sql-monk/batman/mechanical/cad/cable-modular-assembly.png

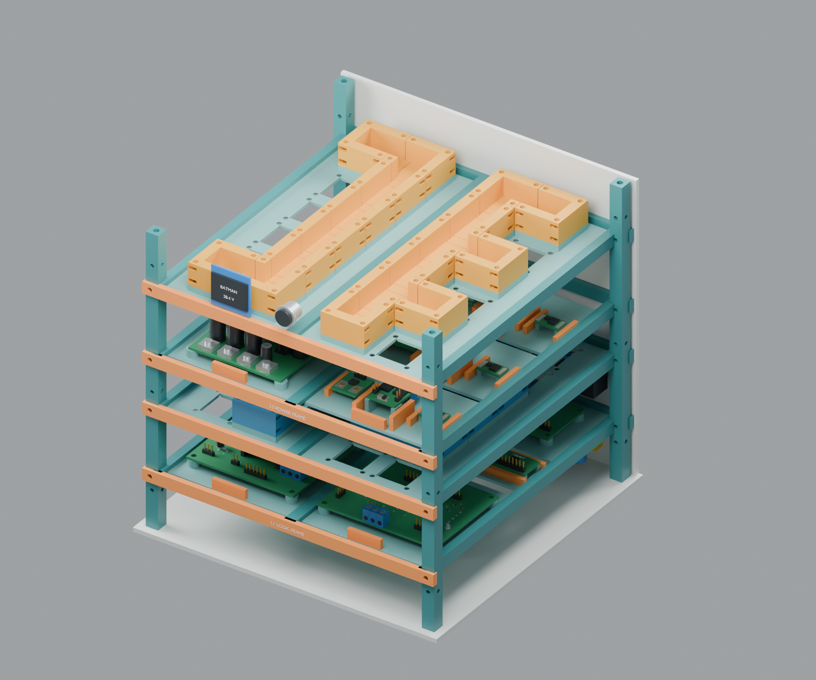
mechanical/cad/cable-modular-assembly.png
