sql-monk/batman/hardware/batman/reports/refinement/A/jumpers.csv

Ref | Net | A_X1_mm | A_Y1_mm | X2_mm | Y2_mm | Wire_cut_min_mm | End1 | End2
WA1 | +3V3 | 28.0 | 12.0 | 18.0 | 39.94 | 29.68 | existing pad | existing pad
WA2 | GND | 64.0 | 14.54 | 72.0 | 14.54 | 8.0 | existing pad | existing pad
WA3 | GND | 14.96 | 34.0 | 20.54 | 39.94 | 8.15 | existing pad | existing pad
WA4 | SCL | 64.0 | 17.08 | 72.0 | 17.08 | 8.0 | existing pad | existing pad
WA5 | SCL | 72.0 | 17.08 | 72.0 | 27.9 | 10.82 | existing pad | existing pad
