sql-monk/batman/docs/firmware.md

# Прошивка — вимоги

Що прошивка ESP32 має робити, у якому порядку і з якими порогами. Піни — connections.md, DPS — dps5015-modbus.md, вимірювання — measurement.md, протокол — protocol.md. Середовище: PlatformIO, Arduino-ESP32 (ESP-IDF під капотом); бібліотеки: `ModbusMaster`, `Adafruit_ADS1X15` або `RobTillaart/ADS1X15`, `OneWire` + `DallasTemperature`, `U8g2`, `ESPAsyncWebServer` або вбудований `WebServer`, `ArduinoJson`, `ESPmDNS`, `Update`.

## Безпечний старт

Порядок у `setup()` — саме такий:

1. Усі керуючі виходи (`SW1_ON`, `SW2_ON`, `K1`, `K2`) — `digitalWrite(LOW)` **до** `pinMode(OUTPUT)`; `SENS_PWR` — HIGH (датчики вимкнені). Апаратно все й так у OFF (Hi-Z + підтяжки), це лише підтвердження.
2. Watchdog задачі (10 с) і апаратний (30 с).
3. NVS: конфіг, лічильники, калібрування, збережений стан ключів і `sink`.
4. UART2, I2C 100 кГц; перевірити **обидва** ADS1115 (0x48, 0x49), OLED 0x3C, 1-Wire. Відсутній будь-який АЦП → вимірювання недійсні, автоматичний заряд не дозволяти; не підставляти нулі замість показань.
5. `SENS_PWR` ← LOW (датчики живляться), 100 мс, перший блок відліків.
6. DPS: читання блоку; якщо `ONOFF = 1` — негайно `ONOFF ← 0` (DPS міг лишитися ввімкненим після нашого ресету).
7. Відновлення стану ключів **з NVS**, якщо з моменту збереження минуло < 60 с (uptime із RTC-пам'яті ресету) — інакше обидва OFF. Заряд після ресету **не відновлюється** автоматично, стан → IDLE, подія `boot` з `restored`.
8. Wi-Fi (STA; якщо немає конфігу або 60 с без зв'язку — AP `batman-<id>` зі сторінкою налаштування), mDNS, HTTP-сервер, UDP-слухач.
9. Основний цикл.

Ресет не змінює стану ключів (перевірка в 4.1 плану).

## Задачі й пріоритети

| Задача | Період | Що |
|---|---|---|
| `acq` (ядро 1, високий пріоритет) | за готовністю ADS1115 (~470 Гц) | відлік → інтегрування → буфер середніх |
| `ctrl` (ядро 1) | 500 мс | Modbus-опитування, стейт-машина, перехресні перевірки, ключі |
| `load_acq` | 100 мс | ADS1115 0x49: A0 I_LOAD, A1 U_LOAD, по готовності кожного single-shot; обидва показання 10 Гц |
| `slow` (ядро 0) | 1 с | DS18B20, OLED, кнопка, NVS за розкладом |
| `net` (ядро 0) | за подіями | HTTP-сервер, телеметрія на sink, буфер, mDNS/UDP, OTA |

Доступ до спільних даних — через один м'ютекс на «знімок стану»; `acq` пише в подвійний буфер. Для 0x48/0x49 окремі об'єкти драйвера, спільні I²C-транзакції з OLED серіалізовані. GPIO34/39 NC, ADC ESP більше не використовується. У триконтактній ревізії немає FAULT ISR. **SENS_PWR = GPIO33 (J1.8), не GPIO14; GPIO14/J1.12 тепер NC.** Перед `pinMode(OUTPUT)` записати HIGH; LOW вмикає датчики. Прошивка зі старим призначенням GPIO14 не керуватиме живленням датчиків. Опитування струму не є незалежним швидким апаратним захистом. Q3 на C одержує SENS_PWR через CB2; на початку й після ввімкнення живлення датчиків не використовувати перехідні відліки.

## Стейт-машина

Стани верхнього рівня:

| Стан | Що відбувається | DPS | K1/K2 |
|---|---|---|---|
| `IDLE` | нічого не заряджається; ключі за командами/порогами | OFF | розімкнені |
| `CHG_B1_CC` / `CHG_B2_BULK` | постійний струм `i_cc` / `i_bulk` | ON, I-SET = профіль, U-SET підтягується за U_BX | KX замкнене |
| `CHG_B1_CV` / `CHG_B2_ABS` | утримання `u_cv` / `u_abs` на вузлі B; струм падає | ON | KX |
| `CHG_B2_FLOAT` | свинець: `u_float` з термокомпенсацією; без обмеження часу | ON | K2 |
| `REST` | пауза між зарядами (`policy.rest_min`) | OFF | розімкнені |
| `NO_INPUT` | БЖ відсутній (UIN < 30 В) | — | розімкнені |
| `FAULT` | аварія; підстан у `fault.code` | OFF | розімкнені |

Переходи:

| З | У | Умова |
|---|---|---|
| IDLE | CHG_Bx_* | команда `charge_start`, або `policy.auto` і гілка x — з найнижчим SoC (або за `charge_order`) і не в REST; **і** T_x у межах (`t_min`…`t_max`), **і** DPS ok, **і** UIN ≥ 31 В |
| CHG_B1_CC | CHG_B1_CV | U_B1 ≥ `u_cv` − 0,05 В (з ADS1115, середнє 2 с) |
| CHG_B1_CV | IDLE (`tail_current`) | I_B1 ≤ `i_tail` протягом 60 с → «100 %» (measurement.md), подія `cycle_complete` |
| CHG_B2_BULK | CHG_B2_ABS | U_B2 ≥ `u_abs_tc` − 0,05 В |
| CHG_B2_ABS | CHG_B2_FLOAT | I_B2 ≤ `i_abs_end` протягом 60 с, **або** 4 год у ABS (`timeout`) → «100 %» |
| CHG_B2_FLOAT | IDLE | команда, або інша гілка потребує заряду (`policy`), або 24 год |
| будь-який CHG | IDLE | команда `charge_stop`; T поза межами (`t_low` / `T_OVER` → FAULT, якщо > `t_max` + 5) |
| будь-який | NO_INPUT | UIN < 30 В або DPS не відповідає на UIN 3 рази |
| NO_INPUT | IDLE | UIN ≥ 31 В стабільно 10 с і DPS ok |
| будь-який | FAULT | PROTECT ≠ 0; DPS таймаут 3×; невідповідність стану DPS; `RELAY_STUCK` (струм у гілці при розімкненому K і вимкненому SW понад 0,3 А… при цьому SW не `forced`) |
| FAULT | IDLE | лише команда `fault_clear`, і лише якщо причина зникла |
| IDLE | REST | після завершення заряду, на `rest_min` хв |

Правила поверх таблиці:
- **Реле рухаються тільки при IOUT = 0 і ONOFF = 0** (dps5015-modbus.md). Ключі mSW — будь-коли.
- **Термокомпенсація свинцю:** `u_abs_tc = u_abs + tc × (T2 − t_ref)`, те саме для `u_float`; T2 відсутній → компенсація 0 і попередження `t_missing`.
- **LiFePO₄ нижче `t_min` (0 °C)** — заряд не стартує; якщо стартував і T1 впала — стоп (`t_low`).
- **Уставка за вузлом B:** U-SET підтягується так, щоб U_BX (ADS1115) = ціль; крок ≤ 0,05 В за 2 с; U-SET ніколи > `limits.u_set_max`; I-SET ніколи > `limits.i_set_max`.
- **Ключі розряду** (mSW): вручну (`switch`) і за порогами: `u_off` → OFF з подією `u_low`; назад — лише вручну або при `u_on` після заряду. Стан `forced` (повзунок ON) прошивка лише показує.
- **Заряд відрізаної гілки:** дозволено — це основний режим (заряджаємо ту, що не на навантаженні). Заряд гілки з увімкненим ключем теж дозволений (тоді частина струму йде в навантаження — облік чесний, бо датчик стоїть до розгалуження).

## Параметри (NVS, `GET/POST /config`)

| Ключ | За замовчуванням | Межі | Де використовується |
|---|---|---|---|
| `profile.lifepo4.i_cc` | 10,0 А | 0,5…12,0 | CC |
| `profile.lifepo4.u_cv` | 28,80 В | 27,0…29,4 | CV |
| `profile.lifepo4.i_tail` | 2,5 А | 0,2…5,0 | «100 %» |
| `profile.lifepo4.t_min` / `t_max` | 0 / 45 °C | | дозвіл заряду |
| `profile.pb.i_bulk` | 10,0 А | 0,5…12,0 | BULK |
| `profile.pb.u_abs` | 28,80 В | 27,0…29,8 | ABS |
| `profile.pb.u_float` | 27,40 В | 26,0…28,0 | FLOAT |
| `profile.pb.i_abs_end` | 1,3 А | 0,2…5,0 | «100 %» |
| `profile.pb.tc_v_per_c` | −0,036 В/°C | −0,06…0 | компенсація (−3 мВ/°C на банку × 12) |
| `profile.pb.t_ref` / `t_max` | 25 / 45 °C | | |
| `discharge.X.u_off` / `u_on` | 24,0 / 25,2 (Li); 23,0 / 24,6 (Pb) | | відсічка ключа |
| `bat.X.c_nom` | 50 / 65 А·год | | SoC |
| `policy.auto` | false | | автозаряд |
| `policy.charge_order` | `lowest_soc` | `lowest_soc` / `b1_first` / `b2_first` / `manual` | |
| `policy.rest_min` | 10 хв | 0…120 | REST |
| `sink.url`, `sink.interval_s` | —, 2 | 1…60 | телеметрія |
| `oled.timeout_s` | 120 | 10…3600 | гасіння екрана |
| `limits.i_set_max` / `u_set_max` | 12,0 / 29,8 | **не змінюються** | стеля заліза |

Усі пороги мають гістерезис або витримку (60 с на струм хвоста, 10 с на UIN, 5 с на струм у вимкненій гілці) — щоб один викид не перемикав стан.

## FAULT і попередження

Коди — protocol.md. У FAULT: обидва SW_ON ← 0 (крім `forced`, там фізично не можемо), DPS ONOFF ← 0, реле вимикати за правилами безструмової комутації; поведінка при неможливості підтвердити нульовий струм лишається умовою допуску з hardware/README.md. OLED показує код, подія йде в сервіс. `OC_LATCH` зарезервований і не генерується: апаратної лінії FAULT від mACS немає. `fault_clear` не виконує автоматичний цикл живлення датчиків. Попередження не змінюють стан — лише масив `warn` і подія при появі/зникненні.

## OLED і кнопка

Екрани (кнопка — наступний; утримання 2 с — назад на перший): 1) стан + U/I обох гілок + SoC; 2) заряд: стан, U-SET/I-SET, UOUT/IOUT, час у стані; 3) лічильники циклу й загальні; 4) температури, U_LOAD/I_LOAD; 5) Wi-Fi: SSID, IP, RSSI, sink, буфер; 6) FAULT/warn — лише коли є. Гасіння за `oled.timeout_s`, будь-яке натискання будить; кожні 10 хв зсув картинки на 1 px по колу (випалювання). Утримання 5 с на екрані 1 — `charge_stop` + обидва ключі OFF (аварійна кнопка без телефона).

## Wi-Fi, телеметрія, OTA

- STA з реконектом (експоненційно 1…60 с); без конфігу — AP + captive-сторінка (SSID, пароль, IP сервісу опційно).
- mDNS + UDP-відповідач (protocol.md); HTTP на 80.
- Телеметрія — окрема задача, не блокує `ctrl`; таймаут POST 3 с; буфер за protocol.md.
- OTA через `POST /update` (перевірка розміру й magic-байта, `Update.end(true)`), а також ArduinoOTA у локальній мережі для розробки. Під час OTA стейт-машина в поточному стані заморожується, DPS не чіпаємо; після ресету — безпечний старт.
- Час: NTP лише для OLED/журналу.

## Журнал і діагностика

UART0 115200: рівні `E/W/I/D`, теги за задачами; `GET /status` віддає `heap`, `min_heap`, `uptime`, `reset_reason`, лічильники CRC-помилок Modbus, втрат телеметрії, переповнень буфера. Раз на годину — рядок `I` з усіма лічильниками (для кроку 4.8 плану: тиждень без витоку heap).

## Версія і збірка

`fw` — semver у `version.h`, автоінкремент build-номера скриптом PlatformIO; у телеметрії та mDNS TXT. `platformio.ini`: `board = esp32dev`, `monitor_speed = 115200`, розділ прошивки з OTA (`partitions = min_spiffs.csv` або `default.csv`).
