sql-monk/batman/docs/plan.md

# План робіт

П'ять потоків — документація, схема й плати, корпус, прошивка, сервіс — ідуть з перекриттям: корпус не можна креслити без обмірів, плати — без таблиці з'єднань, сервіс — без протоколу телеметрії. Кожен крок має «готово, коли…».

## 0. Підготовка

Розміри модулів обміряні й внесені в [components.md](components.md) (✔, ± 0,3 мм); DPS5015 (всі три) відповідають по Modbus; поведінка ключів mSW і реле K1/K2 перевіряється по ходу на стенді (крок 7.1–7.2, бланк у tests.md). Лишається одна окрема перевірка — метрологічна, бо від неї залежить схема плати A.

### 0.1 Шум і «танець» нуля на ACS711EX + ADS1115

Дюпонами, ще без плат. Датчики шумлять, а без струму показання гуляють біля нуля й ніколи не стоять у нулі (підтверджено на столі); це дві різні біди, і лікуються вони по-різному:

- **шум** (випадковий, симетричний) для підрахунку А·год майже нешкідливий: при інтегруванні плюси й мінуси взаємно знищуються. Псує показання на OLED і графіках — тобто це косметика;
- **зсув нуля і його дрейф** (систематичний) — головний ворог лічильника: 30 мА зсуву дають **0,7 А·год за добу** з повітря.

План, по черзі; кожен наступний крок — лише якщо попередніх не вистачило:
1. **RC на виході VIOUT:** 1 кОм послідовно + 1 мкФ на землю (замість самого лише 100 нФ) — зріз ≈ 160 Гц замість смуги датчика 100 кГц. 1 кОм не заважає ADS1115 (він хоче джерело ≤ 10 кОм).
2. **Усереднення в прошивці:** ADS1115 475 SPS, 4 канали по колу → ≈ 120 вибірок/с на канал; ковзне середнє за 0,5–1 с — **для показу**; в інтегрування йдуть усі вибірки без відкидання.
3. **Автонуль** (уже в концепції): коли ключ гілки розімкнений, заряд не на ній і логіку живить інша гілка — струм гарантовано нульовий, прошивка повільно (постійна часу — хвилини) підтягує збережений зсув.
4. **Мертва зона — обережно.** Спокуса «менше 100 мА вважати нулем» знищує рівно те, що ми хочемо порахувати: логіка живиться з вузла B і їсть 50–100 мА цілодобово, тобто 1–2 А·год на добу. Тому **в інтегруванні мертвої зони немає взагалі**; вона дозволена тільки на екрані (показувати «0,00 А», поки |I| < 20 мА).
5. **План Б — інший принцип,** якщо після кроків 1–3 σ за 1 с > 20 мА або дрейф > 30 мА за добу: розглянути шунт 5 мОм (50 мВ при 10 А, 0,5 Вт) і диференціальний ADC. Це окрема переробка з перевіркою синфазних рівнів і від'ємної напруги на кожному вході, не готова опція поточної B. ADS 0x49 уже зайнятий каналами навантаження, A2/A3 заземлені. INA3221 зі штатними шунтами не підходить за діапазоном напруги шини та струму.

Що записати в `tests.md`: 10 хв запису при гарантовано нульовому струмі — до і після RC (σ і розмах); те саме через 12 год (дрейф); звірка на 5 А проти DSN-VC288 і телеметрії DPS.

⚠ У драйвері, з якого переносимо код (`plumbum-power-backup/esp-web/config.h`), стоять `ACS711_SENSITIVITY 0.185` і `ACS711_ZERO_OFFSET 2.5` — це числа ACS712 від 5 В. Для **ACS711EX від 3,3 В** правильні **0,090 В/А** і нуль **VCC/2 = 1,65 В**. Не скопіювати помилку.

Готово, коли результати записані в `docs/tests.md` і вирішено, чи потрібна переробка аркуша sense та аналогової плати B.

## 1. Документація

Мета: документації достатньо, щоб зібрати пристрій, спроєктувати корпус, написати прошивку й сервіс, не звертаючись до цієї розмови. Кожне число записане один раз у «своєму» файлі.

| Крок | Файл | Що всередині | Готово, коли |
|---|---|---|---|
| 1.1 | `docs/README.md` | зміст, правило «одне число — одне місце», система позначень (mDPS, mSW1/mSW2, mREL2·K1, вузли B1/B2/LOAD, сигнали I_B1…) | позначення узгоджені й використані далі без винятків |
| 1.2 | `docs/components.md` | кожен модуль: роль, характеристики, розміри, отвори, розпіновка, монтаж, кількість; базові компоненти з номіналами | усі розміри ✔ або 🌐 |
| 1.3 | `docs/connections.md` | вузли; таблиця силових кіл (№, від, до, переріз, струм); гілка заряду; живлення логіки; сигнали (аналог, I2C, UART, 1-Wire, GPIO); розкладка пінів ESP32; шкала АЦП; мінуси | кожен провід має номер, кожен GPIO — одну лінію; жоден пін не задіяно двічі, strapping/flash-піни вільні |
| 1.4 | `docs/measurement.md` | канали, PGA, частота вибірки, калібрування нуля й масштабу (ручне + автонуль), формули SoC і хвоста заряду, що і як часто зберігається в NVS | прошивку можна писати без здогадок |
| 1.5 | `docs/protocol.md` | протокол пристрій ↔ сервіс: mDNS/UDP-пошук, `POST /sink`, формат JSON телеметрії та подій, REST-API пристрою, коди помилок, версіонування | прошивку й сервіс можна писати паралельно за цим файлом |
| 1.6 | `docs/firmware.md` | вимоги: безпечний старт (усі керуючі виходи у LOW до `pinMode`), стейт-машина заряду (вибір акумулятора, профілі, комутація без струму, зникнення U_in), ключі, FAULT, watchdog, OLED/кнопка, Wi-Fi/телеметрія, OTA, пороги як параметри NVS | таблиця станів і переходів повна; пороги в одній таблиці |
| 1.7 | `docs/service.md` | вимоги до сервісу: пошук і реєстрація пристроїв, схема БД, агрегати, сторінки, експорт, сповіщення, розгортання на Windows і RPi4 | можна писати код |
| 1.8 | `docs/enclosure/requirements.md` | що вмістити, тепло, доступ, розділення силового/сигнального, правила друку (≤70 % прилягання, час друку, змінність частин) | корпус можна проєктувати з нуля лише за цим файлом |
| 1.9 | `docs/tests.md` | протоколи стендових і приймальних перевірок | результати кроків 0.1 і 7 записані |
| 1.10 | `docs/dps5015-modbus.md` | карта регістрів DPS5015 (0x00 U-SET … 0x09 ON/OFF, усе × 100), налаштування порту (9600 8N1, адреса 1), обов'язкова послідовність «вимкнути вихід → дочекатися підтвердження → рухати реле», таймаути й поведінка при обриві; що беремо з `sql-monk/plumbum-power-backup` і чого звідти **не** копіюємо (числа ACS712 замість ACS711EX) | крок 4.4 пишеться за цим файлом, не відкриваючи старий код |

Порядок: 1.1 → 1.2 → 1.3 → 1.4 → 1.5 → 1.6 і 1.7 → 1.8; 1.9 наповнюється по ходу; 1.10 можна писати хоч зараз — усі дані вже є.

## 2. Принципова схема, потім плати (ЛУТ)

### 2.1 Схема (KiCad, `hardware/batman/`)

Створена у єдиному проєкті `hardware/batman/batman.kicad_pro`: кореневий аркуш і шість робочих (power, charge, sense, logic, supply3, supply5). ERC і звірка з PCB проходять без порушень. Як правити й перевіряти — [hardware/README.md](../hardware/README.md). Зміна з'єднання = правка connections.md і `hardware/circuit.py`. Назви без кінцевого номера мають суфікс `1` у KiCad та початкову назву в Alias.

### 2.2 Плати

**Правила ЛУТ** — за практикою, менше просто не виходить:

- один шар; доріжки **сигнальні ≥ 0,7 мм**, силові ≥ 3 мм із пропайкою припоєм;
- **зазор ≥ 0,5 мм** будь-де;
- **без масок** (паяльної, пасти) і без шовкографії на міді; максимум — підписи гребінок/клемників на стороні деталей (окремий відбиток F.SilkS без дзеркала або маркер); перехідних отворів немає — лише перемички дротом;
- **пади й отвори — під конкретний компонент, а не «однакові для всіх»**: у резистора ніжка тонка, у силового діода — лапа. Правило: отвір = діаметр виводу + 0,2–0,3 мм; пад = отвір + 1,2 мм по діаметру, але не менш як 2 мм.

| Що саджаємо | Вивід | Отвір | Пад |
|---|---|---|---|
| керамічні конденсатори, гребінки 2,54 | 0,5–0,6 мм | 0,8 мм | 2,0 мм |
| Шотткі 1N5819 / SS34, TVS, дротяні перемички | 0,8–0,9 мм | 1,1 мм | 2,4 мм |
| силові діоди TO-220 | 1,0–1,2 мм | 1,3 мм | 3,0 мм |
| клемники 5 мм, силові клеми | 1,2–1,4 мм | 1,5 мм | 3,5 мм (силові — з заливкою) |
| SMD 1206 (усі резистори 0,25 Вт) | — | — | два пади 2,0 × 1,6, проміжок 1,8 |

Резистори — виключно SMD 1206, без свердління (щоб не свердлити вручну 36 отворів на платі A); суміщені SMD/THT місця для них більше не робимо.

- перемички дротом допускаються; на виході — дзеркальний PDF 1:1 і окремий шаблон свердління з переліком діаметрів.

| Плата | Що на ній | Розмір | Навіщо саме плата |
|---|---|---|---|
| **A — ESP** | DevKitC, два I²C-порти ADS, одна пара підтяжок, периферія, NPN реле | 80 × 80 | основна плата без аналогових входів |
| **B — analog** | шість аналогових входів, дільники/RC, виходи J32/J33 | 90 × 70 | аналог до окремих ADS; немає I²C і посадок ADC |
| **C — 3V3** | розподільні роз'єми, Q3 живлення датчиків, розв'язка | 45 × 35 | готові 3,3 В від DevKitC, не стабілізатор |
| **D — 5V** | розподіл 5 В, NT1 живлення реле, діодне «АБО» перед LM2596 | 65 × 40 | LM2596 зовнішній |
| **Вузол шин, без PCB** | LOAD+/GND, C1/C2 навісно, D3 DNP | за фактичними клемами | не плутати з новою аналоговою B |

**Поточний стан:** чотири PCB в [одному KiCad-проєкті](../hardware/batman/batman.kicad_pro). ERC, DRC/паритет і локальні DRC чисті. B.Cu, 0,7/0,5 мм, без via; WA1–WA4 на A, B/C/D без перемичок; 175 отворів. П'ять міжплатних кабелів CB2–CB6 (13 жил), чотири кабелі ADS (16 жил), локальні з'єднання на ADS. Обидва ADS тепер зовнішні, адреси/канали/GPIO не змінено. J20/J21 на A, J32/J33 на B; старий CB1 прибрано, CB3 двоконтактний. PDF 1:1, BOM, свердління й кабелі у комплекті. Модель mACS, посадки, бюджет живлення та стендові перевірки — умови допуску: [hardware/README.md](../hardware/README.md). Генератор не запускати поверх ручних правок.

Порядок: прозвонка D і LM2596 → A → C/B → зовнішні ADS і обидві адреси I²C → датчики. Кожне нове підключення без живлення, початкові перевірки без батарей, від джерела з обмеженням струму. Не подавати аналогові напруги на знеструмлені ADS. Буфер C1/C2 навісний.

**Роз'єми — дюпони.** Логічні роз'єми плати A — гребінки 2,54: **прямі або кутові** за місцем (кутові — там, де над платою мало простору або джгут іде вбік), **а на дроті — тільки прямі корпуси DuPont**. Силові зовнішні шини використовують силові клеми, не DuPont. Над кожною прямою гребінкою ≥ 30 мм (корпус дюпона ~15 мм + радіус згину джгута), перед кутовою ≥ 25 мм убік. Гребінки групуємо за призначенням (датчики, реле, UART, I2C, 1-Wire) і підписуємо.

### 2.3 BOM — комплектувальний список (`hardware/bom/bom.md`)

Машинний BOM генерується зі схеми: позначення, кількість, власник A/B/C/D або зовнішній монтаж. Другий ADS1115 і додаткові роз'єми/конденсатори перевірити в наявності або придбати; статус комплектації ведеться в Markdown BOM.

## 3. Корпус (3D-друк)

### 3.1 Принцип

- **Playground:** плоска **основа** з регулярною матрицею отворів (крок 10 мм) під вставки M3; жоден модуль не кріпиться до основи напряму — кожен стоїть на власній **змінній панельці** (пластина 2 мм + стійки 5 мм), яку тримають 1–2 гвинти в матрицю. Інший модуль = інша панелька (грами пластику, хвилини друку).
- **Стінки — окремі плоскі плити**, що заходять у пази основи й **прикручені гвинтами M3**: кожна плита тримається 2–3 гвинтами M3 у кутові стійки, а самі стійки стоять на матриці основи (теж M3). Паз лише позиціонує, тримають гвинти. Передня (OLED, кнопка, USB) і задня (клеми, запобіжники) панелі знімаються окремо від бічних, не розбираючи корпус.
- **Кришка** — плоска решітка; корпус працездатний і без неї.
- **Запас місця:** ≥ 15 мм над найвищим модулем; ≥ 12 мм за кожною клемою й тримачем запобіжника під дроти; ≥ 3 мм між панельками; зона резерву ~1/4 площі (другий DPS5015, другий комплект реле при масштабуванні).
- **Місце під дюпони:** уся логіка підключається дюпонами, на дроті — тільки прямі корпуси. Тому над кожною **прямою** гребінкою — **≥ 30 мм** вільної висоти (корпус ~15 мм + радіус згину джгута), перед **кутовою** — ≥ 25 мм убік плюс канал, куди джгут піде далі. Де 30 мм не набирається (наприклад під кришкою над платою A) — на модулі ставимо кутову гребінку: обидва типи є в наявності. Джгути сигналки йдуть своїм лотком, окремо від силових дротів.
- **Друк:** усі деталі — плити, низом на стіл (прилягання 90–100 %, вимога ≥ 70 %); без підпорок; плити 3 мм; пріоритет міцність → час друку → філамент; PETG.
- **Тепло:** DPS5015 має власний вентилятор — не накривати. Він маленький, але працює й тримає немало, тож від нього не відмовляємось; **у корпусі закладаємо можливість заміни, а не заміну**: у стінці навпроти радіатора DPS — отвір Ø45 мм і 4 отвори під M4 з міжцентровими **40 × 40 мм** під наявний вентилятор **50 × 50 (5 В)**, поруч місце під його живлення (5 В з mDC5 або з фанового роз'єму DPS). Поки вентилятор не потрібен — отвір закритий друкованою заглушкою-решіткою. Ставимо тільки якщо тепловий тест (крок 7.3) покаже потребу. XL74610 при ≤ 10 А — пасивно; впускні щілини знизу бічних стінок, вихід — решітка кришки.

### 3.2 Кроки

| Крок | Що | Готово, коли |
|---|---|---|
| 3.2.1 | `docs/enclosure/requirements.md` (крок 1.8) | є список того, що вмістити, з розмірами з components.md |
| 3.2.2 | **2D-компонування** (SVG у `docs/enclosure/figures/`): вигляд згори з панельками, зонами дротів, силовим і сигнальним трактами; передня й задня панелі | усі модулі стоять, кожен дріт має шлях, зони дротів не перетинають модулі |
| 3.2.3 | **Модель** у Blender (`mechanical/cad/`): по одному файлу на вузол (основа, стінки, панелі, панельки, кришка), майстер-збірка лінками; габарити модулів окремою колекцією для перевірки перетинів | скрипт перевірки: без перетинів, прилягання ≥ 70 % для кожної деталі, габарит ≤ 226 мм |
| 3.2.4 | **Тестові друки** (по 5–20 хв): фрагмент матриці зі вставкою M3; панелька під ACS711EX; кут «паз основи + стінка + стійка + два гвинти M3»; тримач XL74610 (кишеня 17 × 10 з каналом під два дроти); фрагмент стінки з посадкою вентилятора 50 × 50 і заглушкою; гребінка 2,54 з надітим дюпоном — перевірити, що 30 мм вистачає | посадки підігнані, допуски записані в requirements.md |
| 3.2.5 | **Друк основи + задньої панелі** → на них макетна збірка силової частини (це і є стенд для кроку 7) | силова частина стоїть на основі, дроти прокладені |
| 3.2.6 | **Решта стінок, панельки логіки, кришка** | усе стоїть, кришка сідає |
| 3.2.7 | **Звіт про друк:** для кожної деталі — габарит, об'єм, час друку зі слайсера (Bambu Studio), прилягання | сумарний час відомий; найдовші деталі переглянуті на предмет спрощення |

## 4. Прошивка ESP32 (`firmware/`)

Середовище: PlatformIO + Arduino-ESP32 (або ESP-IDF — вирішити на кроці 4.1 за наявними бібліотеками Modbus/ADS1115/mDNS). Кожен крок закінчується працездатним стендом.

| Крок | Що | Готово, коли |
|---|---|---|
| 4.1 | Каркас: безпечний старт (усі керуючі виходи у LOW до `pinMode`; і без цього у ресеті ON-піни ключів у нулі, бази NPN на землі — усе OFF; відновлення стану з NVS), watchdog, конфіг у NVS, лог у UART | ресет не змінює стан ключів; параметри переживають перезавантаження |
| 4.2 | Два ADS1115: 0x48 гілки, 0x49 навантаження; DS18B20, калібрування, автонуль; ADC ESP не використовується | обидві адреси доступні, канали не переплутані, звірка з еталоном у межах 1 % |
| 4.3 | Підрахунок Ah/Wh, SoC, збереження в NVS | 1 год заряду: розбіжність із телеметрією DPS ≤ 2 % |
| 4.4 | Modbus RTU до DPS5015: перенесення перевіреного драйвера з `plumbum-power-backup` на апаратний UART2 ESP32 (замість `SoftwareSerial`), читання/запис, ON/OFF, детектор зникнення U_in | керування з консолі працює, обрив UART не вішає прошивку |
| 4.5 | Стейт-машина: ключі mSW1/mSW2 (виявлення повзунка, примусово поставленого в ON), реле K1/K2 тільки без струму, профілі LiFePO₄/свинець із замкненою уставкою по U_B, термокомпенсація, хвіст заряду, черговість, FAULT, аварійні стани | повний цикл заряду обох акумуляторів без втручання |
| 4.6 | OLED і кнопка: екрани стану, лічильників, Wi-Fi/сервісу; захист від випалювання | |
| 4.7 | Wi-Fi: підключення до мережі (провізія через AP-сторінку), mDNS, UDP-відповідь на пошук, REST-API, `POST /sink`, відправка телеметрії й подій, буфер на випадок недоступності, OTA | сервіс знаходить пристрій і отримує потік |
| 4.8 | Витривалість: тиждень безперервної роботи, перевірка втрат пакетів, стабільності heap, поведінки при обриві Wi-Fi/сервісу | |

## 5. Сервіс збору й аналітики (`service/`)

Python 3 + FastAPI + SQLite; один процес; Windows (служба через NSSM або Task Scheduler) і Raspberry Pi 4 (systemd); опційно Docker.

| Крок | Що | Готово, коли |
|---|---|---|
| 5.1 | Каркас: конфіг, БД (міграції), запуск як служба на Windows і RPi4 | стартує на обох платформах |
| 5.2 | Пошук пристроїв: mDNS-браузер, UDP-broadcast, ручний IP; реєстрація; `POST /sink` на пристрій з адресою приймача | пристрій у списку, потік іде |
| 5.3 | Приймання телеметрії й подій, зберігання сирих зразків, контроль втрати зв'язку | БД росте, розриви позначаються |
| 5.4 | Агрегати: година/доба/цикл — Ah/Wh у та з кожного акумулятора, цикли, ефективність, час у станах, мін/макс напруг і температур; проріджування сирих даних старше N днів | запити віддають готові таблиці |
| 5.5 | Вебінтерфейс: стан пристроїв, графіки (U/I/SoC/T), таблиці циклів, події, експорт CSV | |
| 5.6 | Керування: пересилання команд і налаштувань на пристрій (заряд, ключі, пороги, калібрування) | |
| 5.7 | Сповіщення: FAULT, втрата зв'язку, низький SoC (спочатку — журнал і e-mail/Telegram за бажанням) | |

## 6. Послідовність у часі

```
1.1–1.3 (README, components, connections) ─┬─→ 2.1 схема ─→ 2.2 плати A–D ─→ виготовлення ──────────────┐
0.1 шум датчиків ──────────────────────────┘        │                                                       │
                      ├─→ 1.4 measurement ─→ 4.1–4.5 прошивка (ядро) ─────────────────────────────────────┤
                      │                                                                                   │
                      ├─→ 1.5 protocol ─┬─→ 4.7 прошивка (Wi-Fi, API) ───────────────────────────────────┤
                      │                 └─→ 1.7 service ─→ 5.1–5.5 сервіс ───────────────────────────────┤
                      │                                                                                   │
                      └─→ 1.8 → 3.2.2 компонування → 3.2.3 модель → 3.2.4 тести → 3.2.5 основа ───────────┘
                                                                                                          └─→ 7 стенд, калібрування, приймання
```

Прошивку й сервіс можна розробляти паралельно з виготовленням A–D. Перед комплектацією підтвердити другий ADS1115 і нові роз'єми; корпус — після перевірки посадок. Паралельно виконати 0.1 шум датчиків і 4.4 Modbus на столі.

## 7. Стенд, калібрування, приймання

1. Силова частина на основі: гілки, ключі mSW, діоди, шина; заряд одного акумулятора вручну з DPS5015 (без реле) — перевірка профілю. Тут же — поведінка mSW (повзунок / пін ON / ресет ESP32, падіння при 5 А) і реле K1/K2 через NPN (без деренчання, OFF у ресеті, +5V при обох обмотках) — бланк у tests.md.
2. Плати A–D й зовнішні шини: керування реле, Modbus, обидва ADS1115; калібрування; звірка Ah за 1 год заряду з телеметрією DPS (≤ 2 %).
3. Повний цикл: заряд Bat1 → Bat2 → розряд на навантаження ~100 Вт → лічильники на пристрої збігаються з агрегатами сервісу; тепловий тест 1 год при 10 А заряду під кришкою (разом із температурою корпусу реле K1/K2 і падінням на замкненому контакті — норма до ~100 мВ) — тут же вимірюємо **падіння й нагрів XL74610 при 5 і 10 А** і вирішуємо, чи потрібен вентилятор 50 × 50 замість штатного.
4. Тиждень роботи з сервісом: без втрат телеметрії й зависань.
5. Результати — у `docs/tests.md`; що змінилося — в components/connections/concept.
