sql-monk/batman/hardware/batman/reports/clean-routing/before-publish-20260909-212552/reports/previews/copper-top-view.png

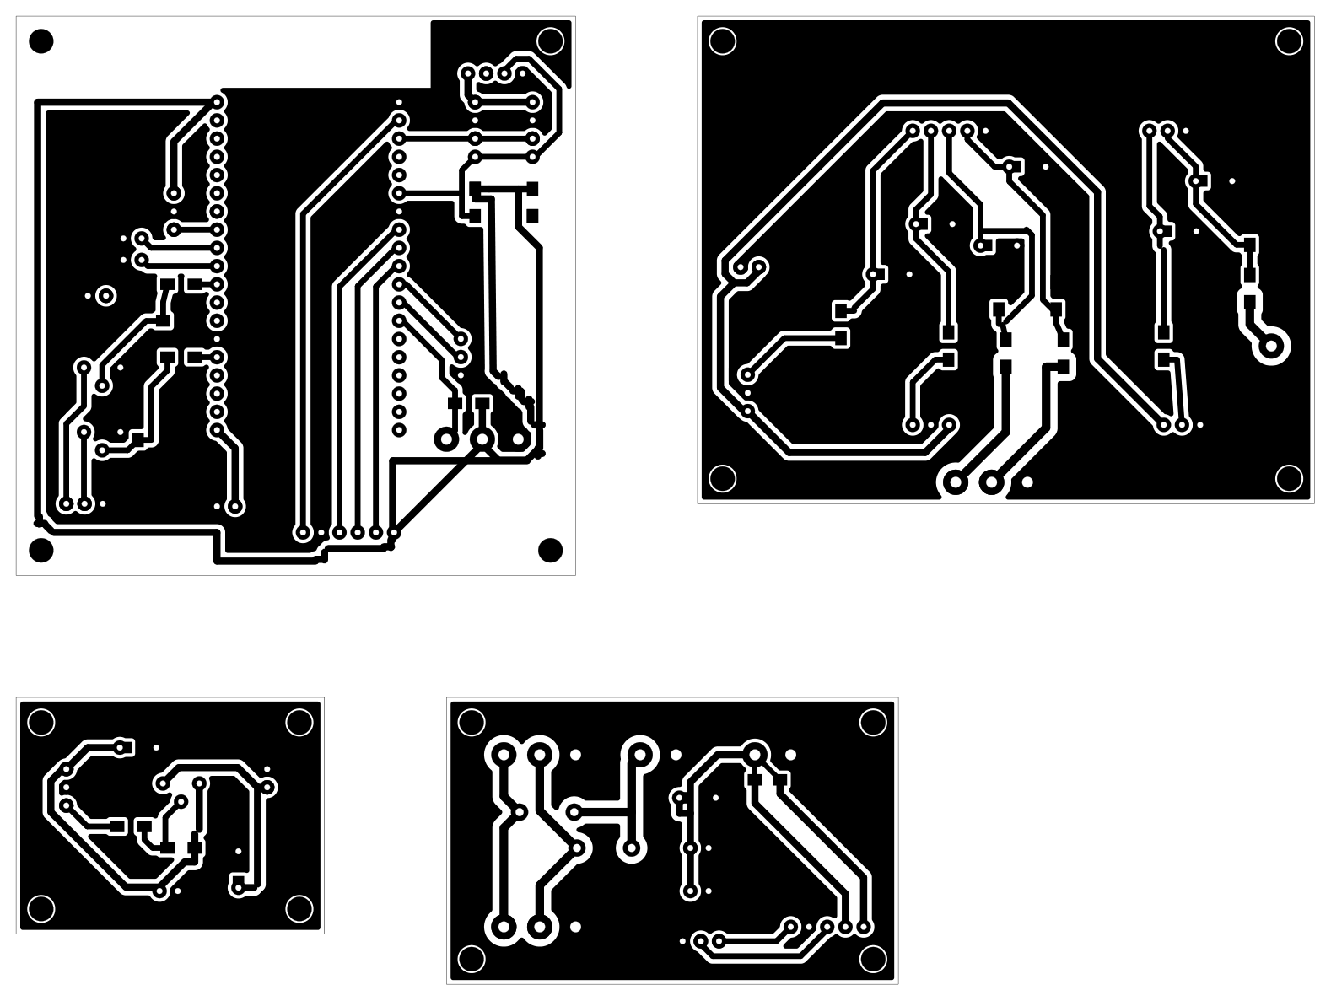
hardware/batman/reports/clean-routing/before-publish-20260909-212552/reports/previews/copper-top-view.png
