sql-monk/batman/hardware/batman/reports/clean-routing/staged/reports/previews/A-copper-mirrored.png

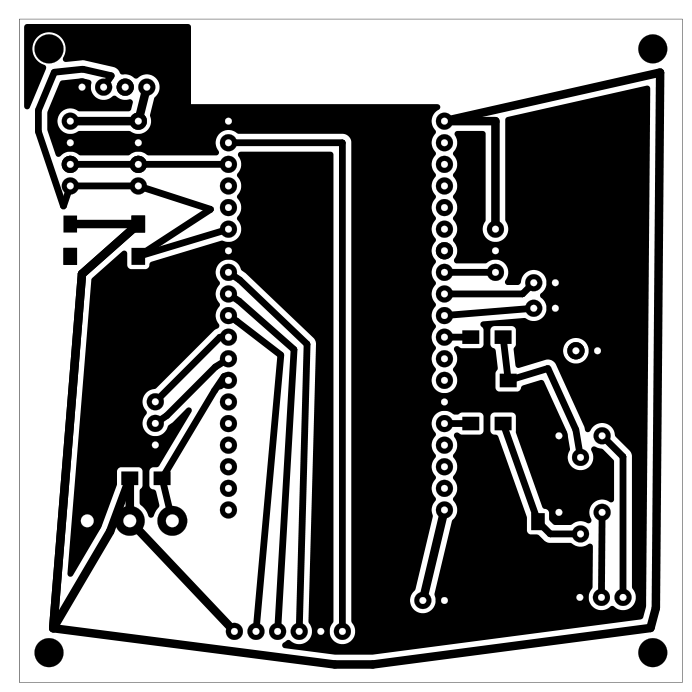
hardware/batman/reports/clean-routing/staged/reports/previews/A-copper-mirrored.png
