sql-monk/batman/hardware/batman/reports/clean-routing/staged/reports/previews/A-copper-top-view.png

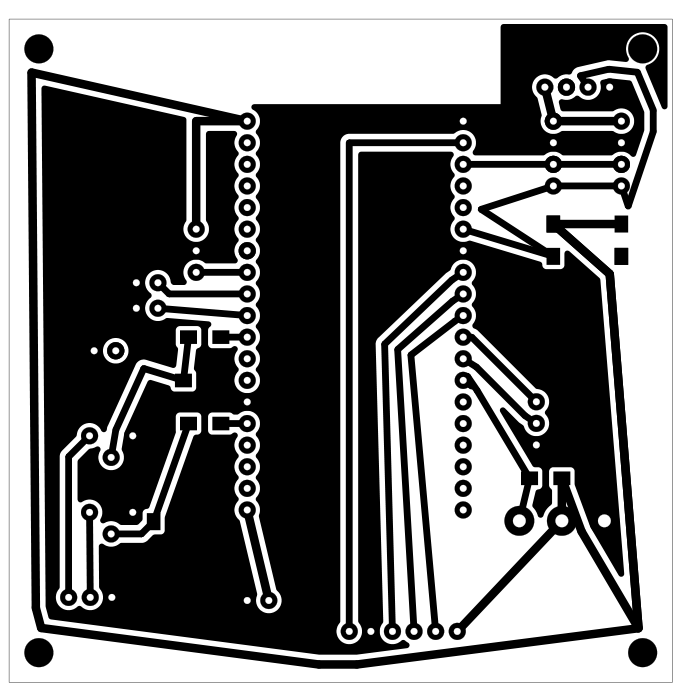
hardware/batman/reports/clean-routing/staged/reports/previews/A-copper-top-view.png
