sql-monk/batman/hardware/batman/reports/clean-routing/staged/reports/previews/B-copper-mirrored.png

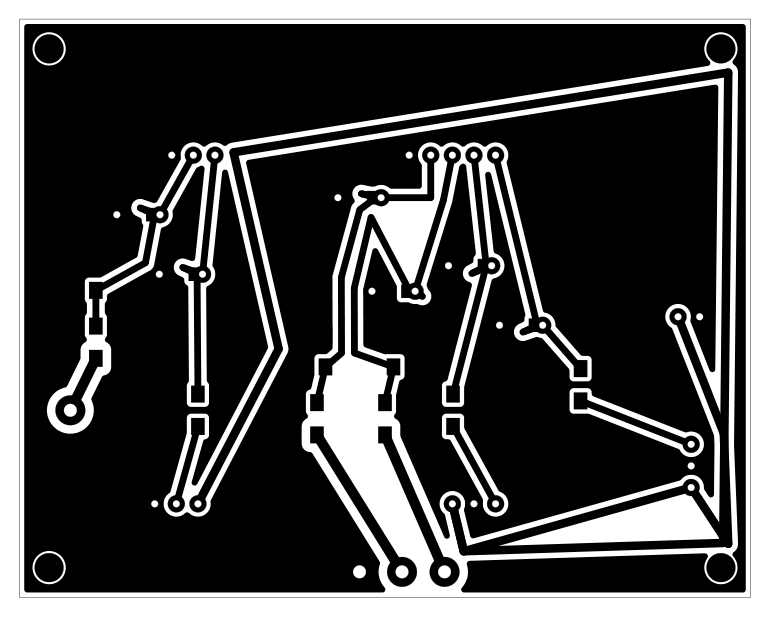
hardware/batman/reports/clean-routing/staged/reports/previews/B-copper-mirrored.png
