sql-monk/batman/hardware/batman/reports/clean-routing/staged/reports/previews/C-copper-mirrored.png

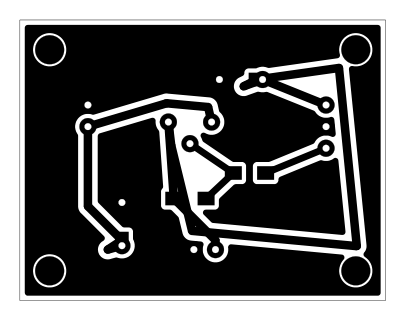
hardware/batman/reports/clean-routing/staged/reports/previews/C-copper-mirrored.png
