sql-monk/batman/hardware/batman/reports/clean-routing/staged/reports/previews/C-copper-top-view.png

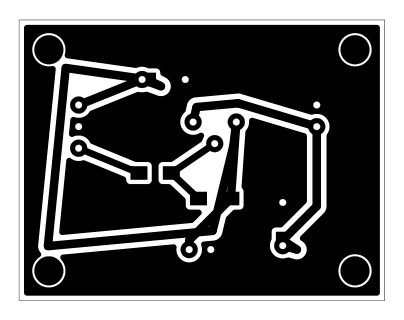
hardware/batman/reports/clean-routing/staged/reports/previews/C-copper-top-view.png
