sql-monk/batman/hardware/batman/reports/clean-routing/staged/reports/previews/D-copper-mirrored.png

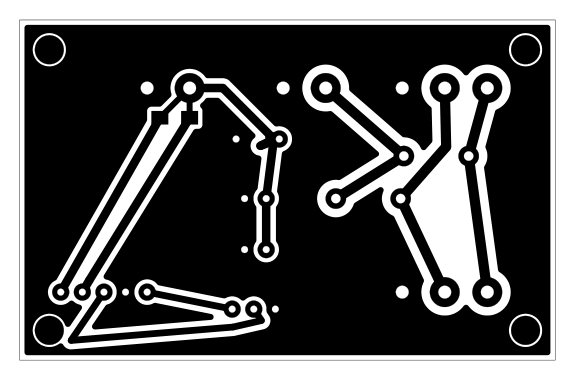
hardware/batman/reports/clean-routing/staged/reports/previews/D-copper-mirrored.png
