sql-monk/batman/hardware/batman/reports/clean-routing/staged/reports/previews/D-copper-top-view.png

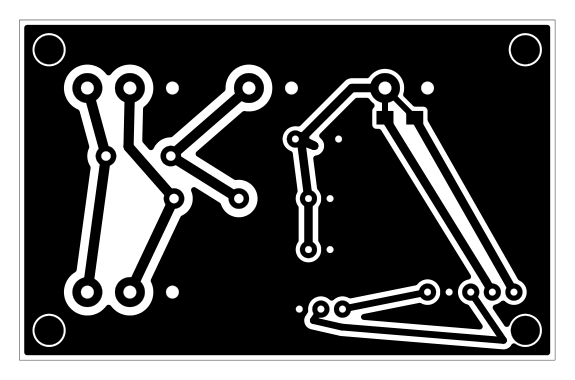
hardware/batman/reports/clean-routing/staged/reports/previews/D-copper-top-view.png
