sql-monk/batman/hardware/batman/reports/clean-routing/staged/reports/previews/schematic-1.png

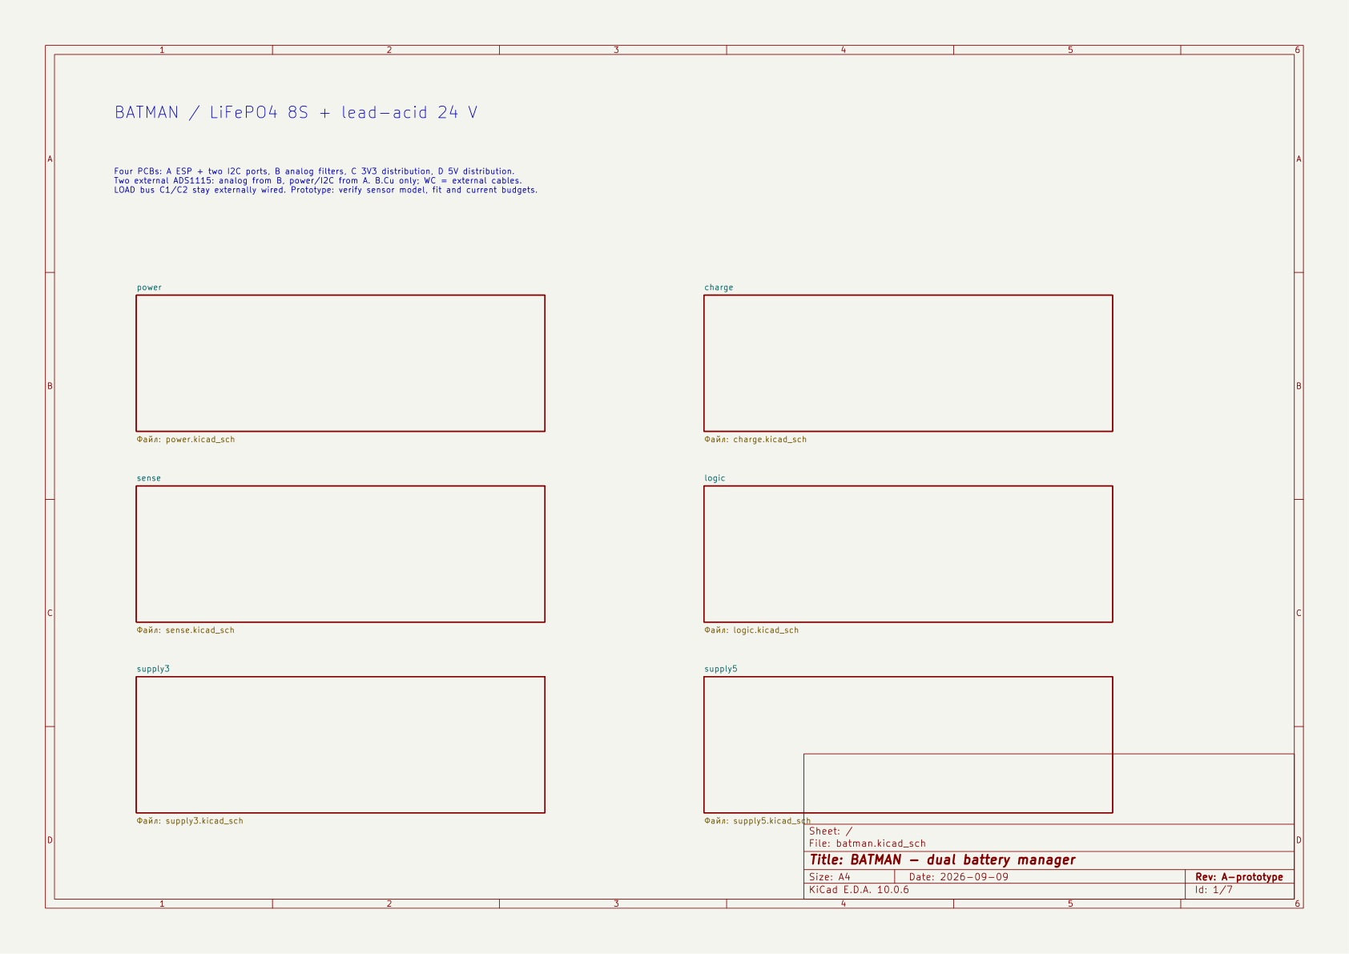
hardware/batman/reports/clean-routing/staged/reports/previews/schematic-1.png
