sql-monk/batman/hardware/batman/reports/gpio33/before-publish-20260909-184347/reports/previews/A-copper-mirrored.png

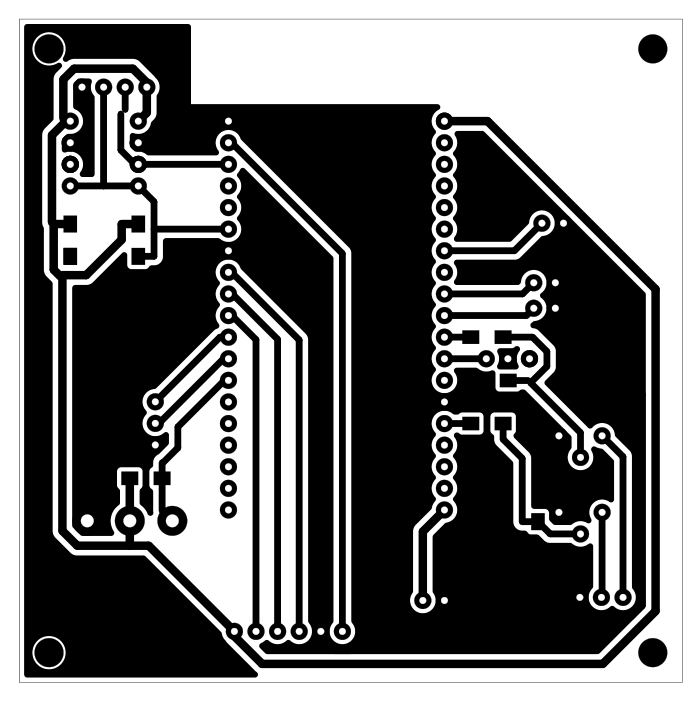
hardware/batman/reports/gpio33/before-publish-20260909-184347/reports/previews/A-copper-mirrored.png
