sql-monk/batman/hardware/batman/reports/layout-review.png

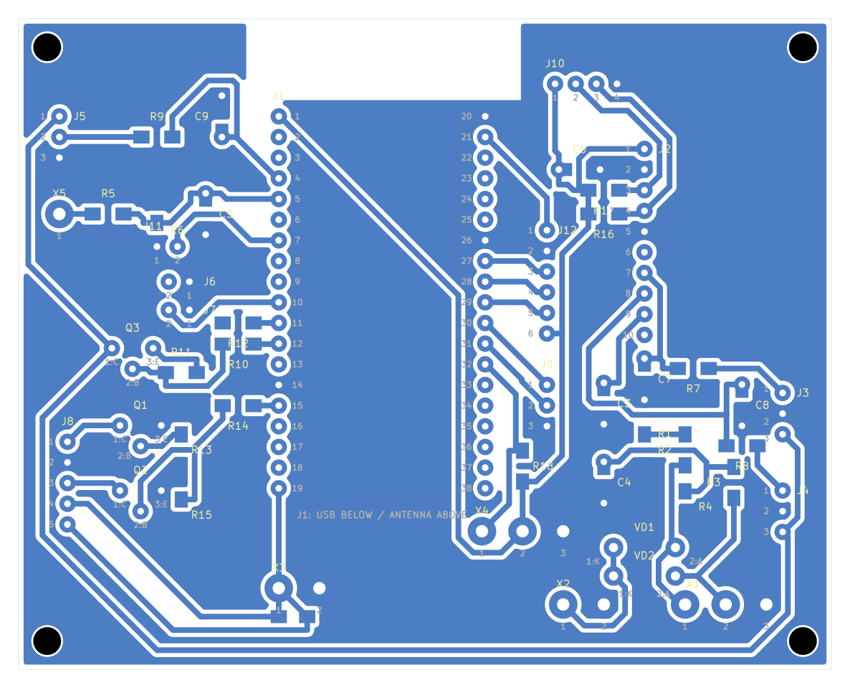
hardware/batman/reports/layout-review.png
