sql-monk/batman/hardware/batman/reports/previews/A-copper-mirrored.png

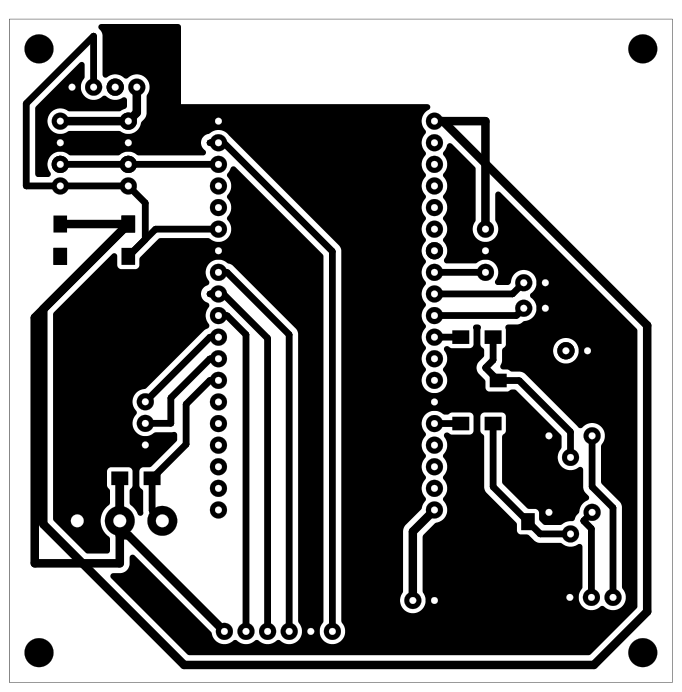
hardware/batman/reports/previews/A-copper-mirrored.png
