sql-monk/batman/hardware/batman/reports/previews/A-copper-top-view.png

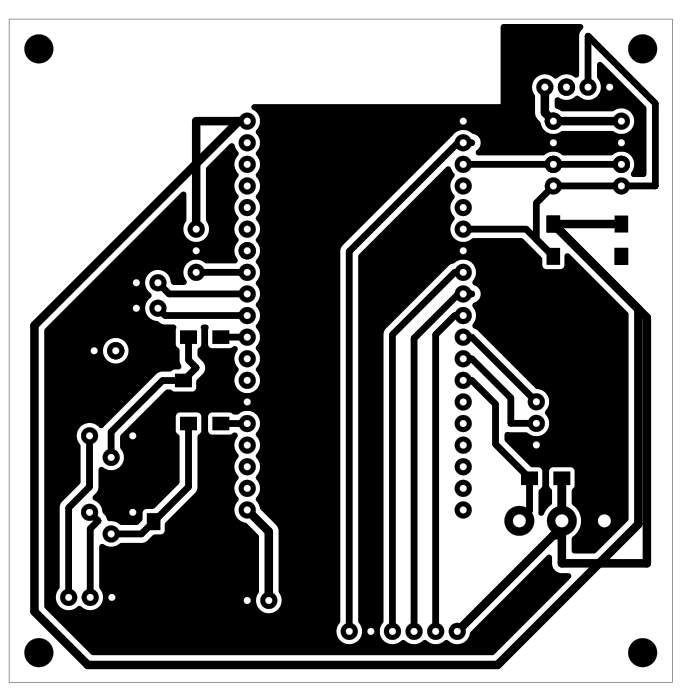
hardware/batman/reports/previews/A-copper-top-view.png
