sql-monk/batman/hardware/batman/reports/previews/B-copper-mirrored.png

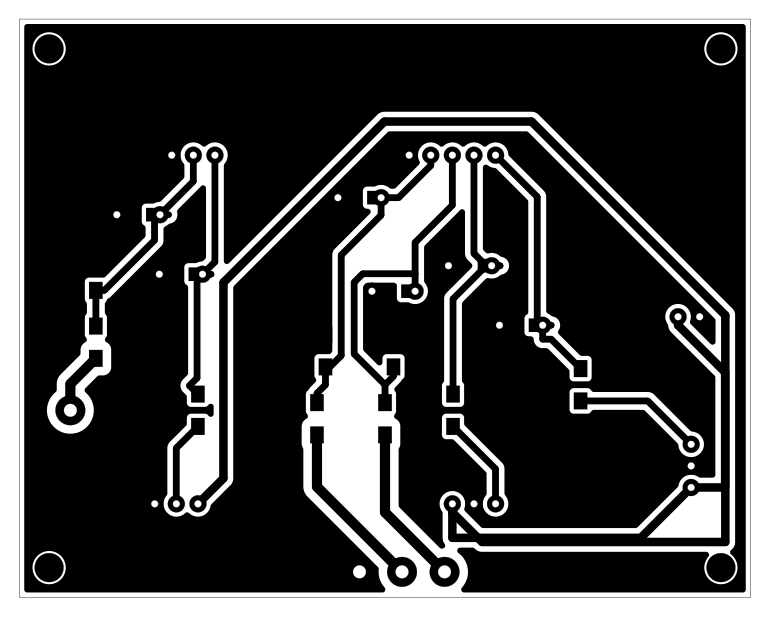
hardware/batman/reports/previews/B-copper-mirrored.png
