sql-monk/batman/hardware/batman/reports/previews/B-copper-top-view.png

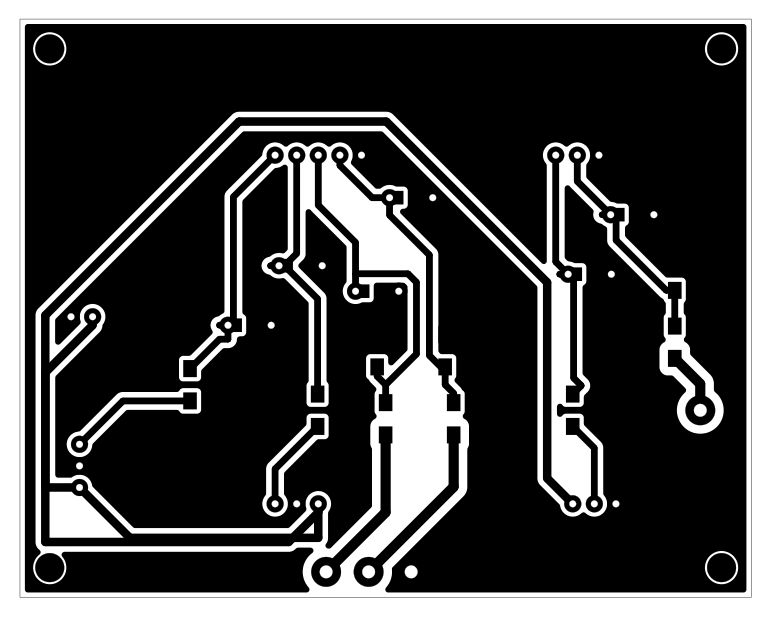
hardware/batman/reports/previews/B-copper-top-view.png
