sql-monk/batman/hardware/batman/reports/previews/C-copper-mirrored.png

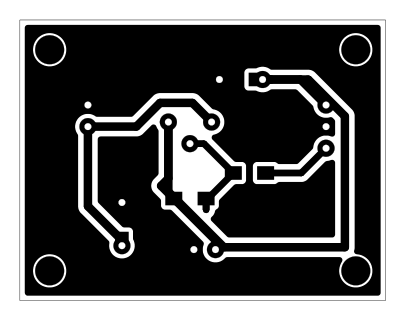
hardware/batman/reports/previews/C-copper-mirrored.png
