sql-monk/batman/hardware/batman/reports/previews/C-copper-top-view.png

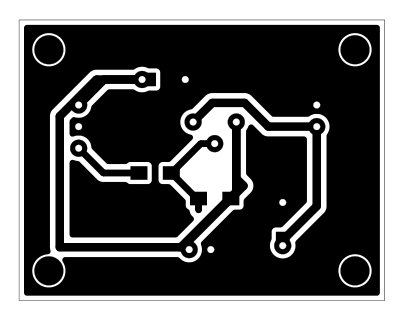
hardware/batman/reports/previews/C-copper-top-view.png
