sql-monk/batman/hardware/batman/reports/previews/copper-mirrored.png

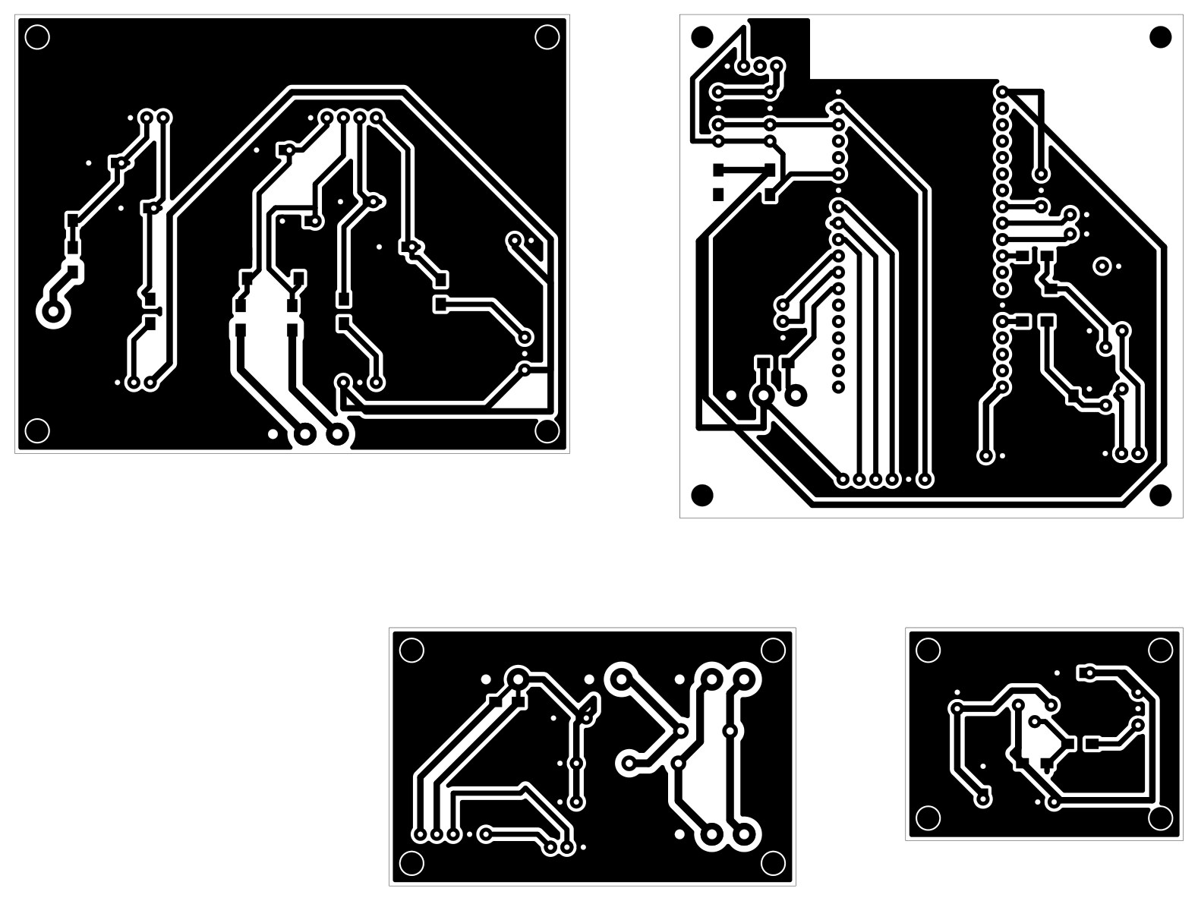
hardware/batman/reports/previews/copper-mirrored.png
