sql-monk/batman/hardware/batman/reports/previews/copper-top-view.png

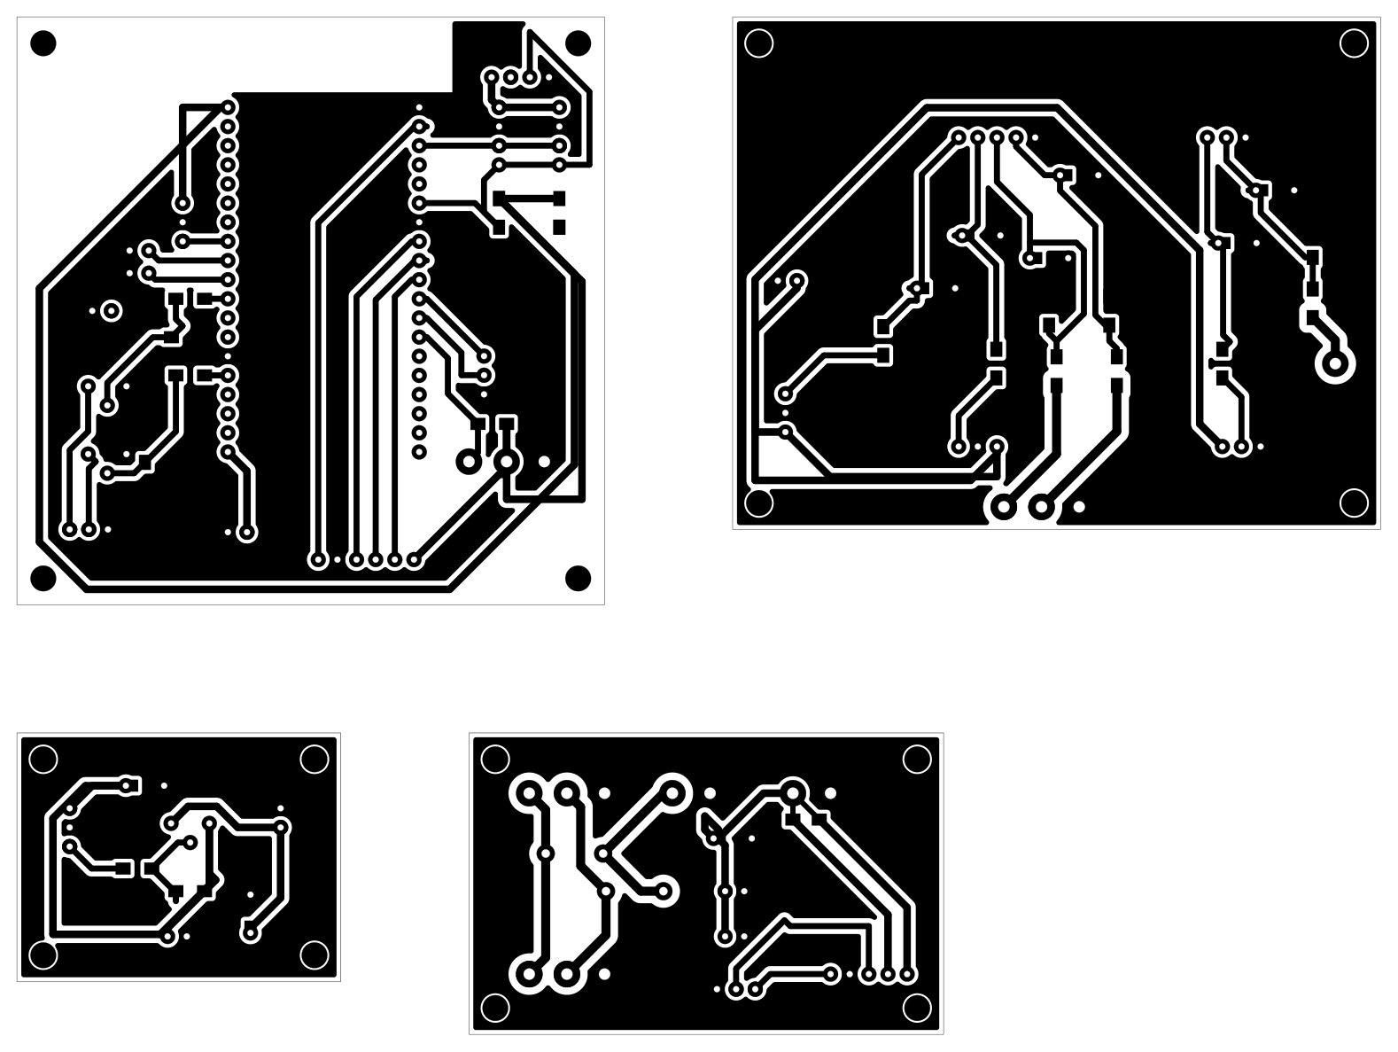
hardware/batman/reports/previews/copper-top-view.png
