sql-monk/batman/hardware/batman/reports/previews/D-copper-mirrored.png

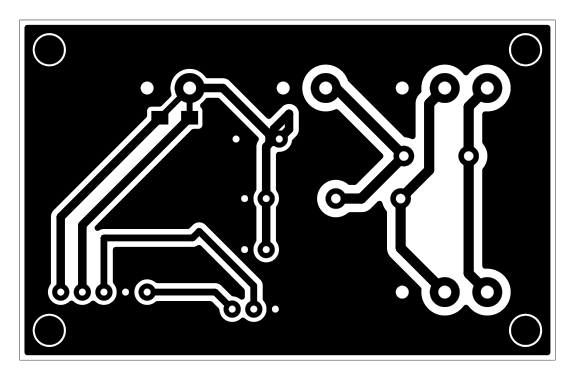
hardware/batman/reports/previews/D-copper-mirrored.png
