sql-monk/batman/hardware/batman/reports/previews/D-copper-top-view.png

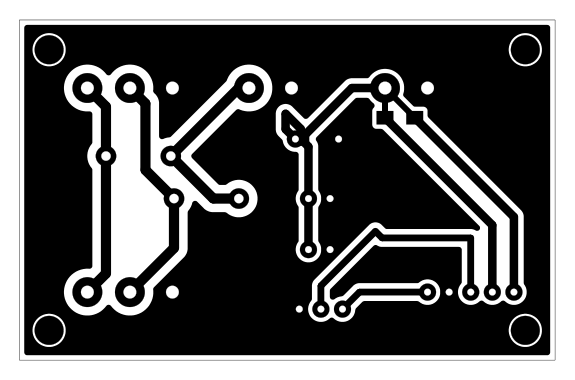
hardware/batman/reports/previews/D-copper-top-view.png
