sql-monk/batman/hardware/batman/reports/refinement/before-publish-20260909-170518/reports/previews/B-copper-mirrored.png

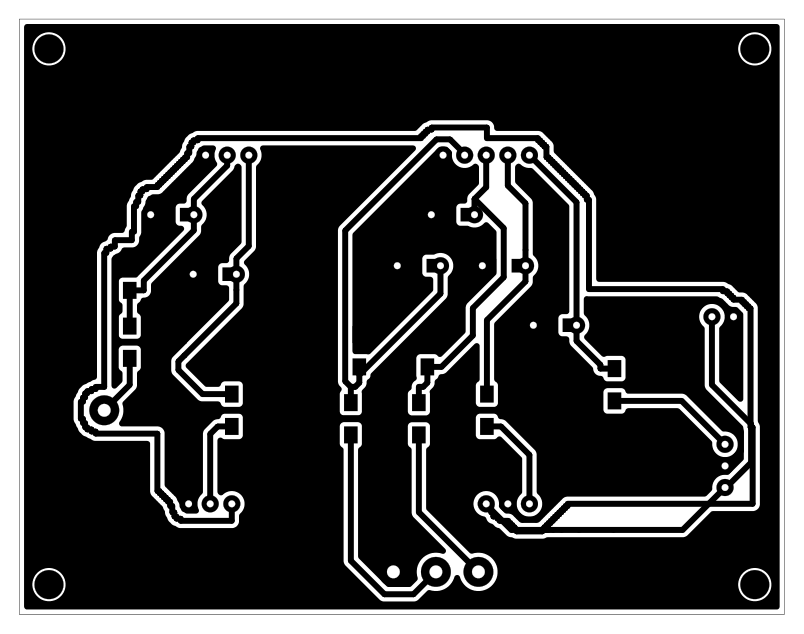
hardware/batman/reports/refinement/before-publish-20260909-170518/reports/previews/B-copper-mirrored.png
