sql-monk/batman/hardware/batman/reports/refinement/before-publish-20260909-170518/reports/previews/D-copper-top-view.png

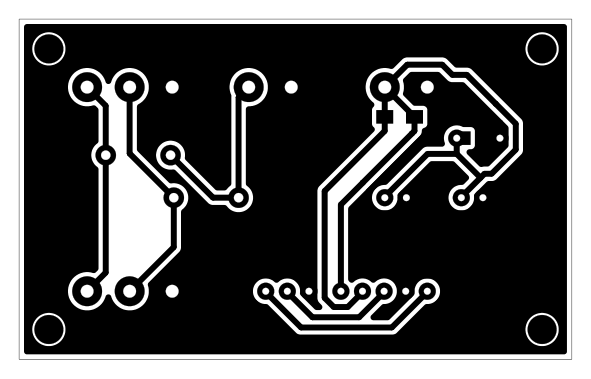
hardware/batman/reports/refinement/before-publish-20260909-170518/reports/previews/D-copper-top-view.png
