sql-monk/batman/hardware/batman/reports/routing45/A/candidate.png

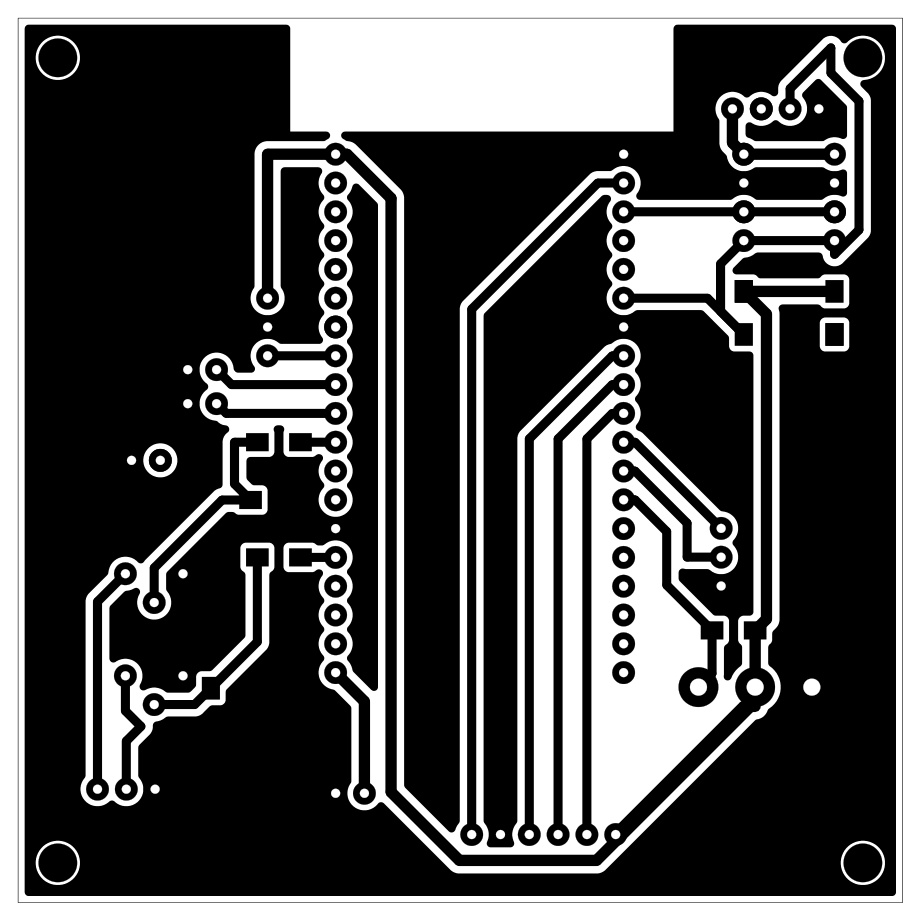
hardware/batman/reports/routing45/A/candidate.png
