sql-monk/batman/mechanical/cad/cable-logic.png

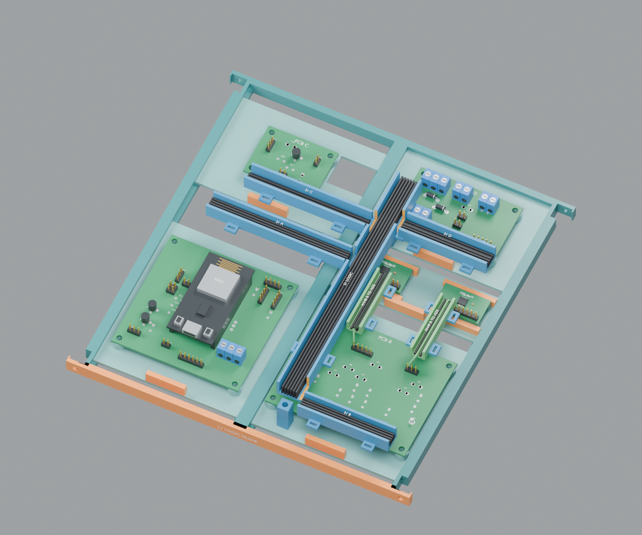
mechanical/cad/cable-logic.png
