sql-monk/batman/mechanical/cad/cable-modular-alternatives.png

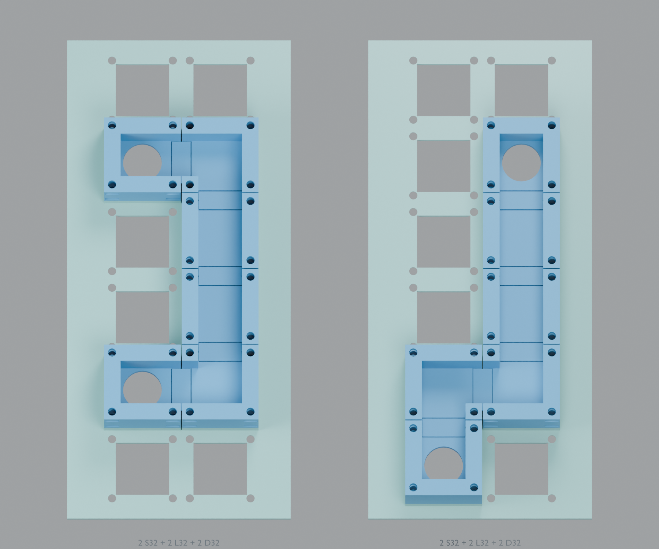
mechanical/cad/cable-modular-alternatives.png
