sql-monk/batman/mechanical/cad/cable-modular-levels.png

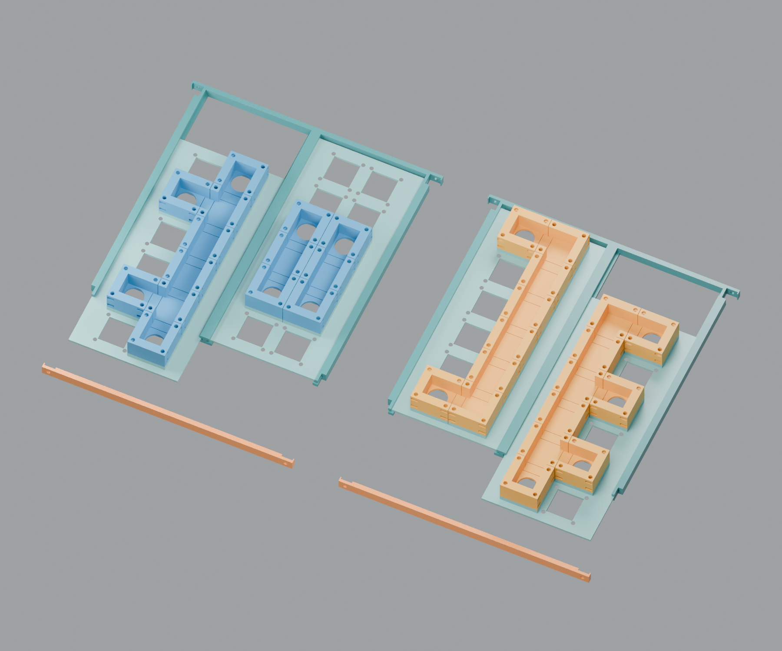
mechanical/cad/cable-modular-levels.png
