sql-monk/batman/mechanical/cad/cable-open.png

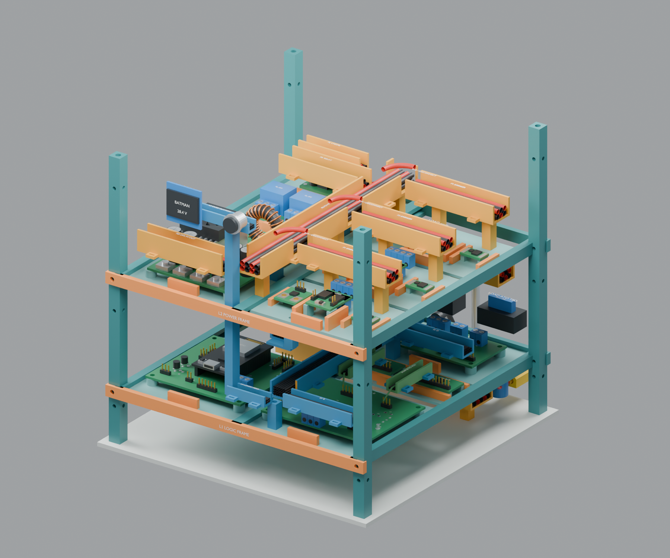
mechanical/cad/cable-open.png
