sql-monk/batman/mechanical/cad/cable-supported-power.png

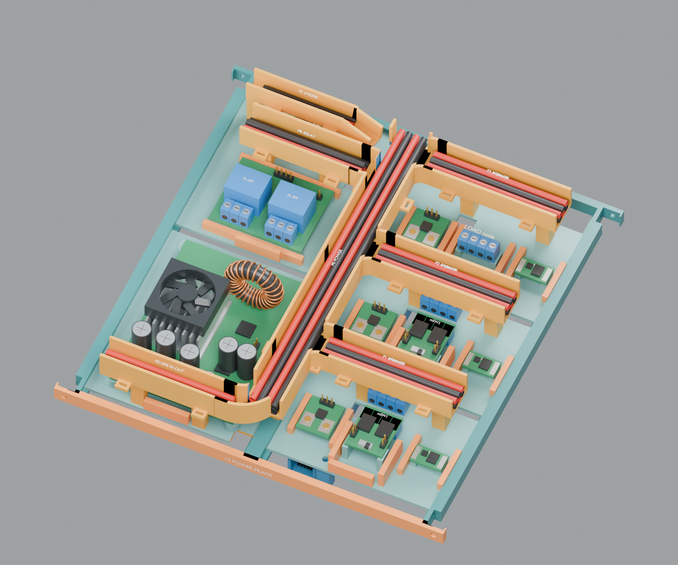
mechanical/cad/cable-supported-power.png
