sql-monk/batman/mechanical/cad/cable-supported.png

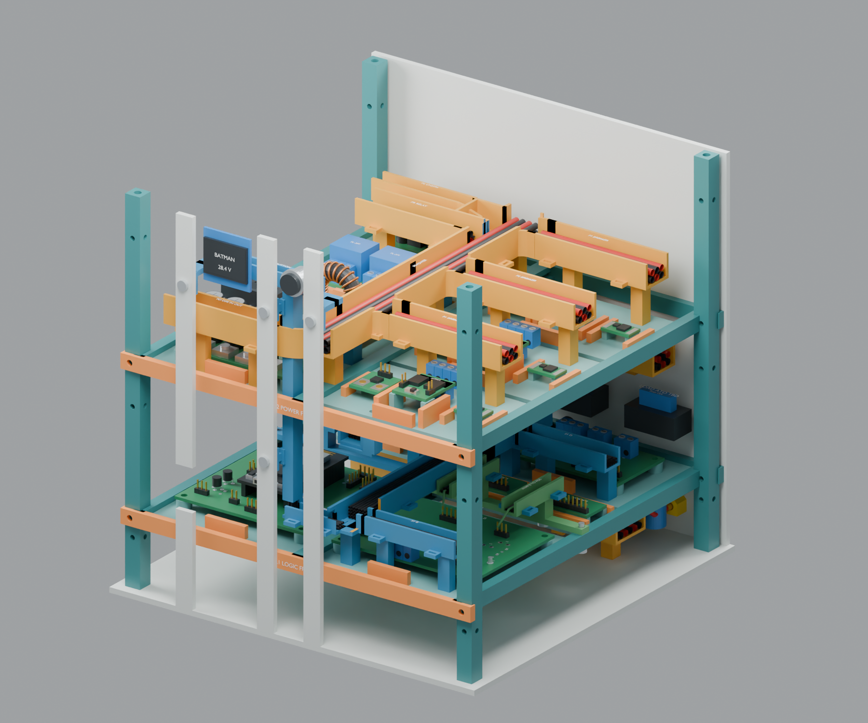
mechanical/cad/cable-supported.png
