sql-monk/batman/mechanical/cad/detailed-levels.png

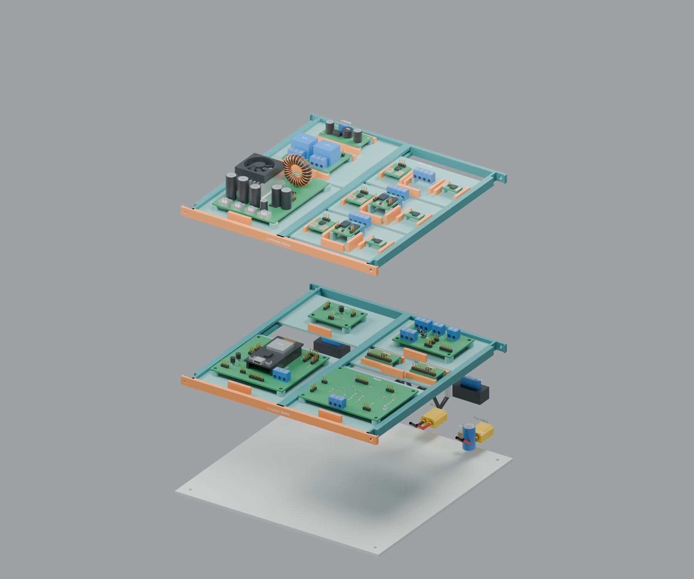
mechanical/cad/detailed-levels.png
