sql-monk/batman/mechanical/cad/detailed-xt60-rear.png

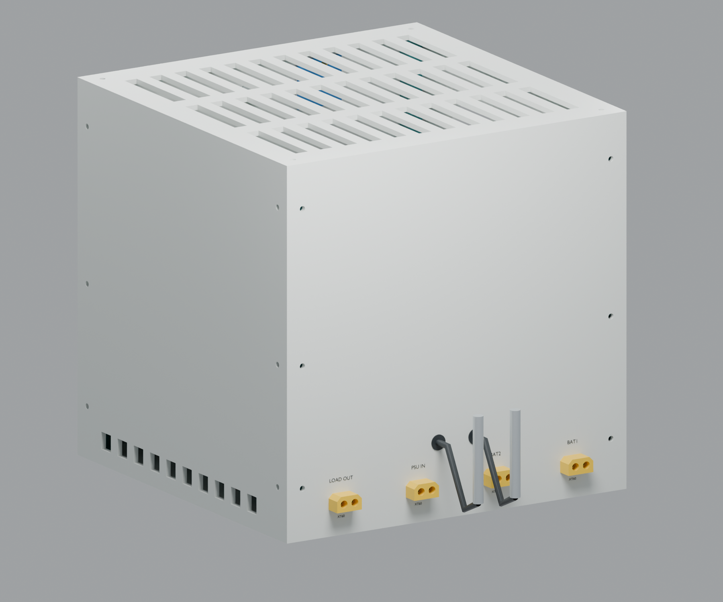
mechanical/cad/detailed-xt60-rear.png
