sql-monk/batman/mechanical/cad/levels-preview.png

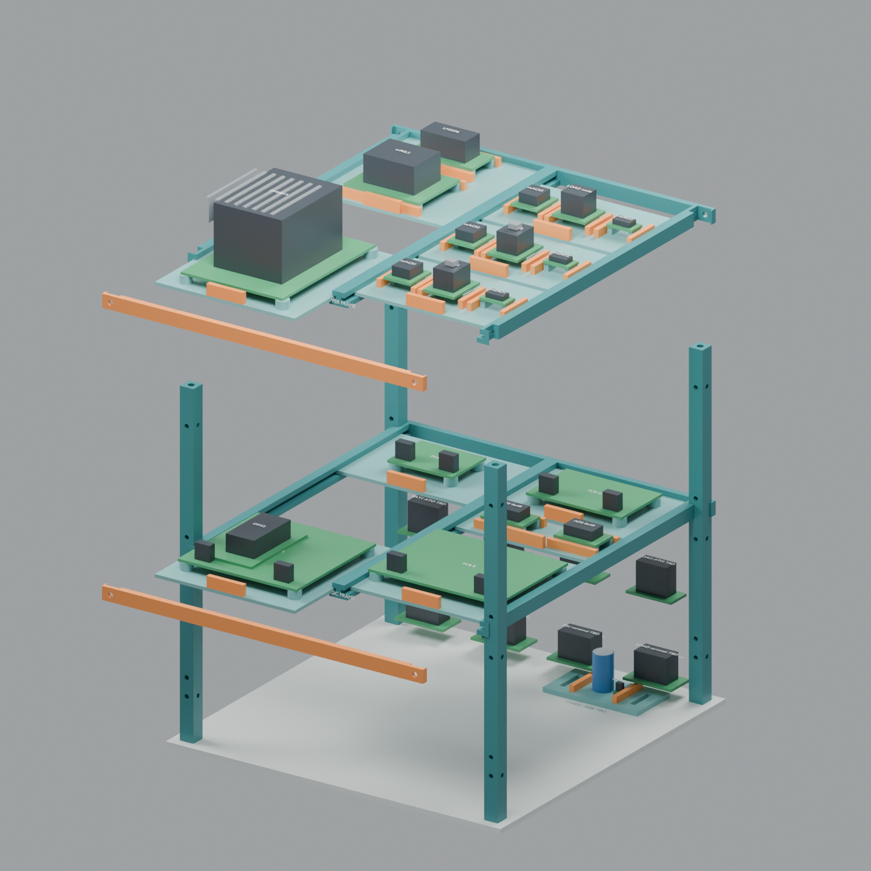
mechanical/cad/levels-preview.png
