sql-monk/batman/mechanical/cad/preview-enclosure-overall.png

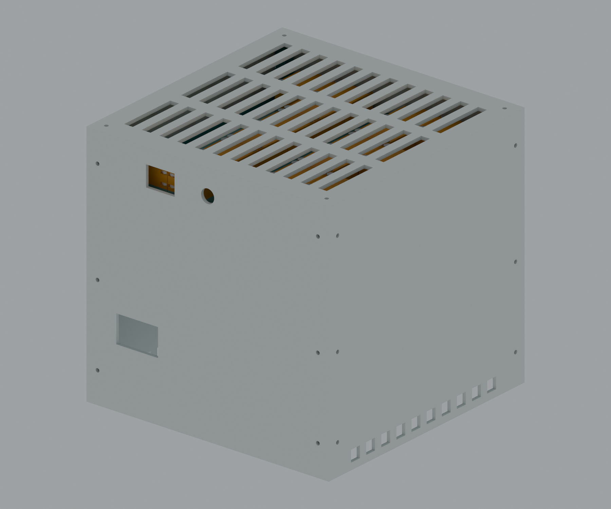
mechanical/cad/preview-enclosure-overall.png
