sql-monk/batman/mechanical/cad/preview-L0.png

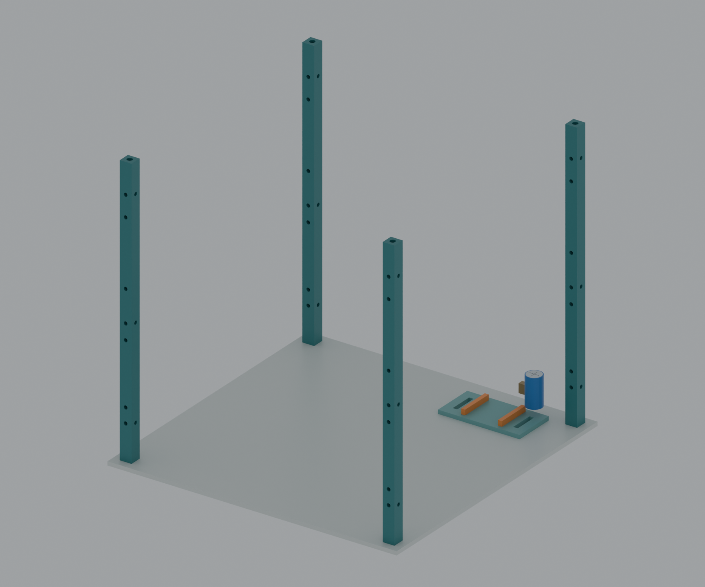
mechanical/cad/preview-L0.png
