sql-monk/batman/mechanical/cad/preview-L1.png

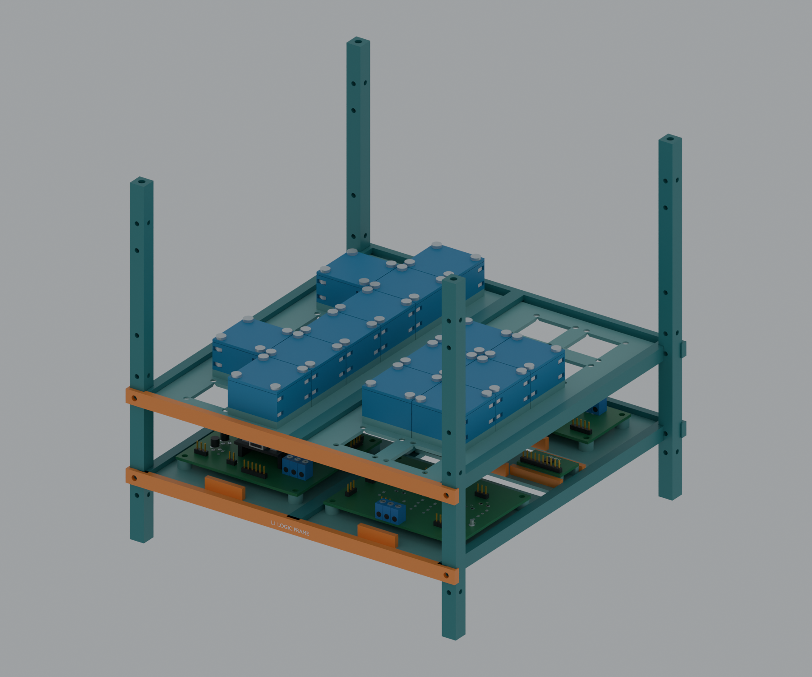
mechanical/cad/preview-L1.png
