sql-monk/batman/mechanical/cad/preview-L2.png

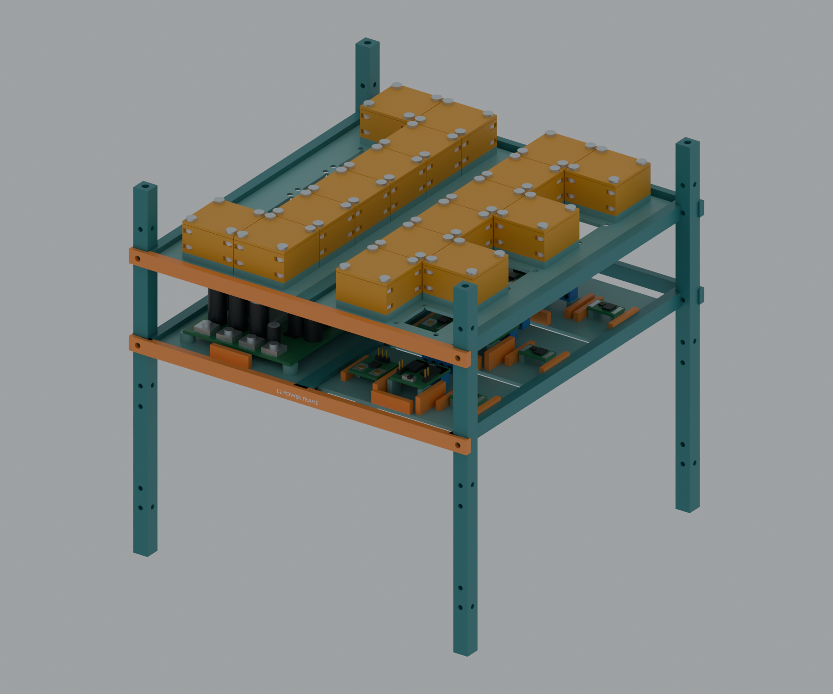
mechanical/cad/preview-L2.png
