sql-monk/batman/mechanical/references/dps5015.png

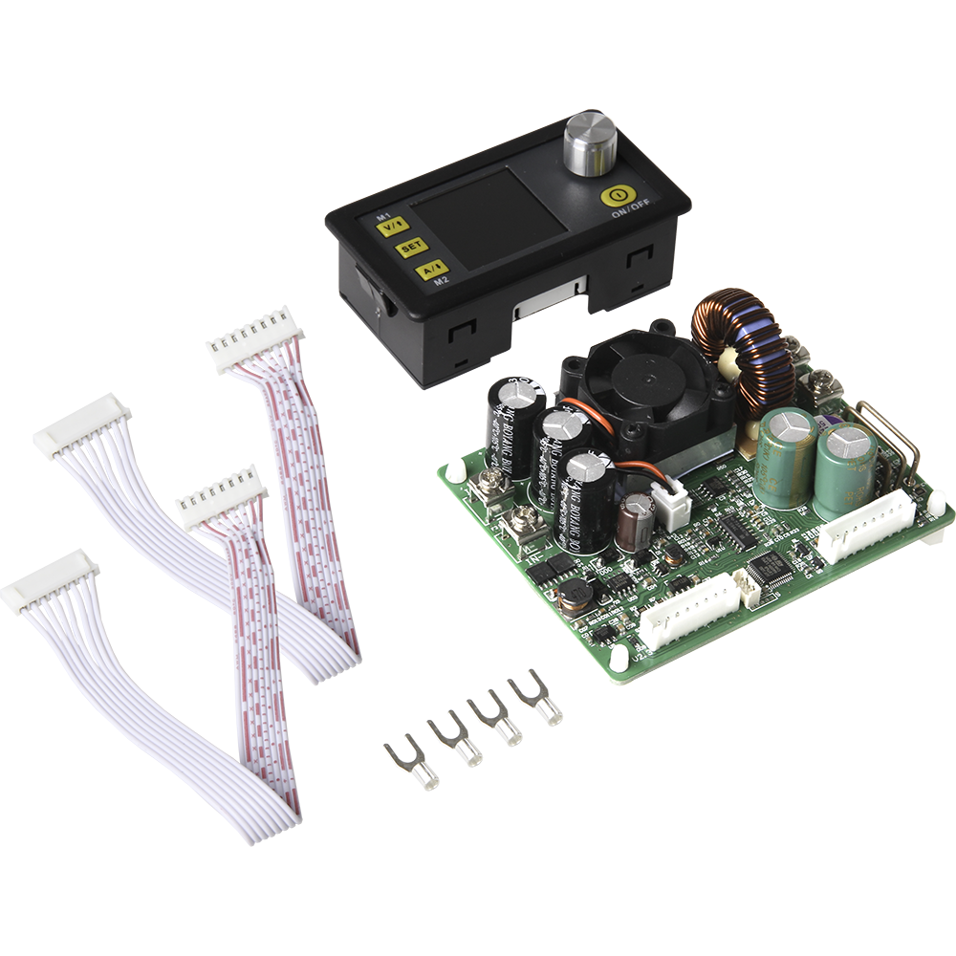
mechanical/references/dps5015.png
