sql-monk/batman/mechanical/references/pololu-switch.jpg

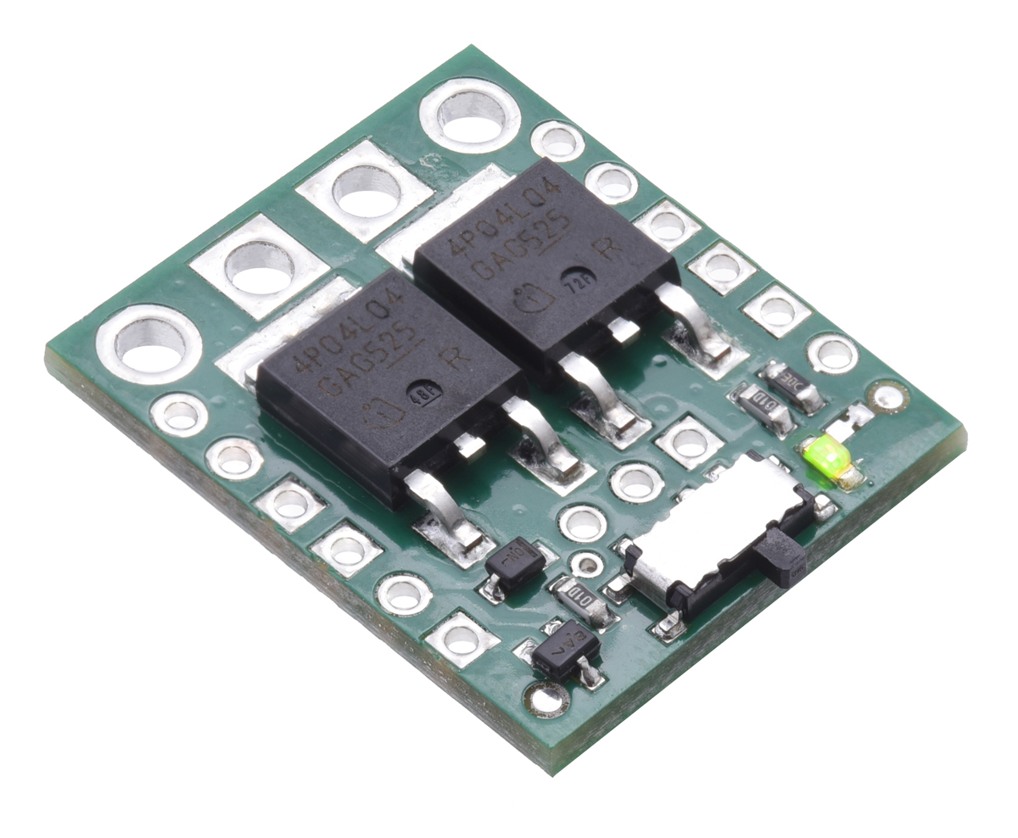
mechanical/references/pololu-switch.jpg
