sql-monk/batman/hardware/batman/reports/clean-routing/before-publish-20260909-212552/reports/previews/component-labels.png

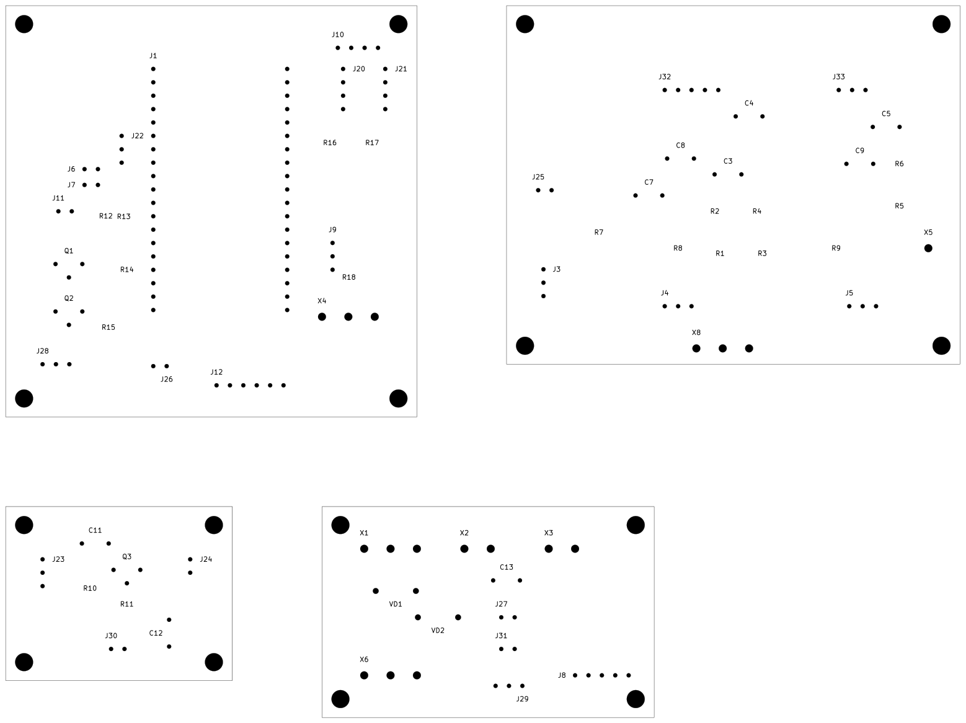
hardware/batman/reports/clean-routing/before-publish-20260909-212552/reports/previews/component-labels.png
