sql-monk/batman/hardware/batman/reports/gpio33/before-publish-20260909-184347/reports/previews/A-assembly.png

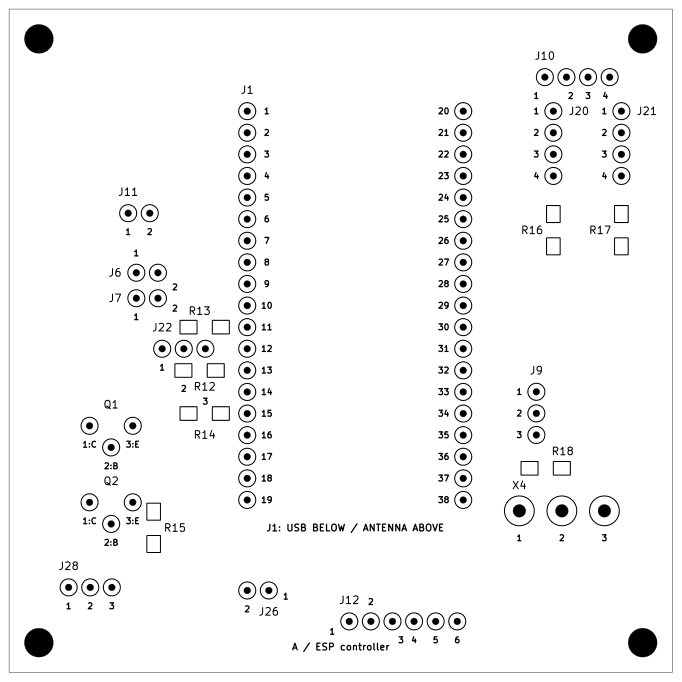
hardware/batman/reports/gpio33/before-publish-20260909-184347/reports/previews/A-assembly.png
