sql-monk/batman/mechanical/cad/assembled-preview.png

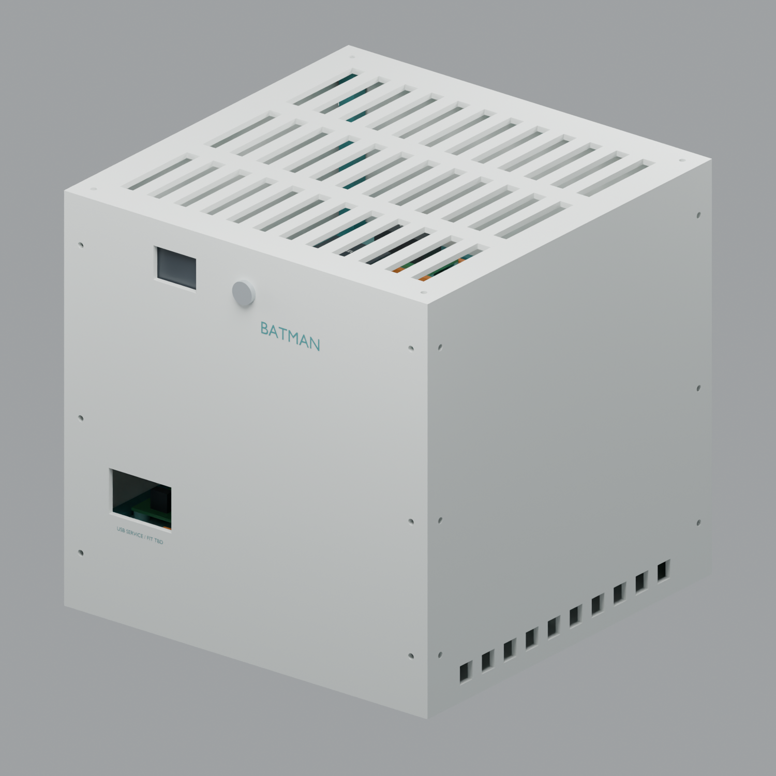
mechanical/cad/assembled-preview.png
