sql-monk/batman/hardware/batman/reports/refinement/B-verified/jumpers.csv

Ref | Net | A_X1_mm | A_Y1_mm | X2_mm | Y2_mm | Wire_cut_min_mm | End1 | End2
WB1 | U_B1 | 36.46 | 23.0 | 42.0 | 40.9 | 18.74 | existing pad | existing pad
