sql-monk/batman/hardware/batman/reports/gpio33/before-publish-20260909-184347/output/schematic.pdf

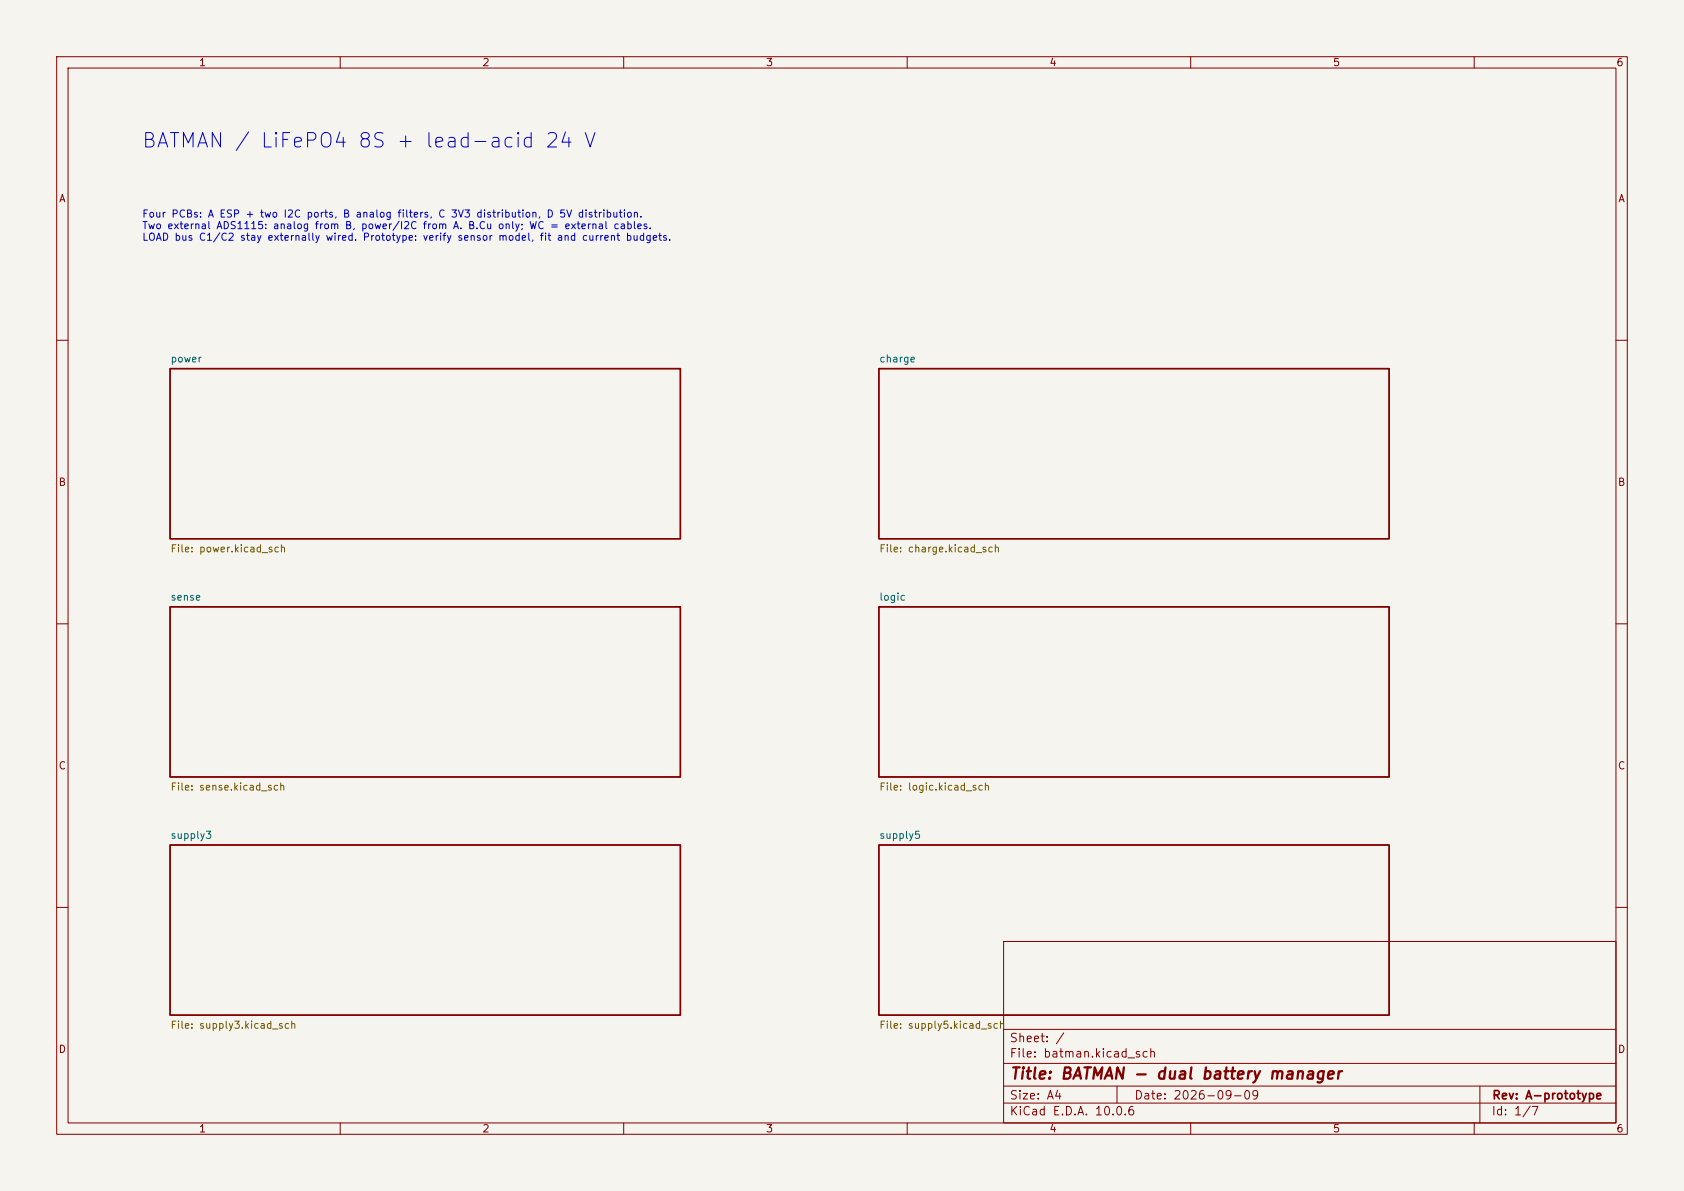
[picture p94: page 1]

Four PCBs: A ESP + two I2C ports, B analog filters, C 3V3 distribution, D 5V distribution. Two external ADS1115: analog from B, power/I2C from A. B.Cu only; WC = external cables. LOAD bus C1/C2 stay externally wired. Prototype: verify sensor model, fit and current budgets.

Sheet: /
File: batman.kicad_sch
Title: BATMAN - dual battery manager

Size: A4 | Rev: A-prototype
KiCad E.D.A. 10.0.6 | Id: 1/7


P01-P28: external power wiring 2.5 mm2; P28 logic ground 0.75 mm2. B1/B2 are AFTER sensors, BEFORE switches. IP- faces battery / source. LOAD+/GND: external terminals, C1/C2 wired directly, no buffer PCB. D3 DNP; not a 35 V clamp.


REMOVE relay VCC-JD_VCC jumper. Route VCC / JD_VCC separately from X3. DPS: GND TX RX -> G R T; leave V unconnected. Set mDC5 to 5.0 V BEFORE plugging J1. Never close K1 and K2 together. Switch relays only at verified zero current. Hardware rating: 10 A maximum.


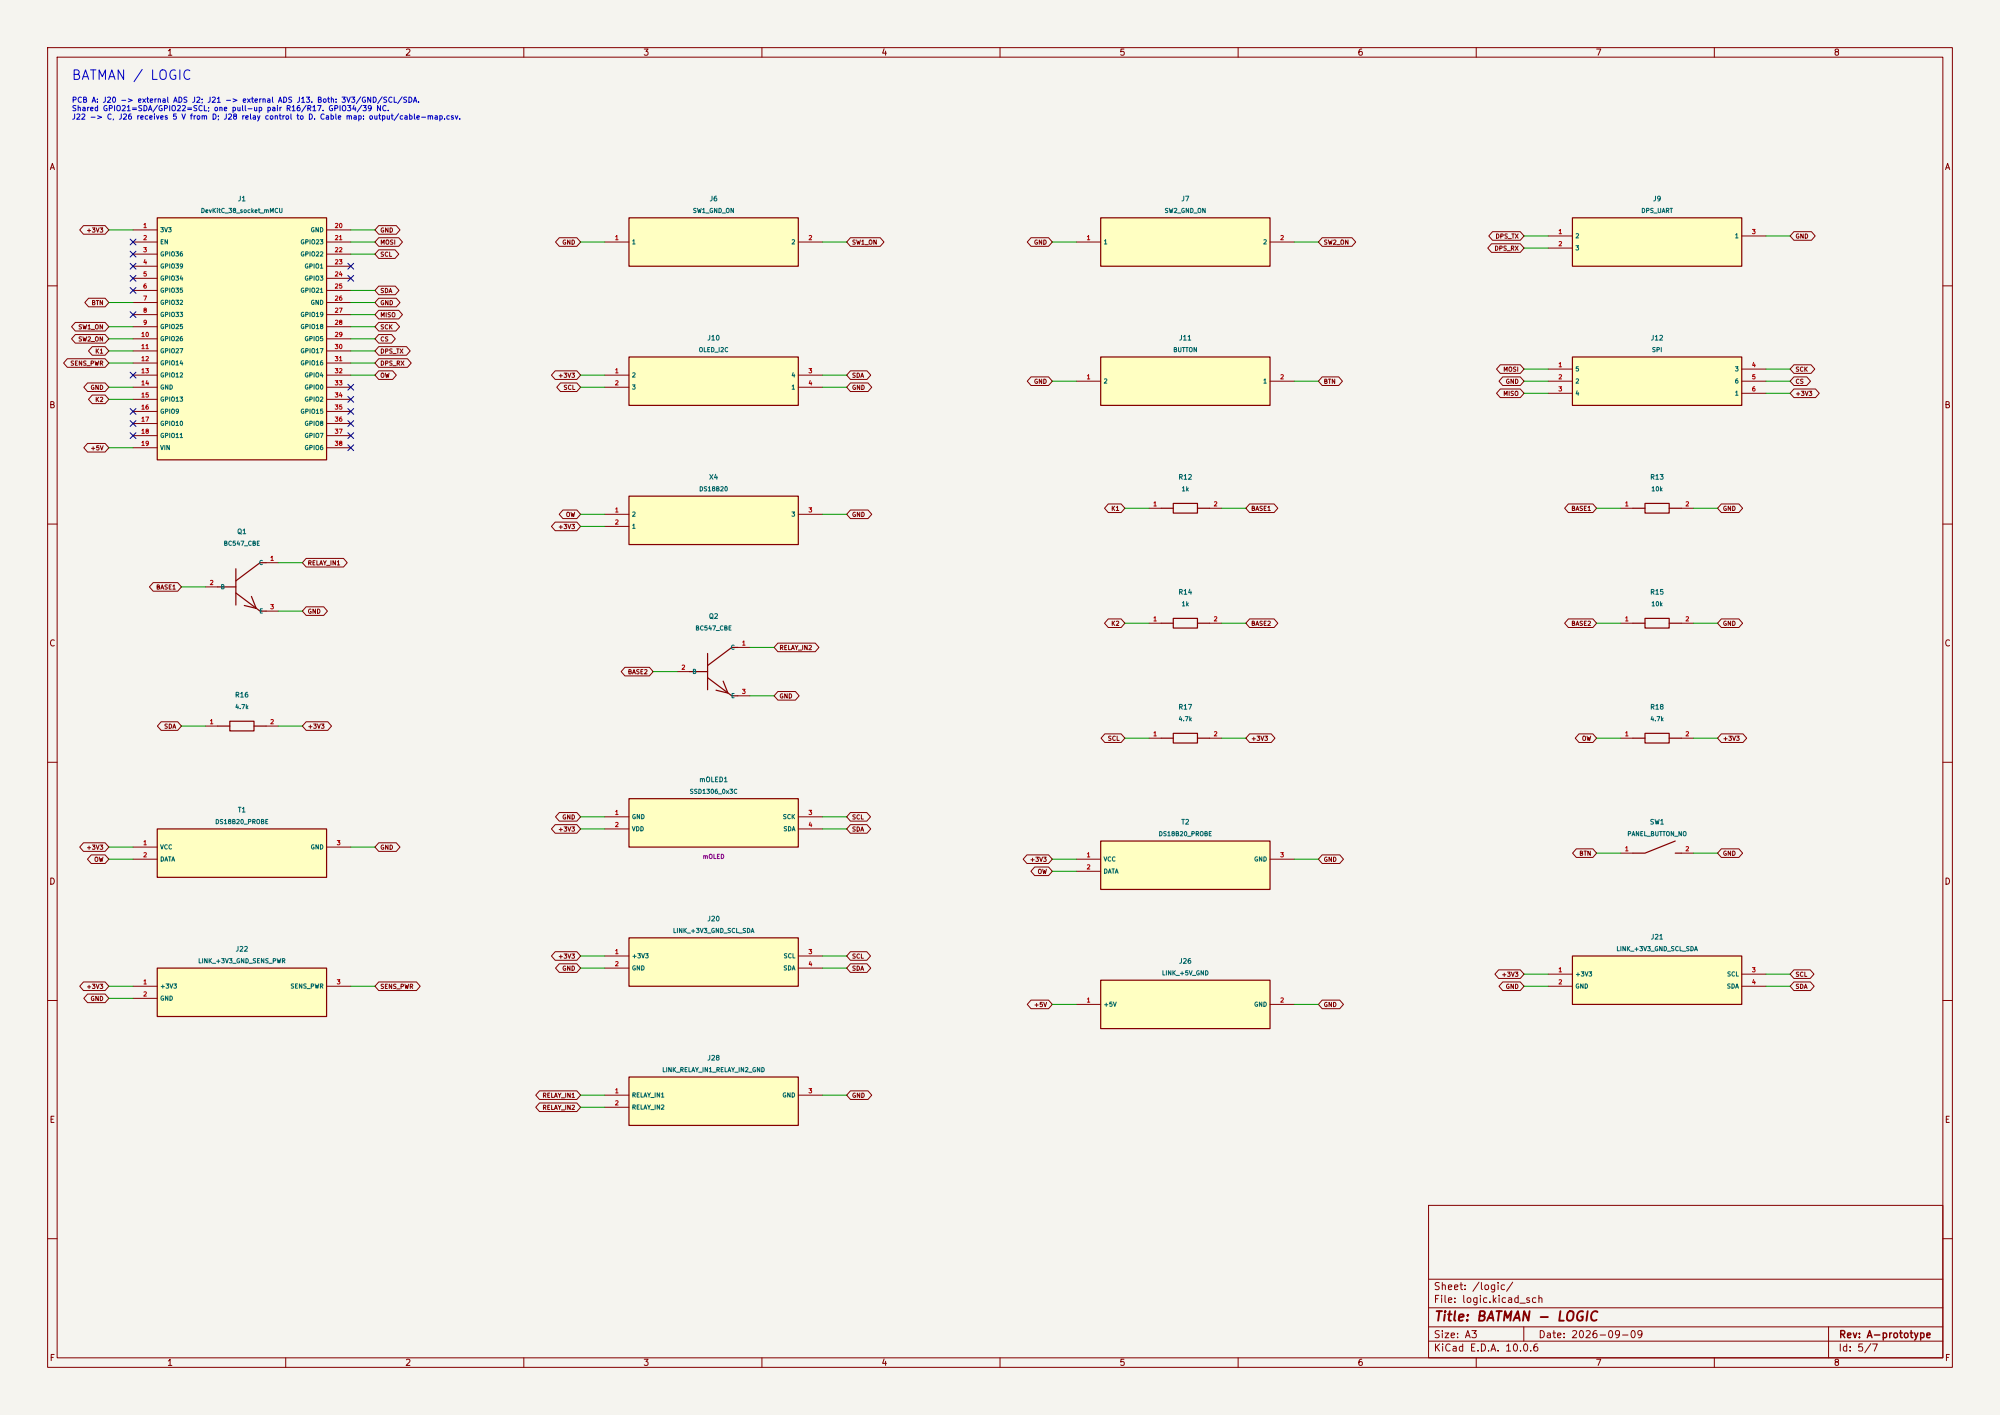
[picture p95: page 5]

PCB A: J20 -> external ADS J2; J21 -> external ADS J13. Both: 3V3/GND/SCL/SDA. Shared GPIO21=SDA/GPIO22=SCL; one pull-up pair R16/R17. GPIO34/39 NC. J22 -> C, J26 receives 5 V from D; J28 relay control to D. Cable map: output/cable-map.csv.



PCB D: DISTRIBUTION ONLY. X3 receives regulated 5.0 V from external LM2596. X1 battery taps feed diode OR -> X2 LM2596 input; X6 -> X8 on ADC PCB B (sense only). NT1 star: separate relay VCC/JD-VCC. REMOVE relay jumper. J27 -> ESP; J31 spare 5 V. BATMAN / SUPPLY5
