sql-monk/batman/hardware/batman/output/B/copper-mirrored.pdf

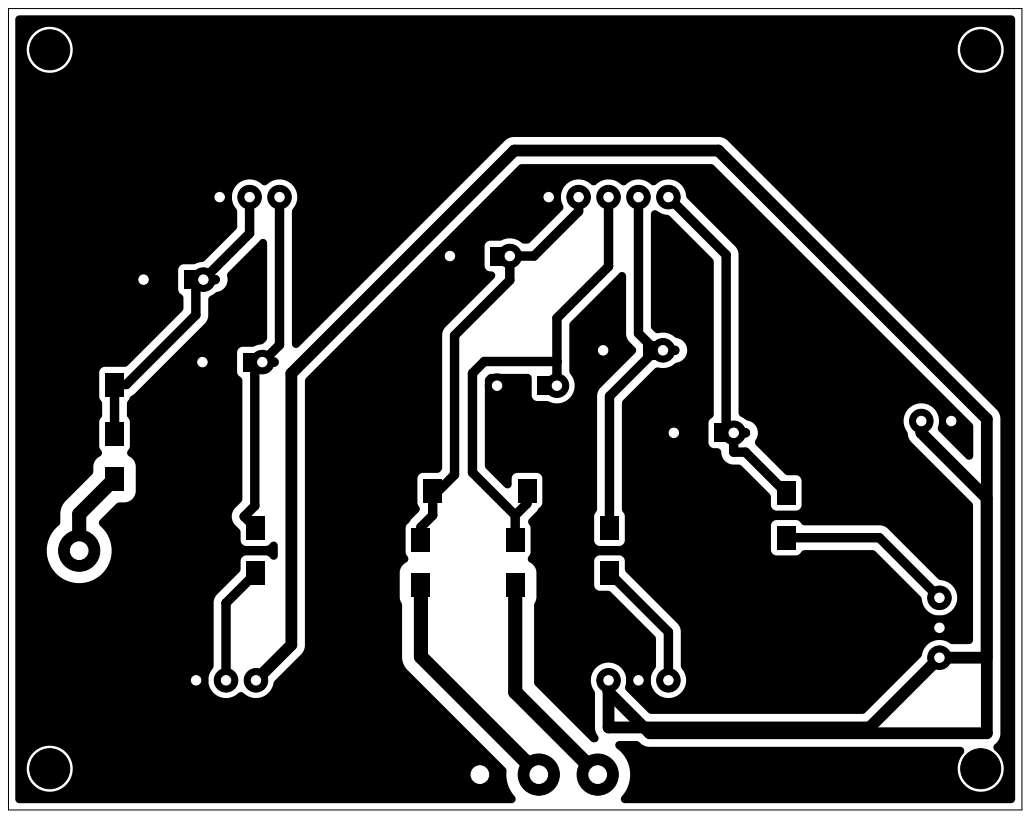
[picture p106: page 1]
