sql-monk/batman/hardware/batman/output/B/copper-top-view.pdf

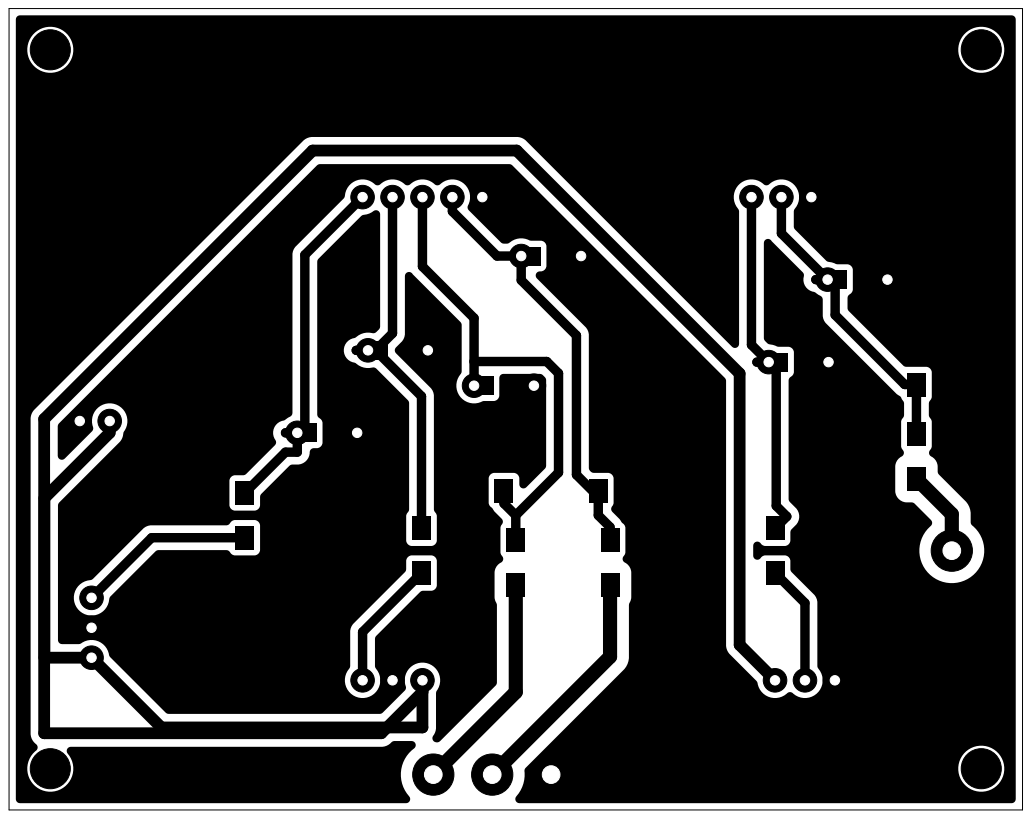
[picture p107: page 1]
