sql-monk/batman/hardware/batman/output/B/wiring.pdf

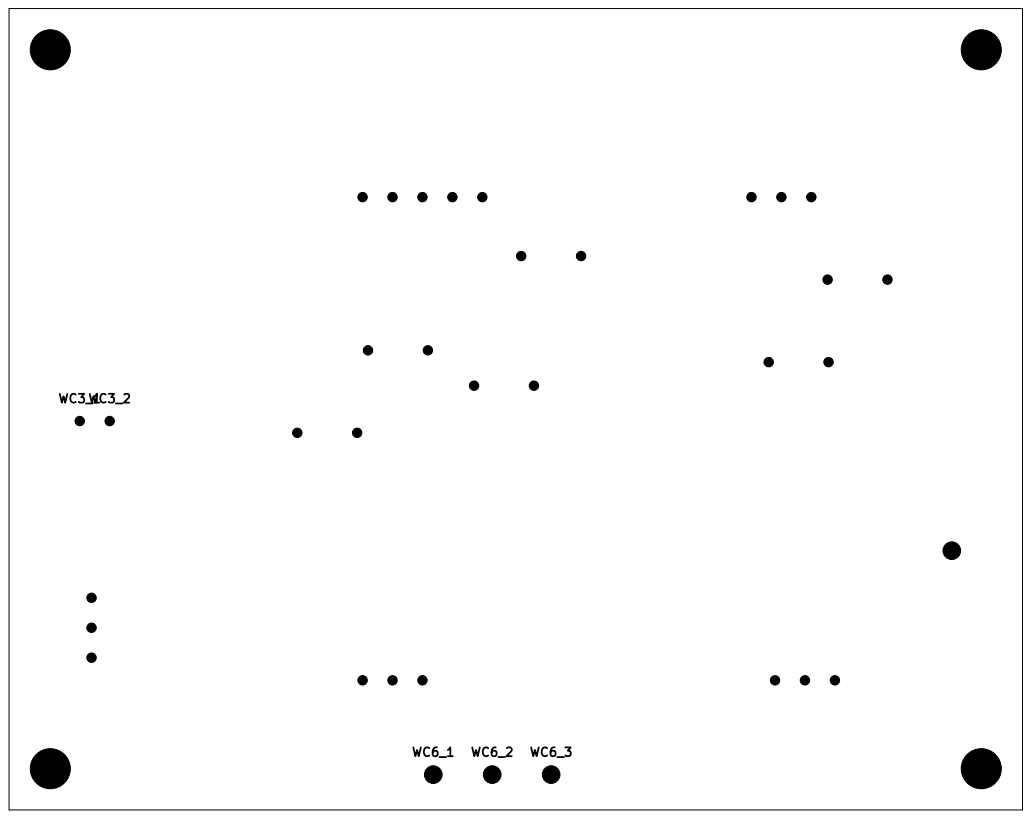
[picture p108: page 1]
