sql-monk/batman/hardware/batman/output/C/assembly.pdf

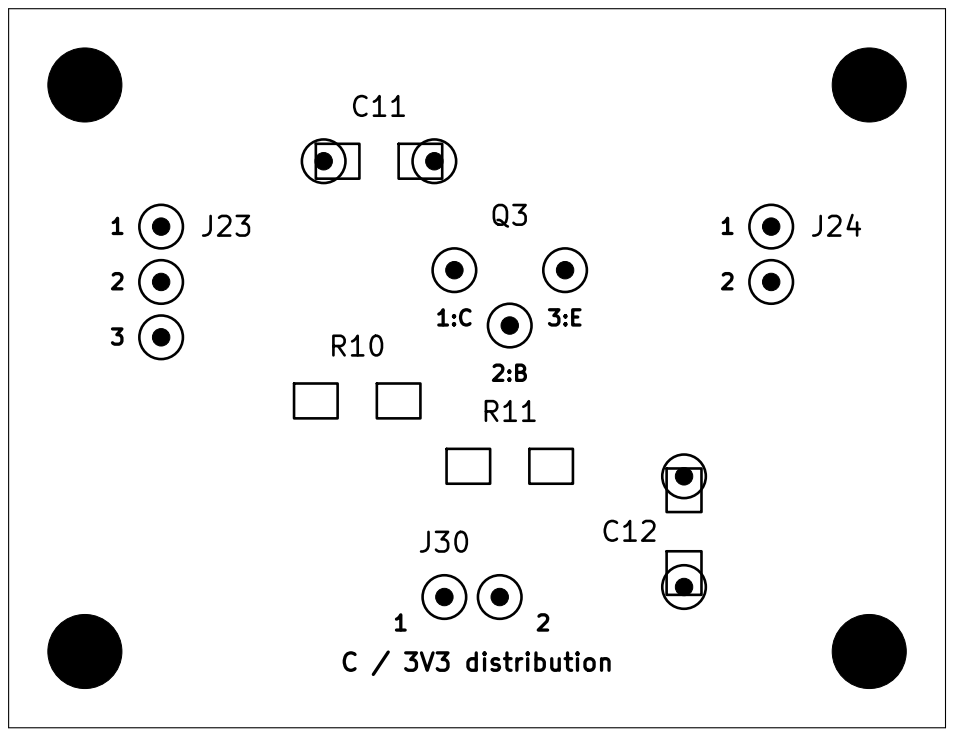
[picture p109: page 1]
