sql-monk/batman/hardware/batman/output/C/copper-mirrored.pdf

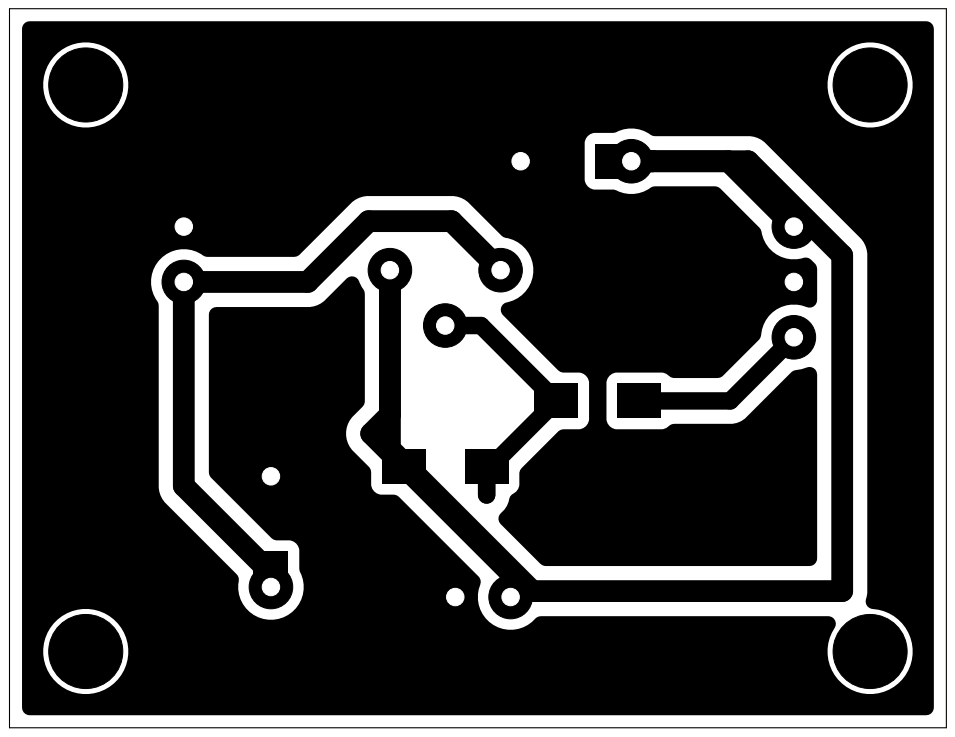
[picture p110: page 1]
