sql-monk/batman/hardware/batman/output/C/copper-top-view.pdf

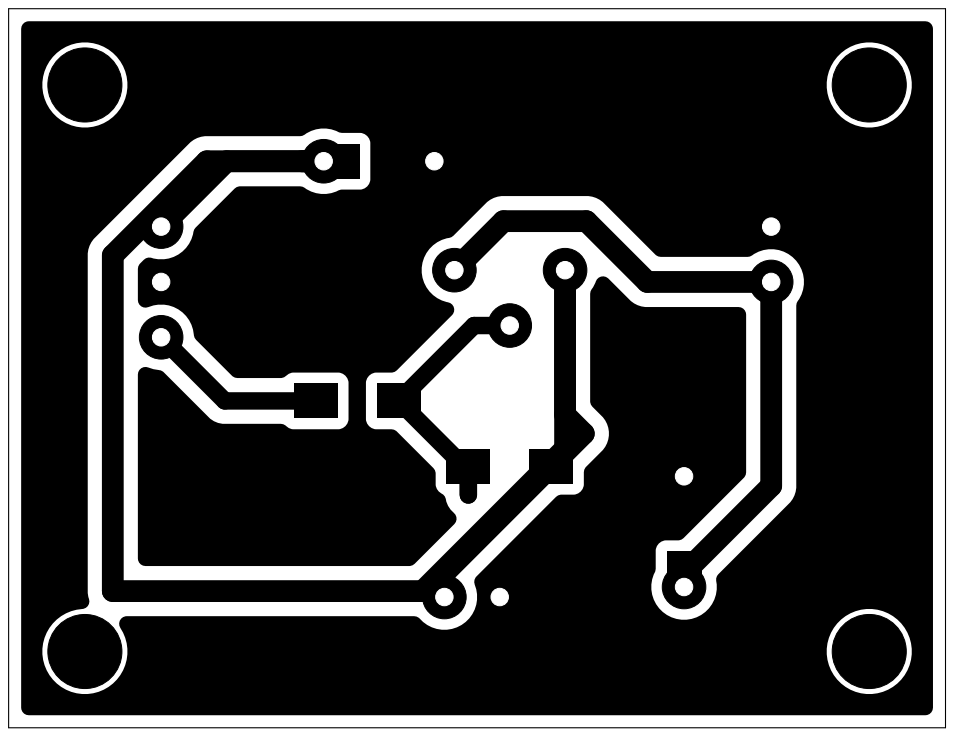
[picture p111: page 1]
