sql-monk/batman/hardware/batman/output/C/wiring.pdf

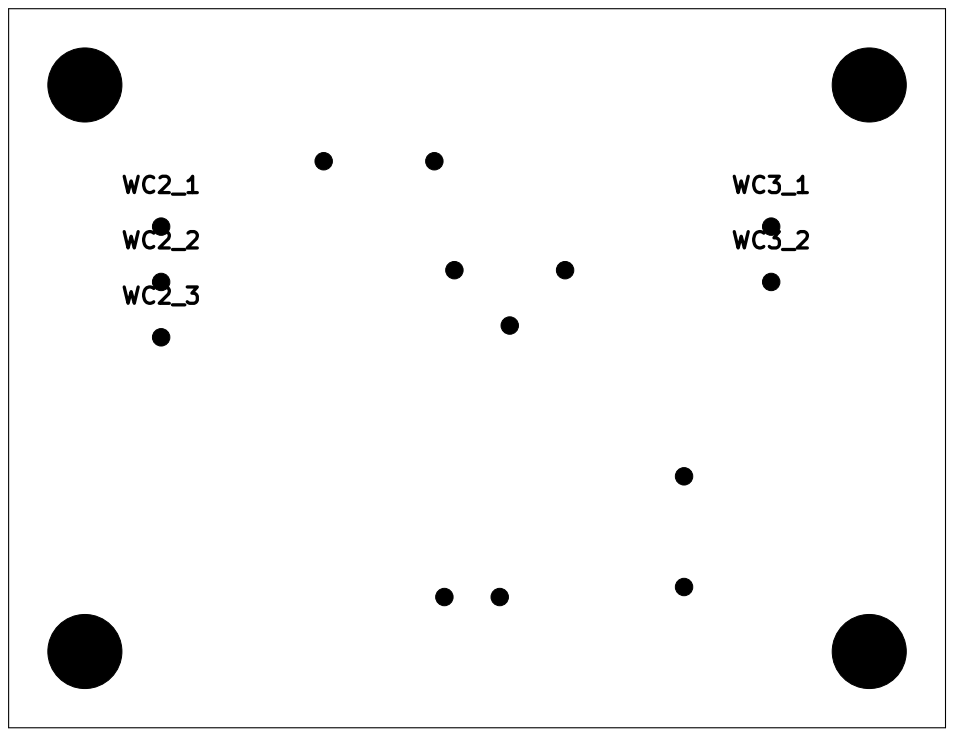
[picture p112: page 1]
