sql-monk/batman/hardware/batman/output/D/assembly.pdf

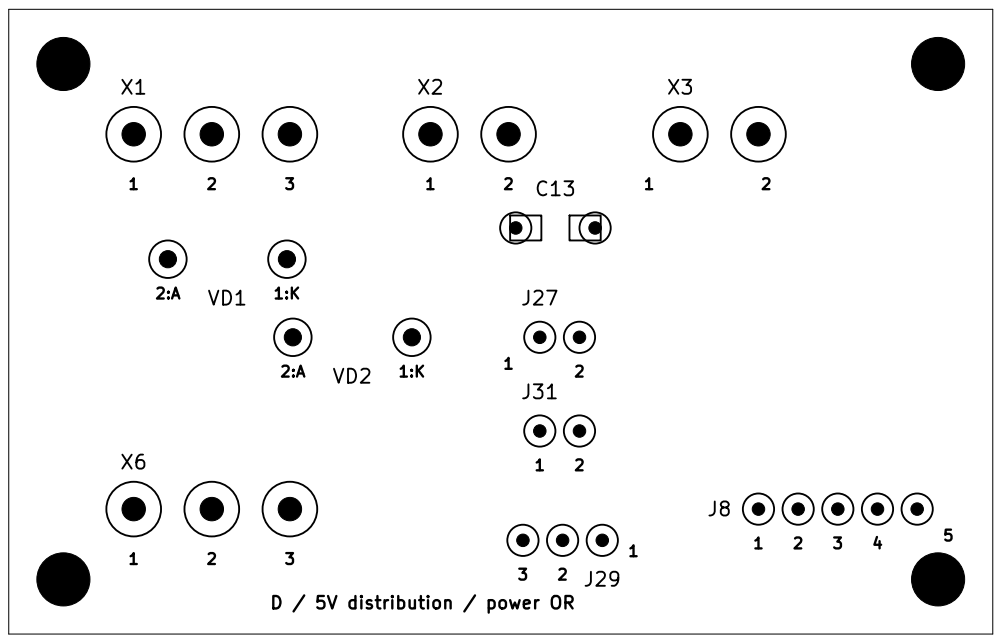
[picture p113: page 1]
