sql-monk/batman/hardware/batman/output/D/copper-mirrored.pdf

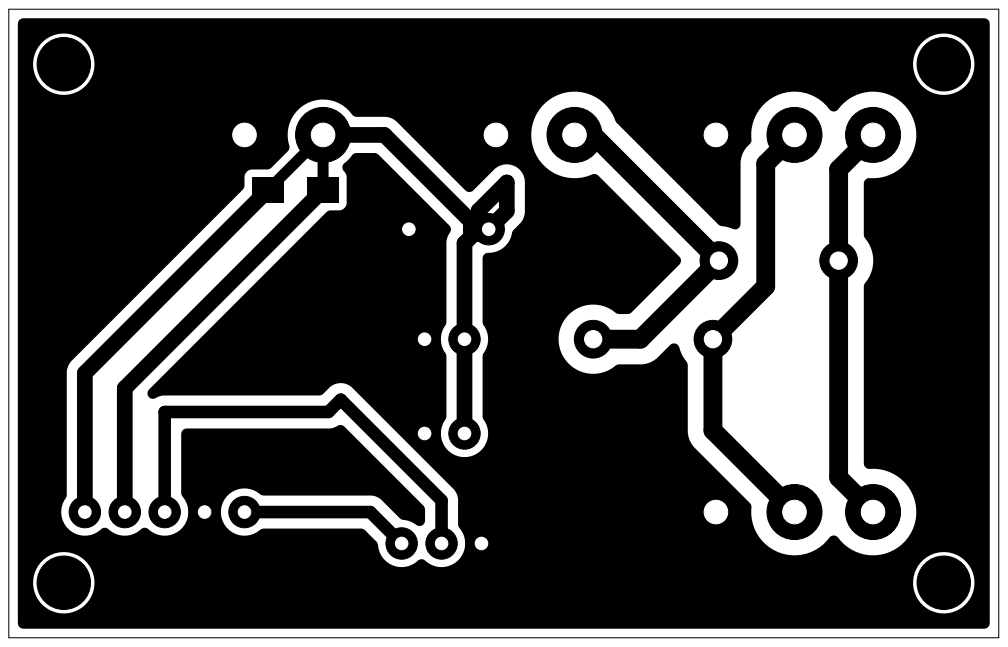
[picture p114: page 1]
