sql-monk/batman/hardware/batman/output/D/copper-top-view.pdf

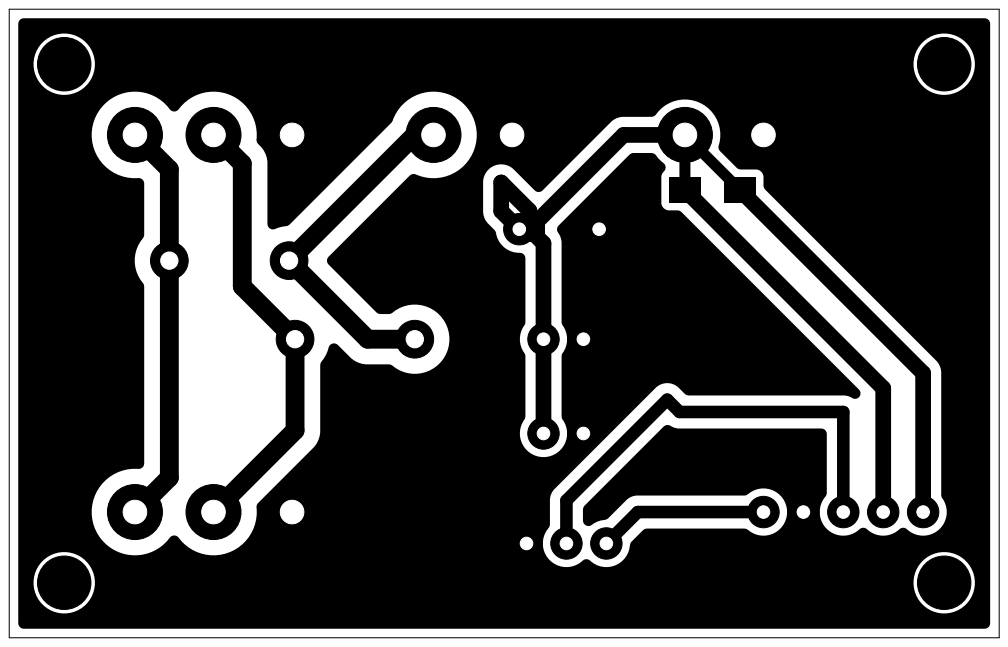
[picture p115: page 1]
