sql-monk/batman/hardware/batman/output/D/wiring.pdf

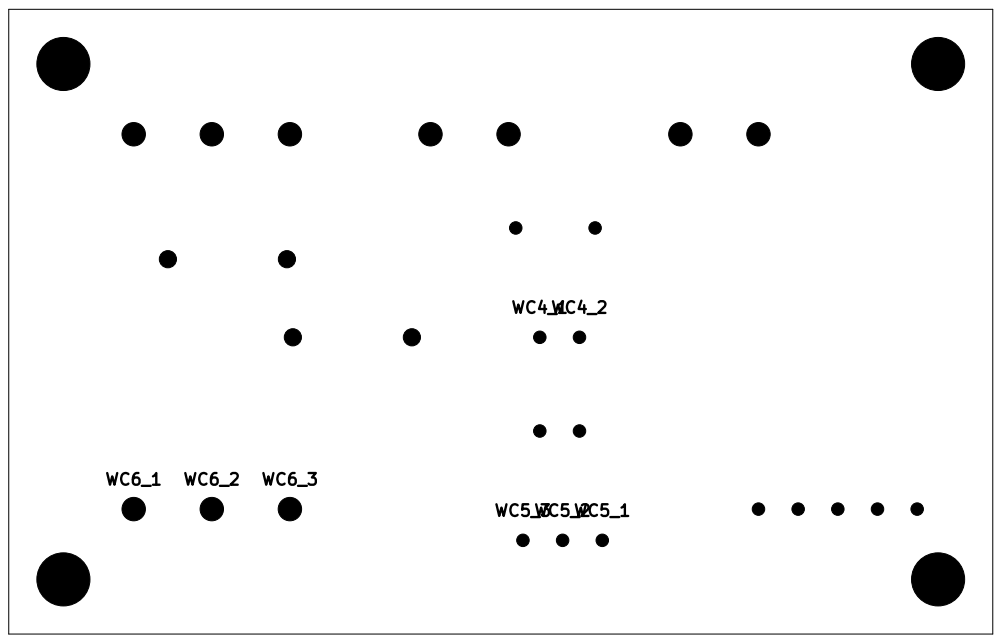
[picture p116: page 1]
