sql-monk/batman/hardware/batman/reports/routing45/A/candidate.pdf

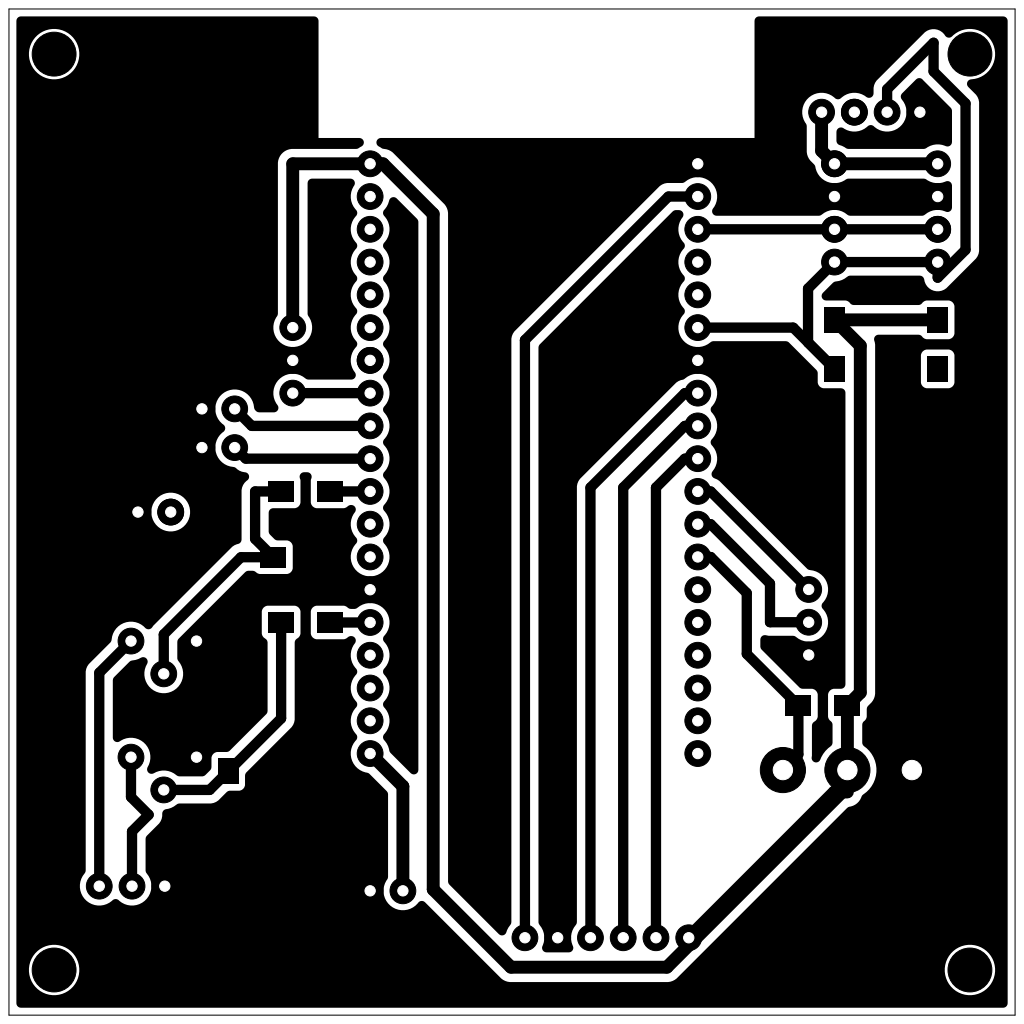
[picture p117: page 1]
