sql-monk/batman/hardware/batman/reports/routing45/B/candidate.pdf

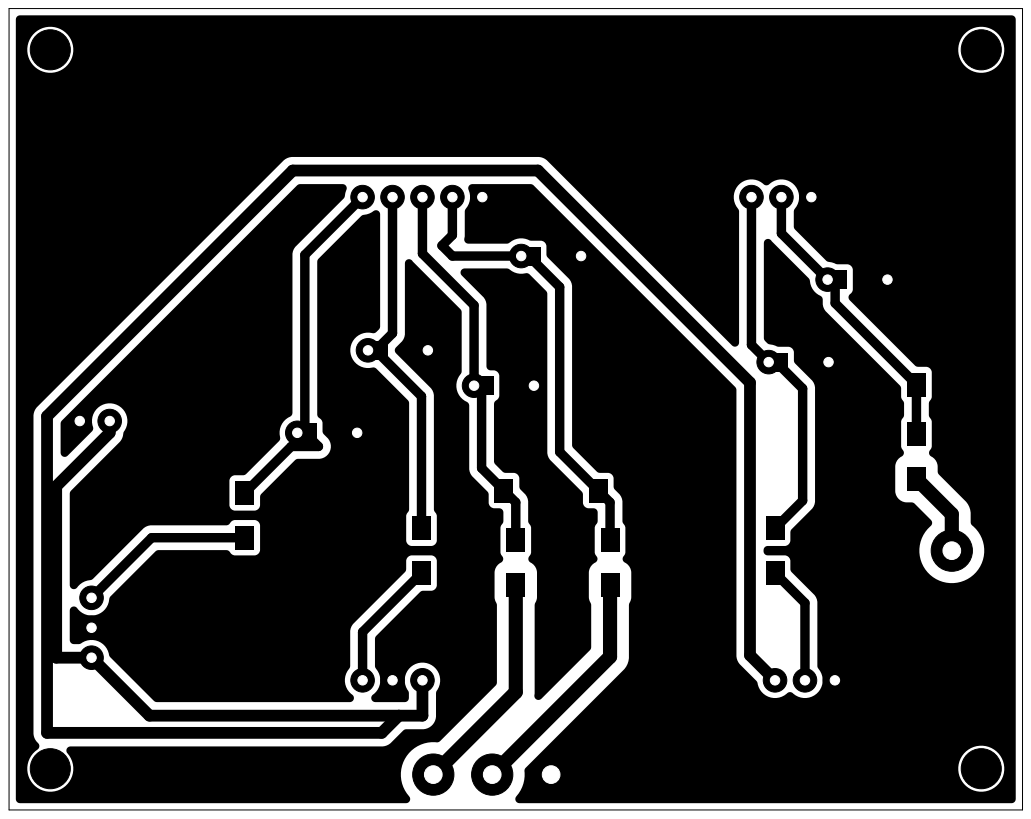
[picture p118: page 1]
