sql-monk/batman/hardware/batman/reports/clean-routing/before-publish-20260909-212552/output/copper-mirrored.pdf

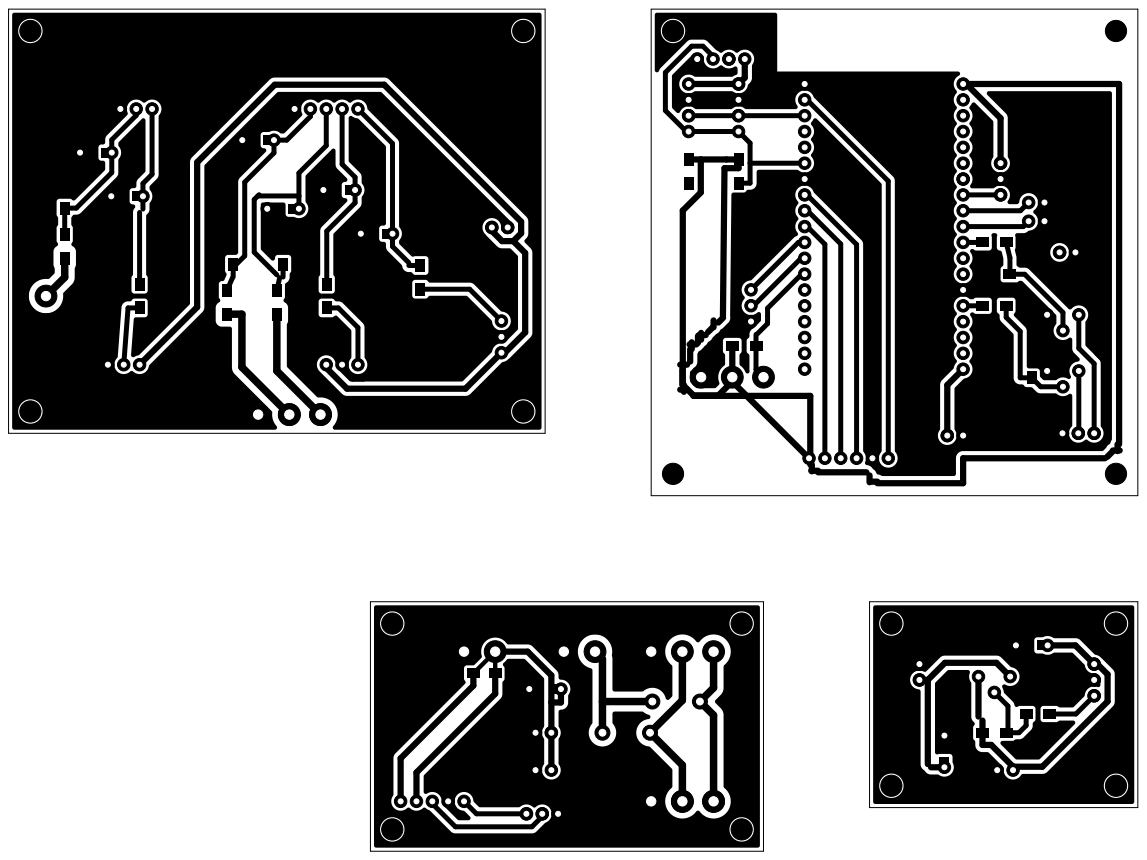
[picture p119: page 1]
