sql-monk/batman/hardware/batman/reports/clean-routing/before-publish-20260909-212552/output/copper-top-view.pdf

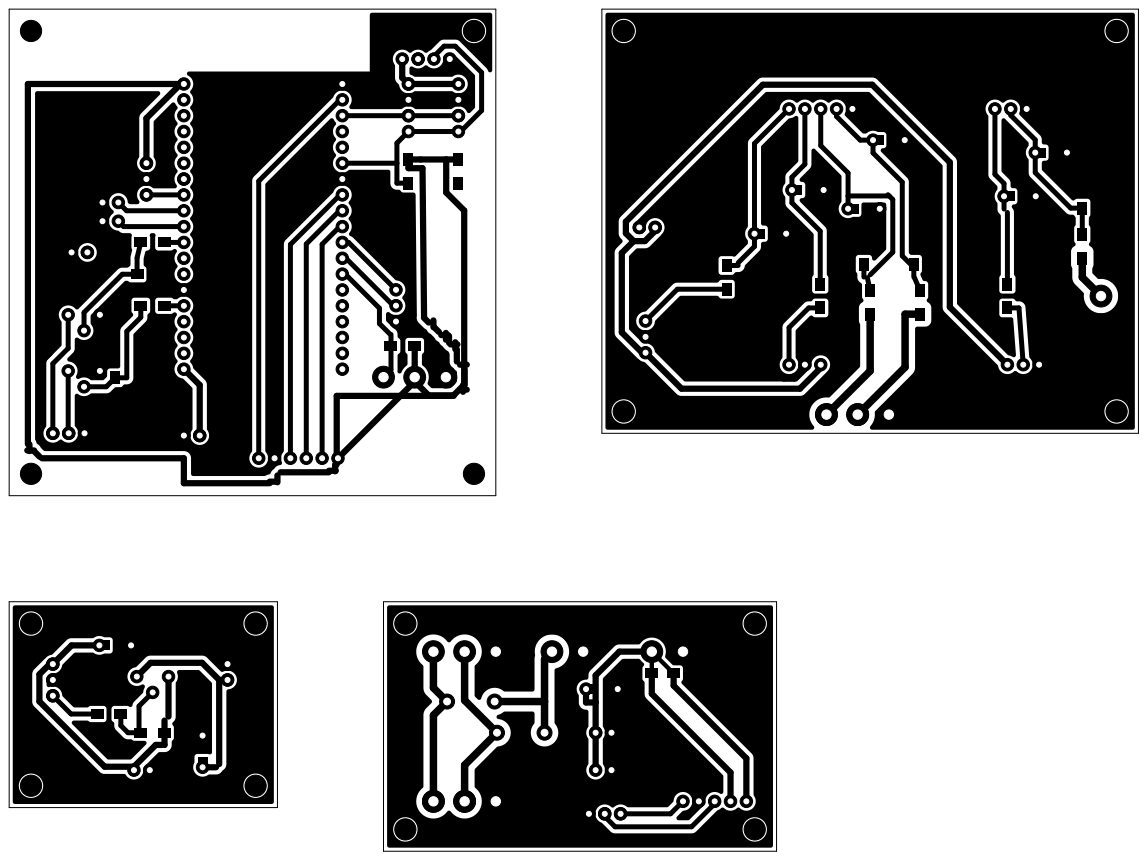
[picture p120: page 1]
