sql-monk/batman/hardware/batman/reports/clean-routing/staged/output/copper-mirrored.pdf

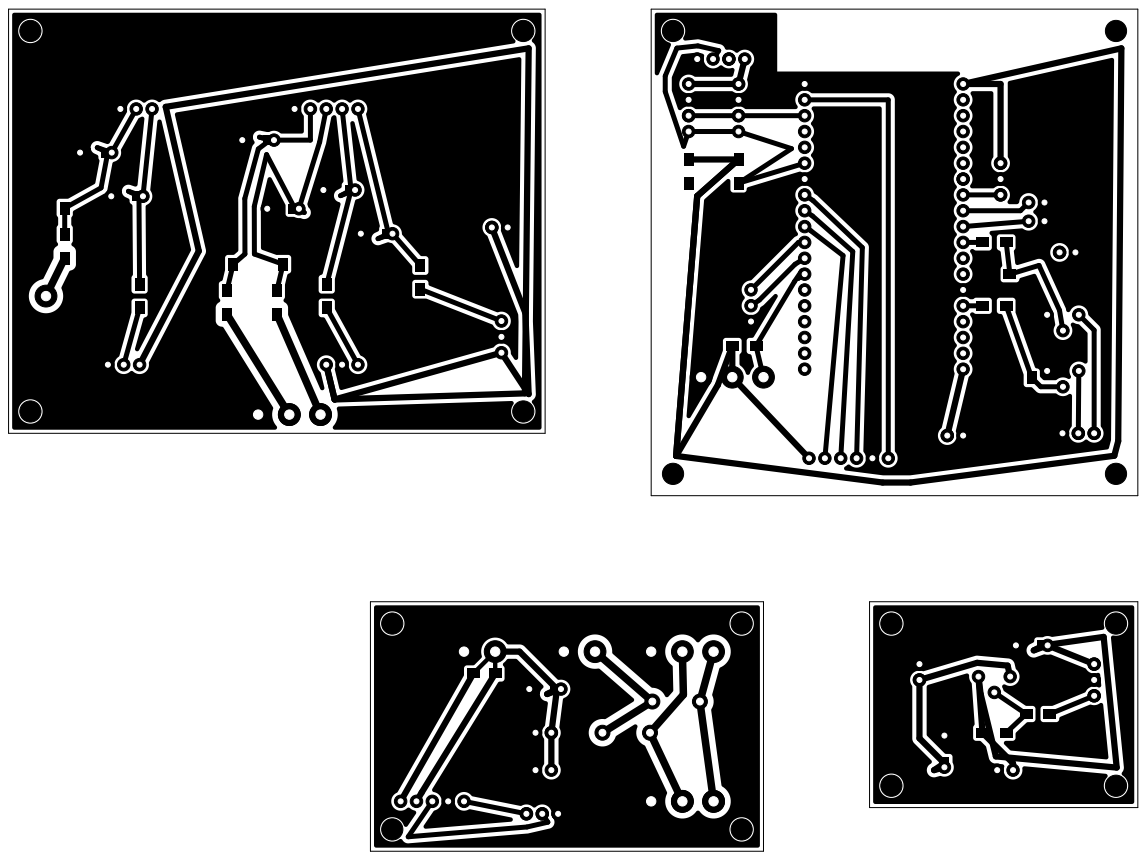
[picture p121: page 1]
