sql-monk/batman/hardware/batman/reports/clean-routing/staged/output/copper-top-view.pdf

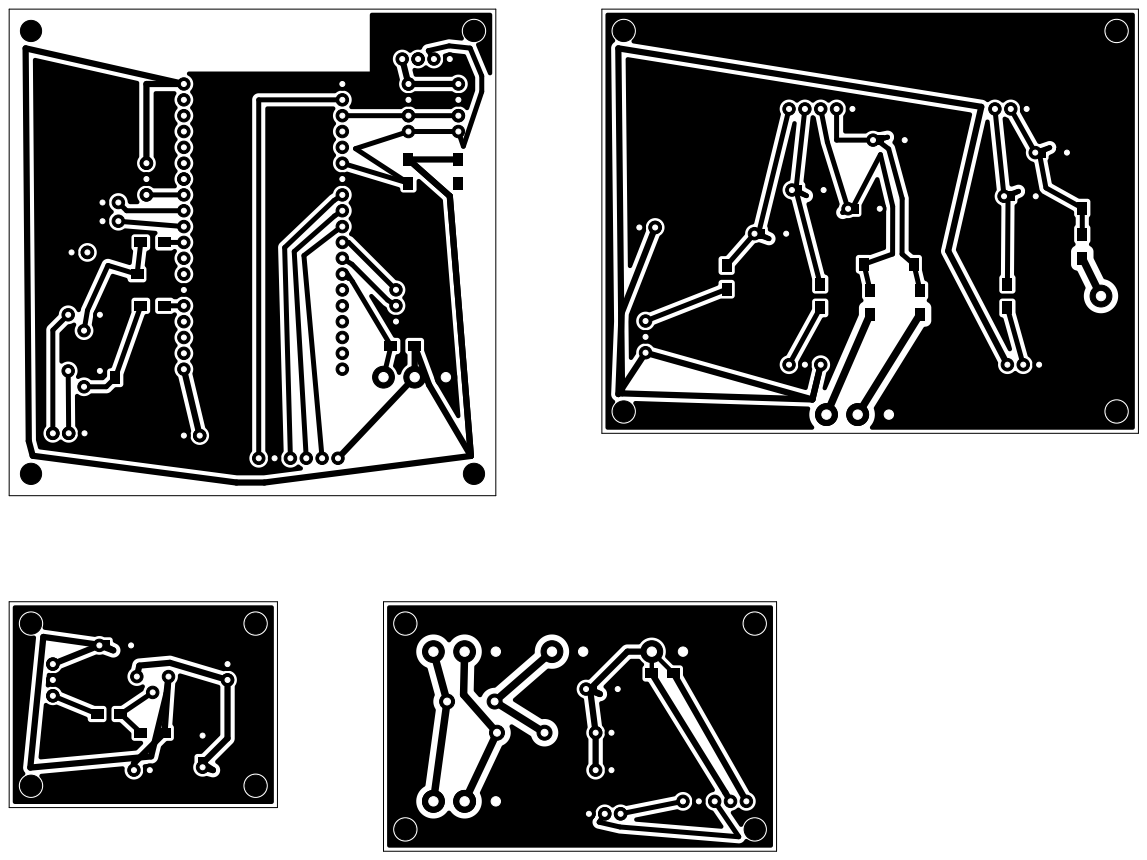
[picture p122: page 1]
