sql-monk/batman/hardware/batman/reports/gpio33/before-publish-20260909-184347/output/assembly.pdf

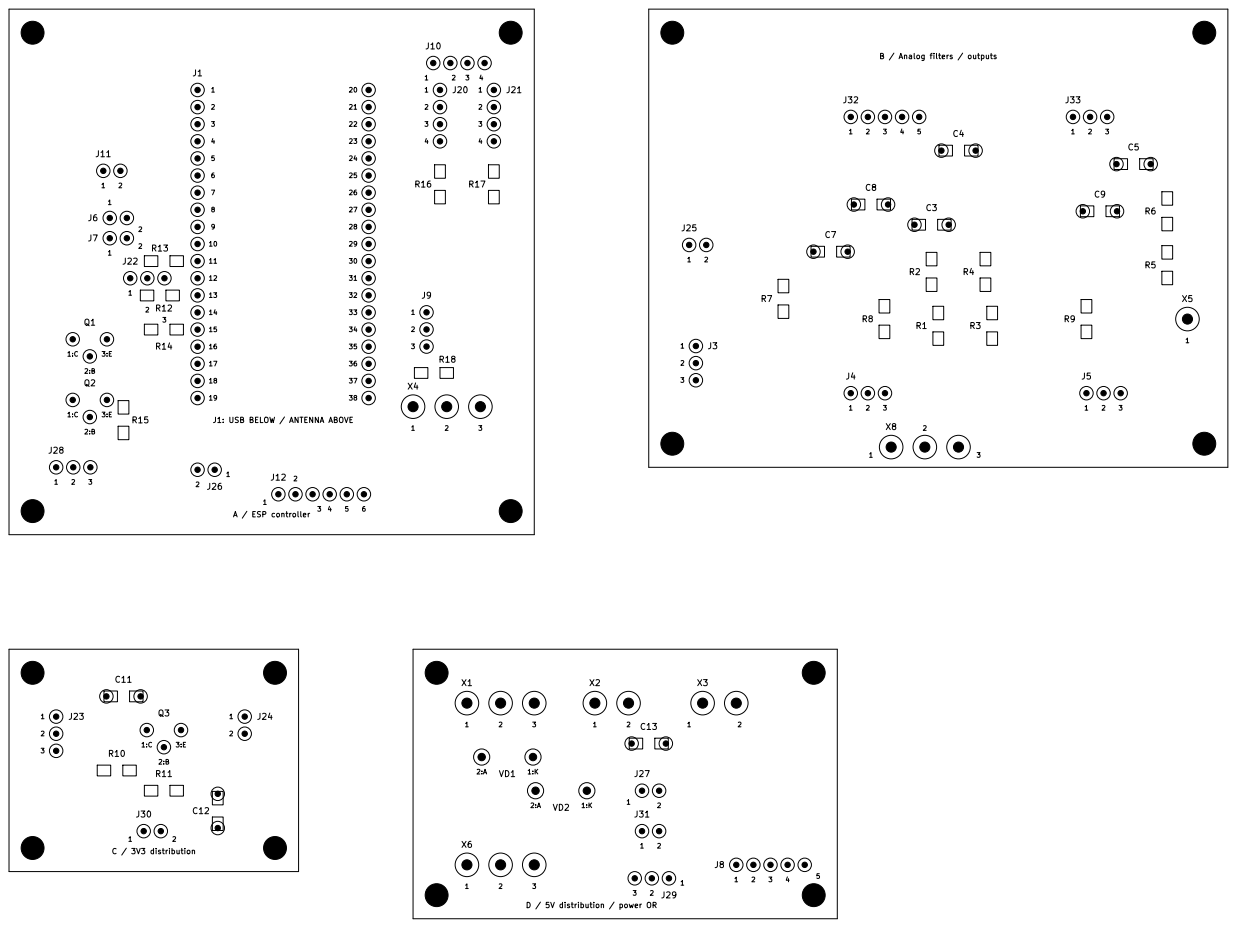
[picture p123: page 1]
