sql-monk/batman/hardware/batman/reports/gpio33/before-publish-20260909-184347/output/component-labels.pdf

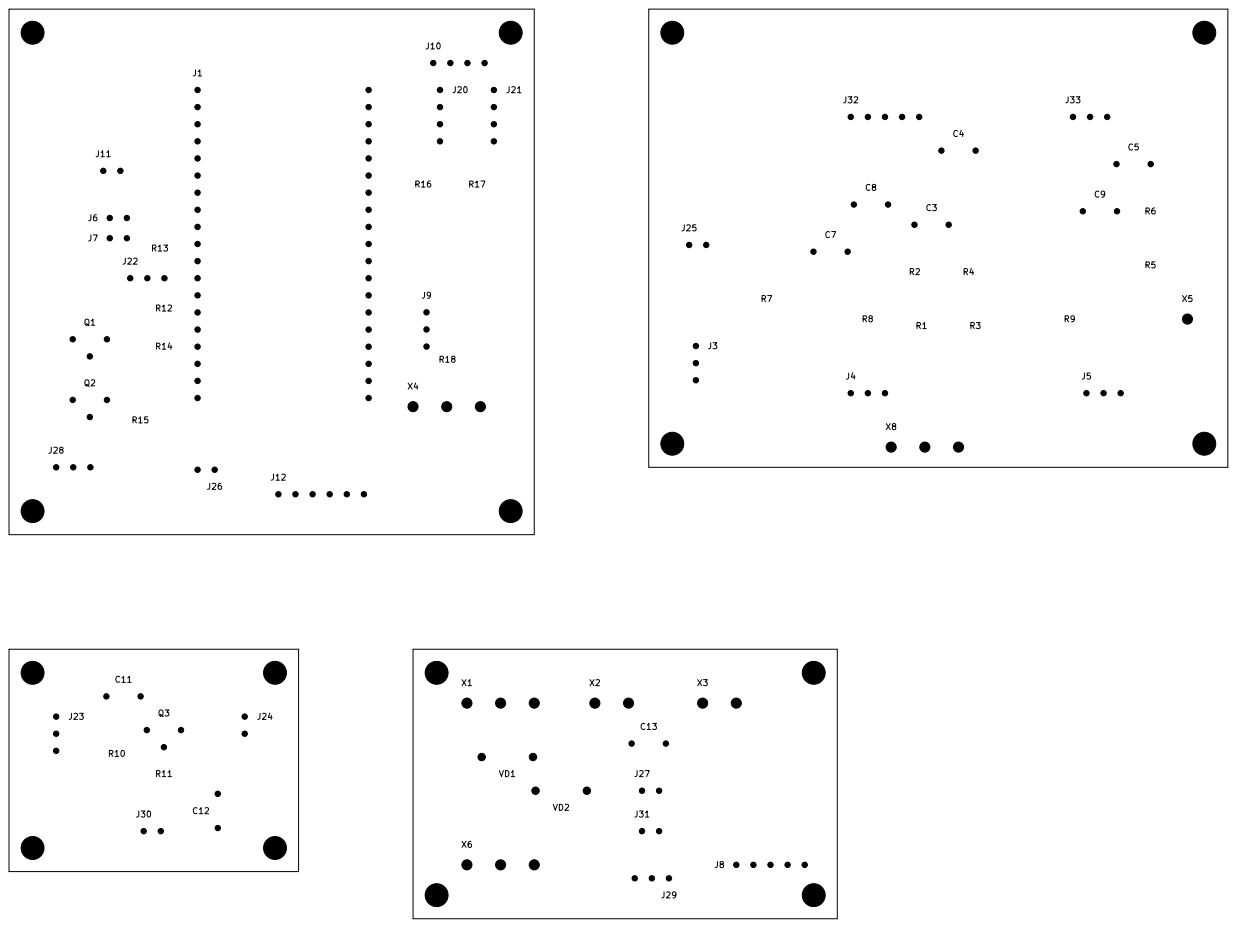
[picture p124: page 1]
