sql-monk/batman/hardware/batman/reports/gpio33/before-publish-20260909-184347/output/copper-mirrored.pdf

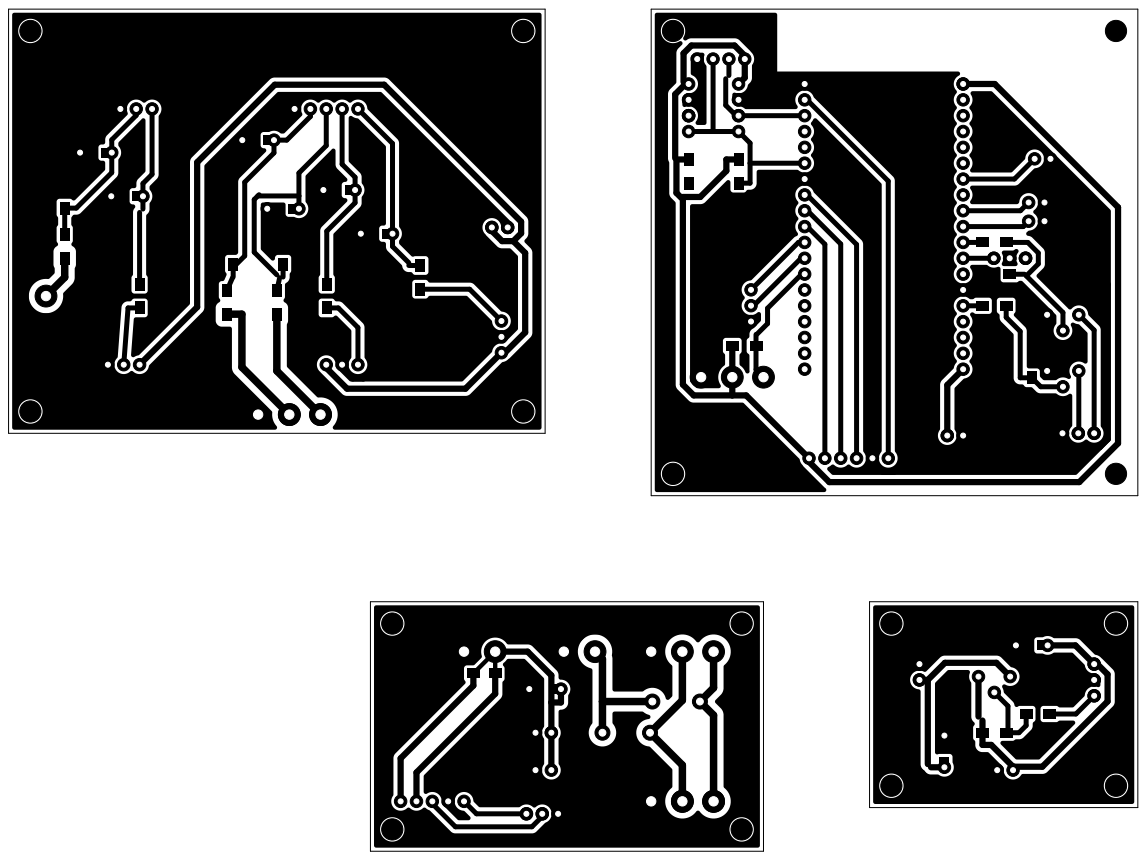
[picture p125: page 1]
