sql-monk/batman/hardware/batman/reports/gpio33/before-publish-20260909-184347/output/copper-top-view.pdf

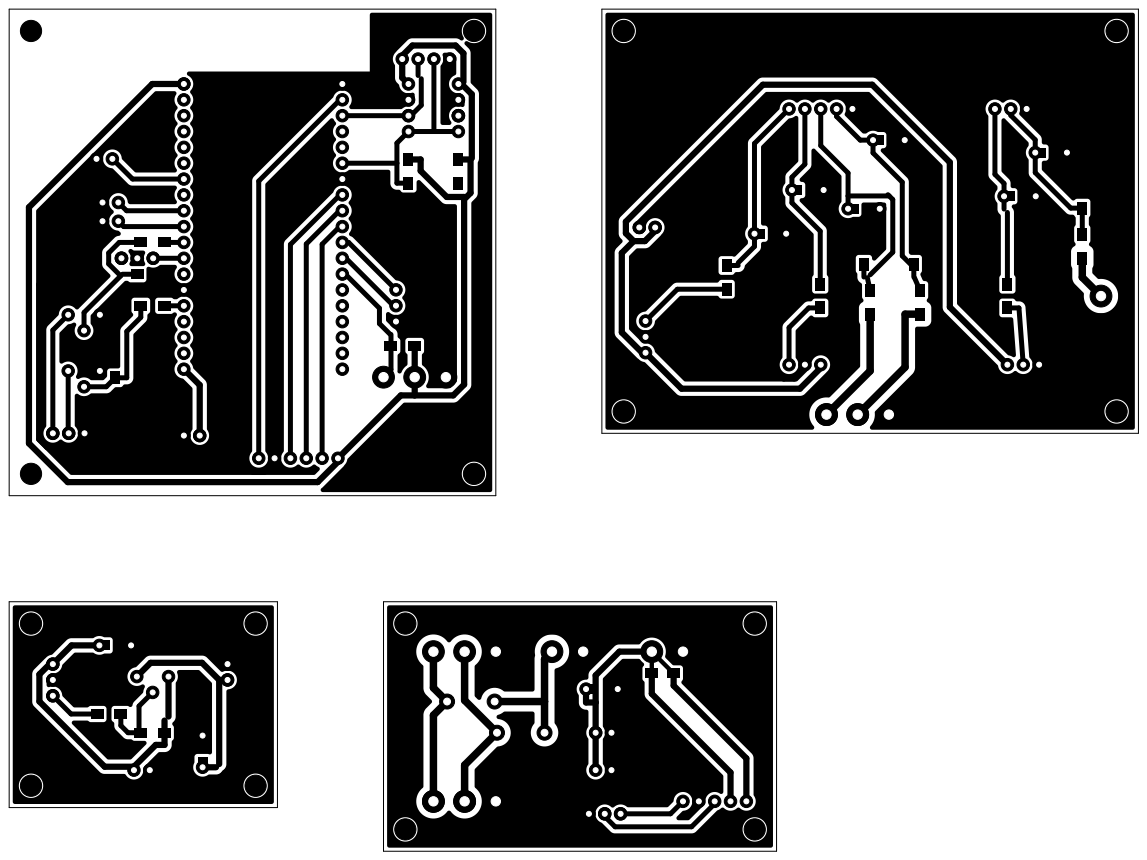
[picture p126: page 1]
