sql-monk/batman/hardware/batman/reports/gpio33/before-publish-20260909-184347/output/wiring.pdf

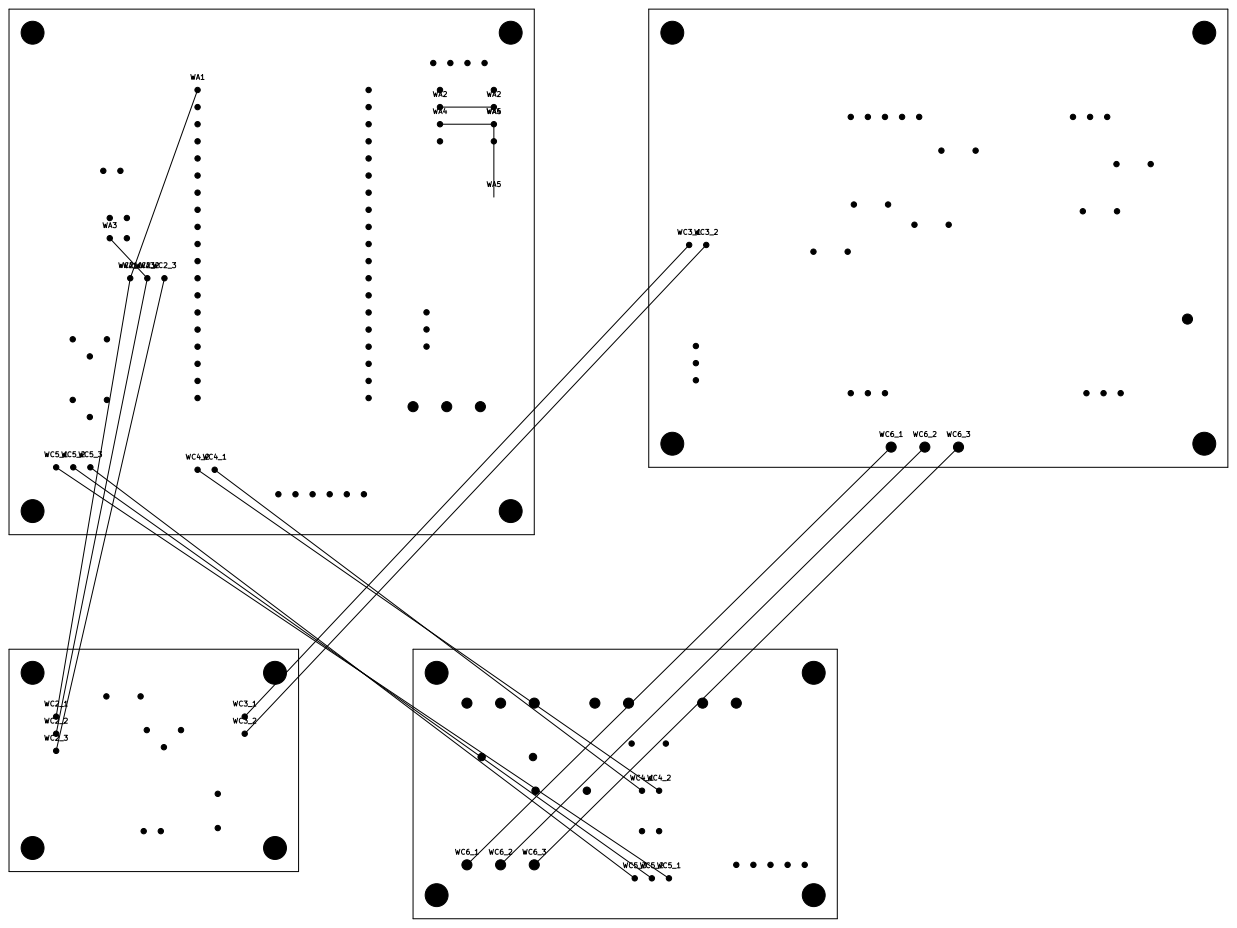
[picture p127: page 1]
