sql-monk/batman/hardware/batman/reports/refinement/before-publish-20260909-170518/output/assembly.pdf

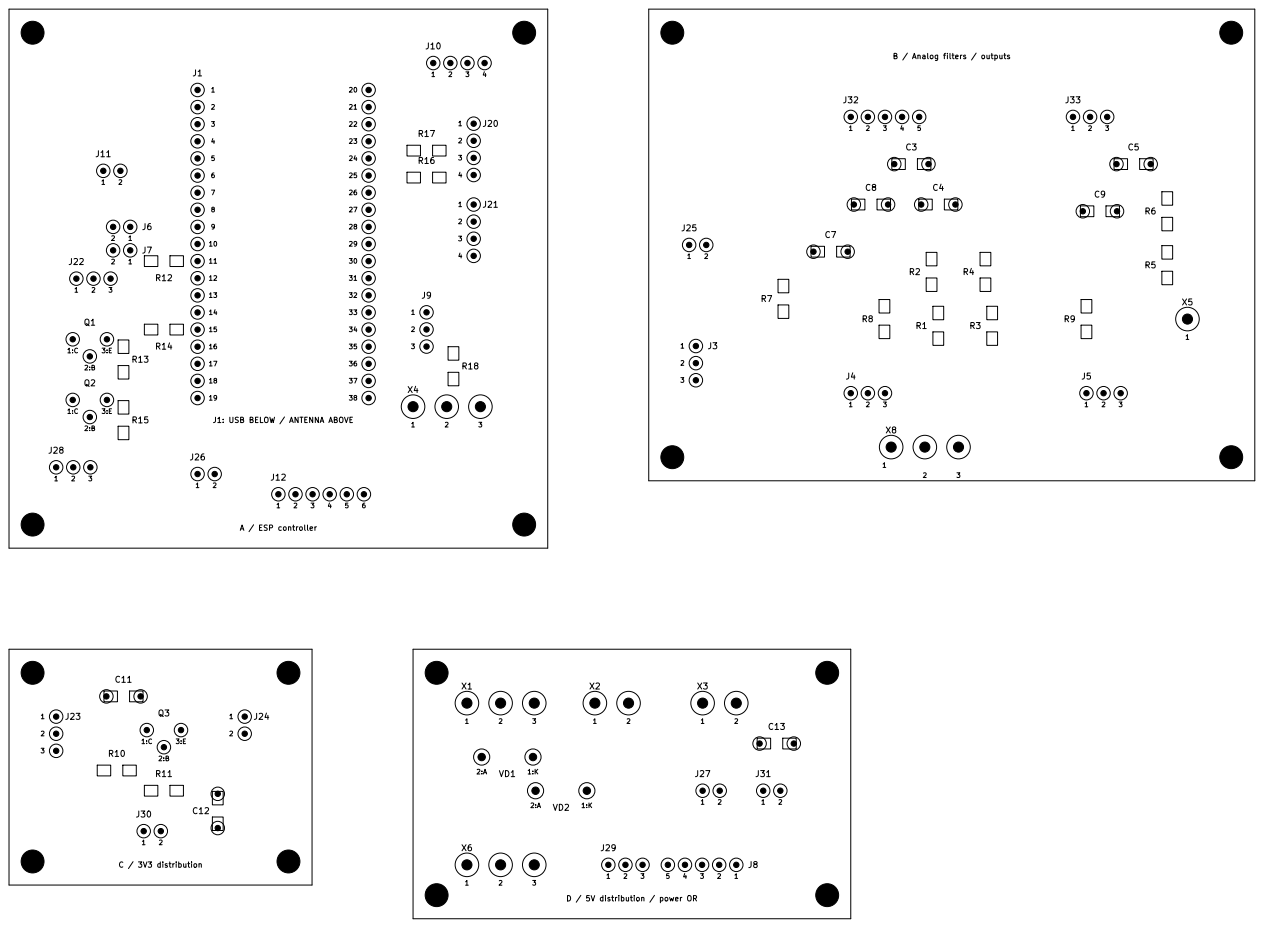
[picture p128: page 1]
