sql-monk/batman/hardware/batman/reports/refinement/before-publish-20260909-170518/output/component-labels.pdf

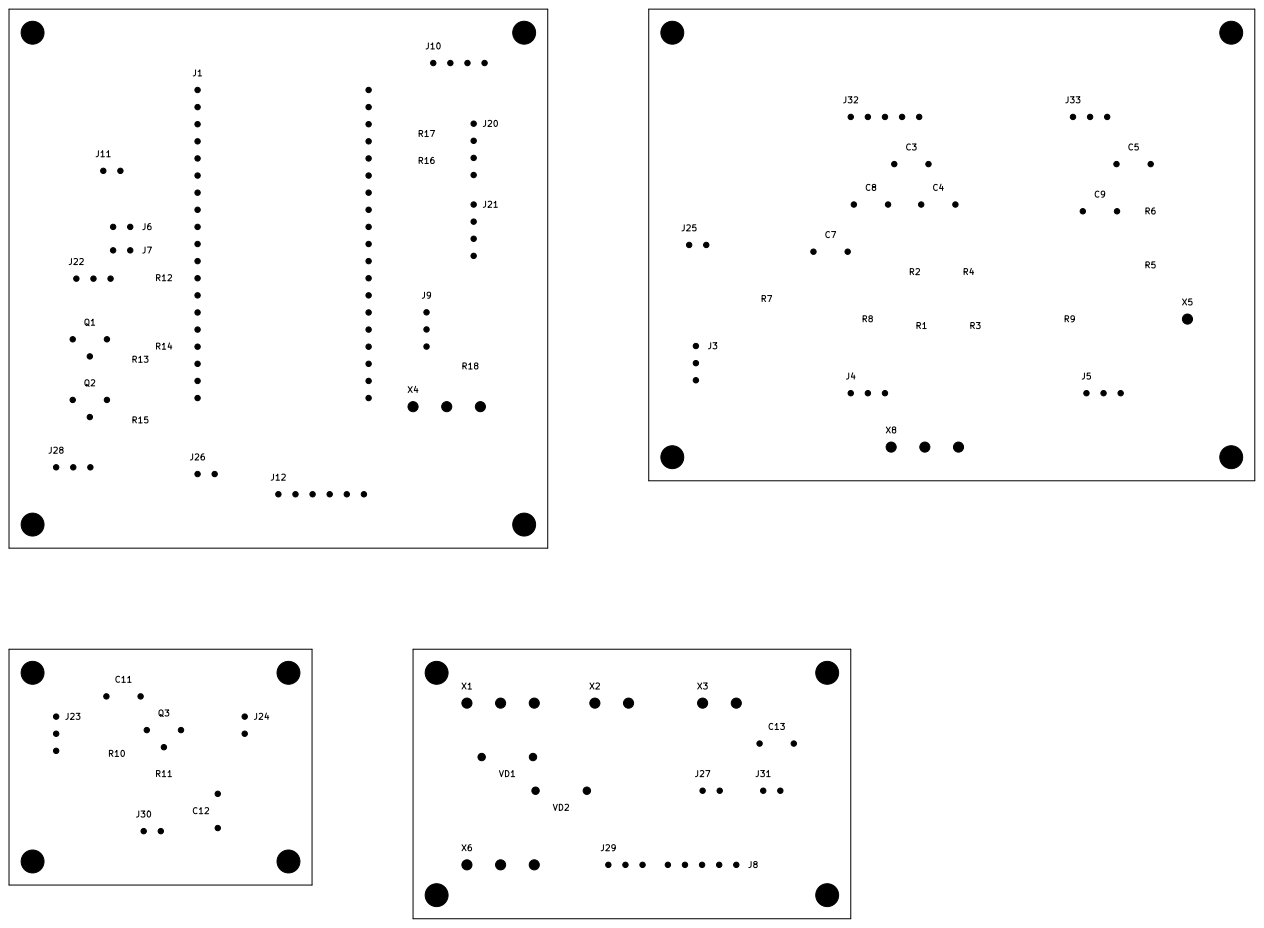
[picture p129: page 1]
