sql-monk/batman/hardware/batman/reports/refinement/before-publish-20260909-170518/output/copper-mirrored.pdf

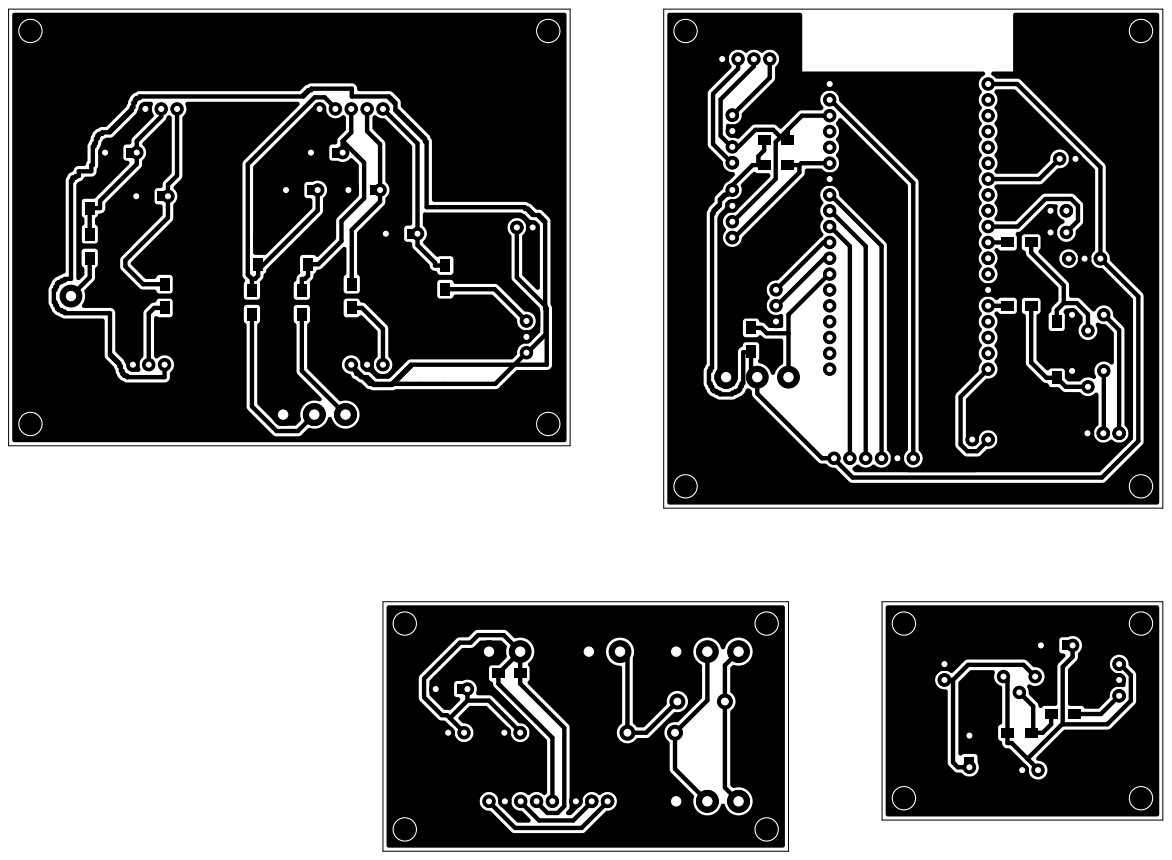
[picture p130: page 1]
