sql-monk/batman/hardware/batman/reports/refinement/before-publish-20260909-170518/output/copper-top-view.pdf

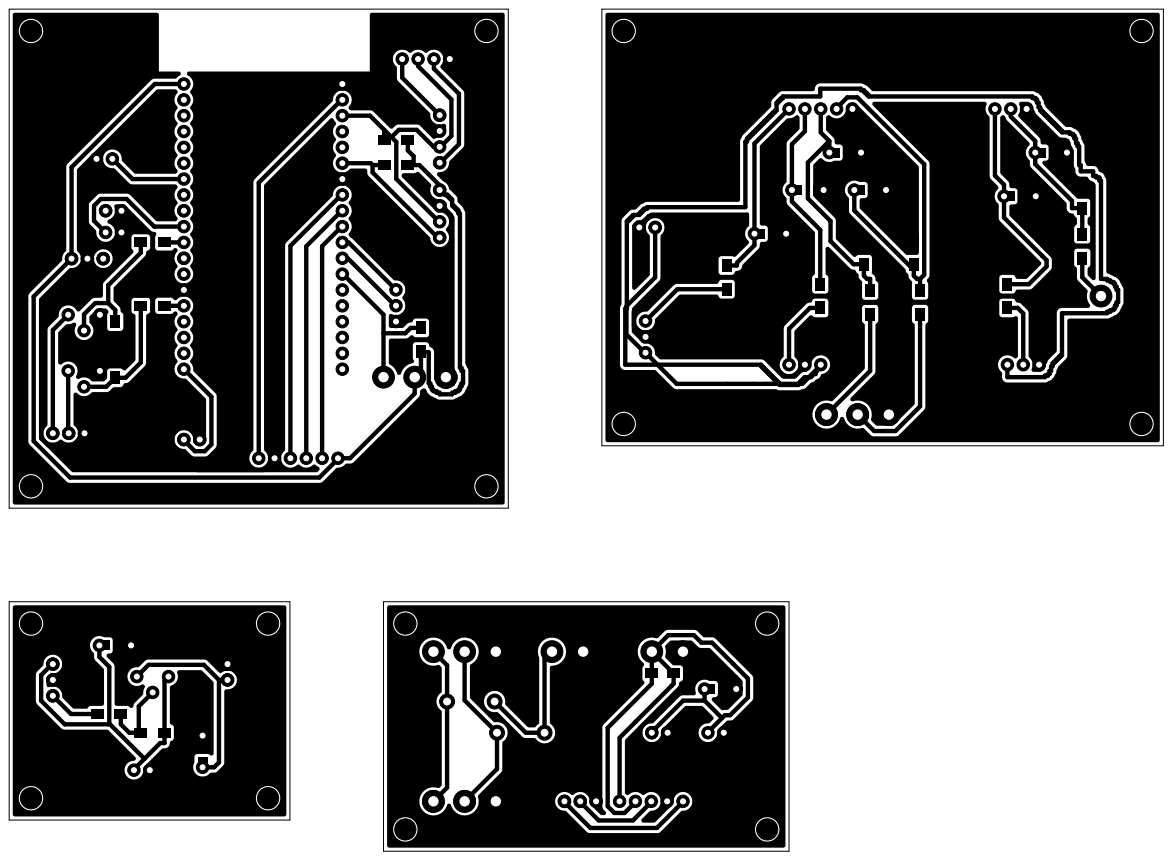
[picture p131: page 1]
