sql-monk/batman/hardware/batman/reports/refinement/before-publish-20260909-170518/output/wiring.pdf

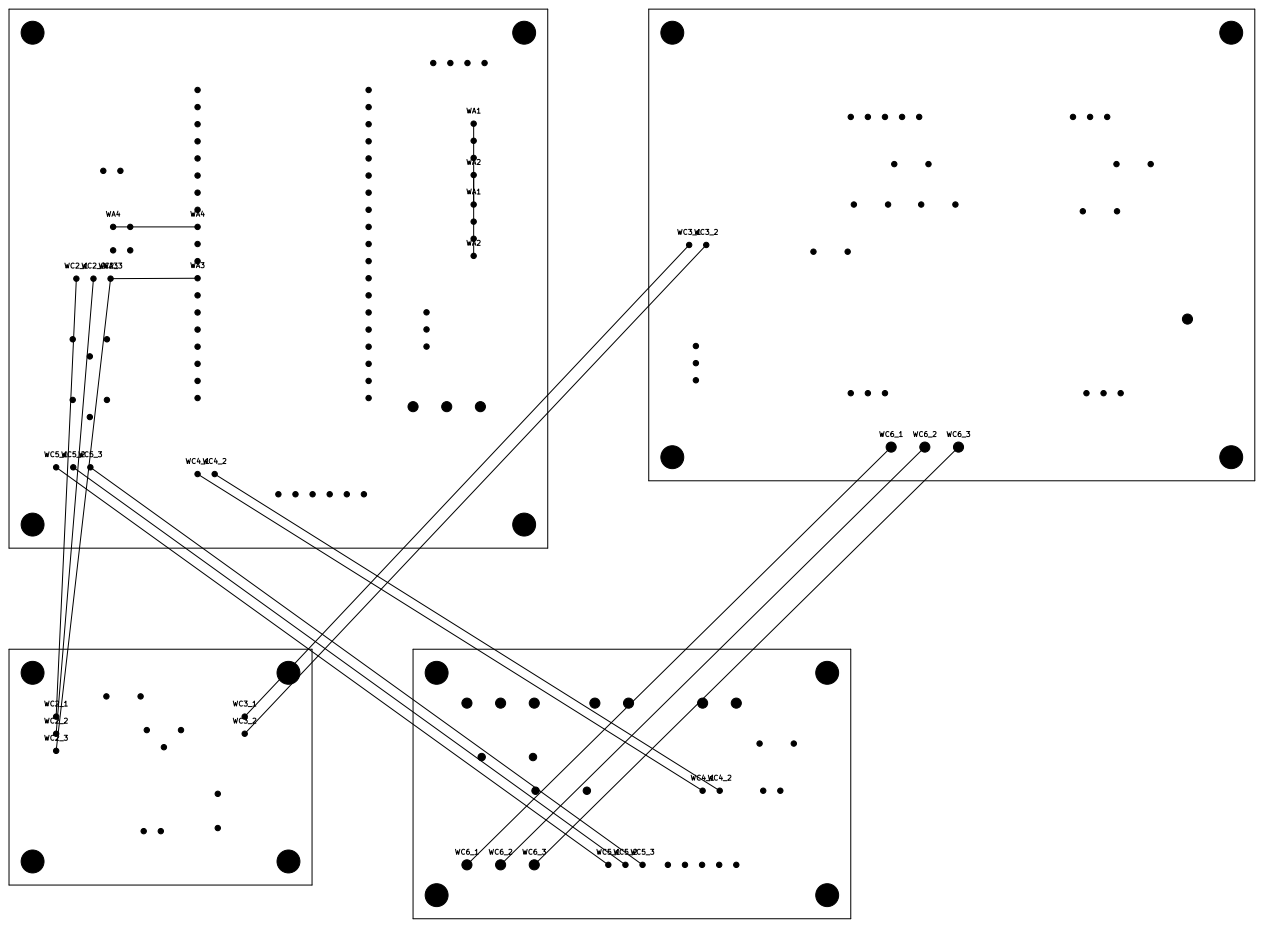
[picture p132: page 1]
