sql-monk/batman/hardware/batman/reports/clean-routing/before-publish-20260909-212552/output/A/copper-mirrored.pdf

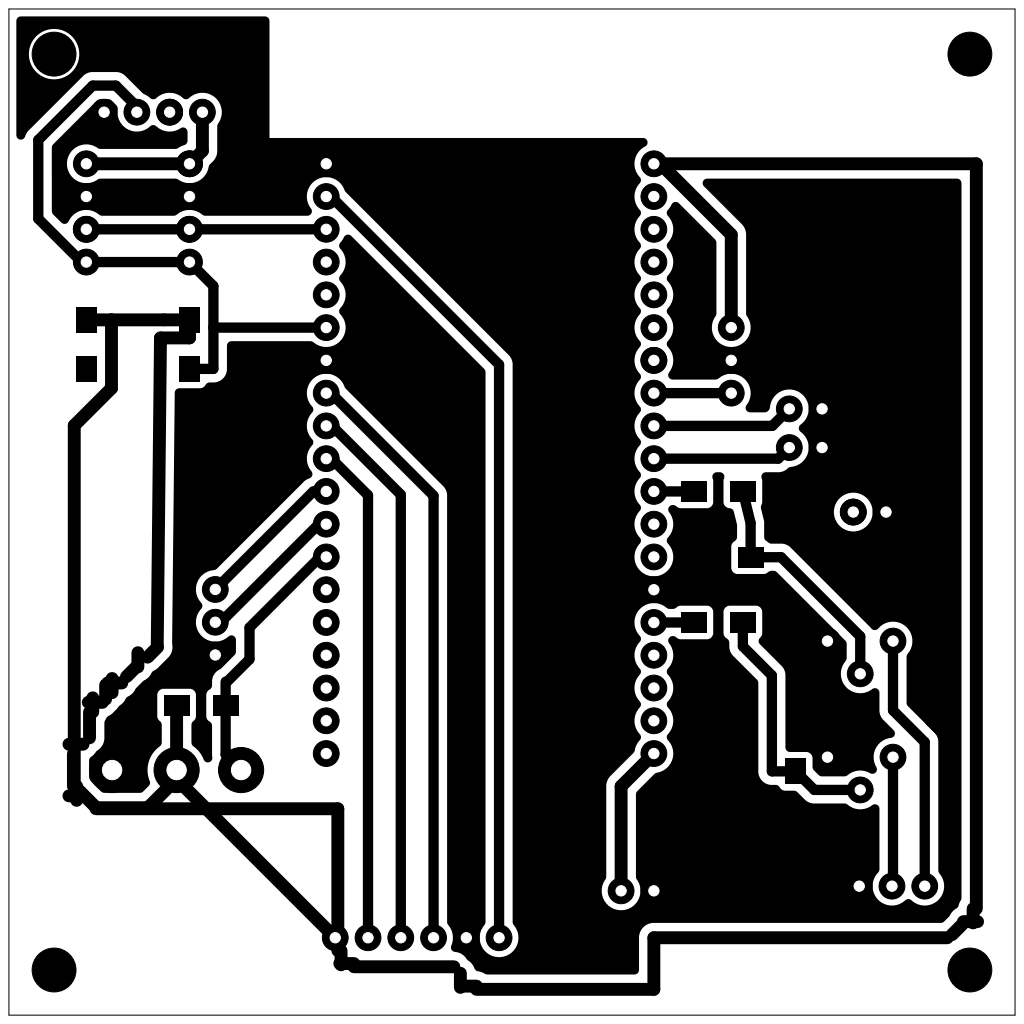
[picture p133: page 1]
