sql-monk/batman/hardware/batman/reports/clean-routing/before-publish-20260909-212552/output/A/copper-top-view.pdf

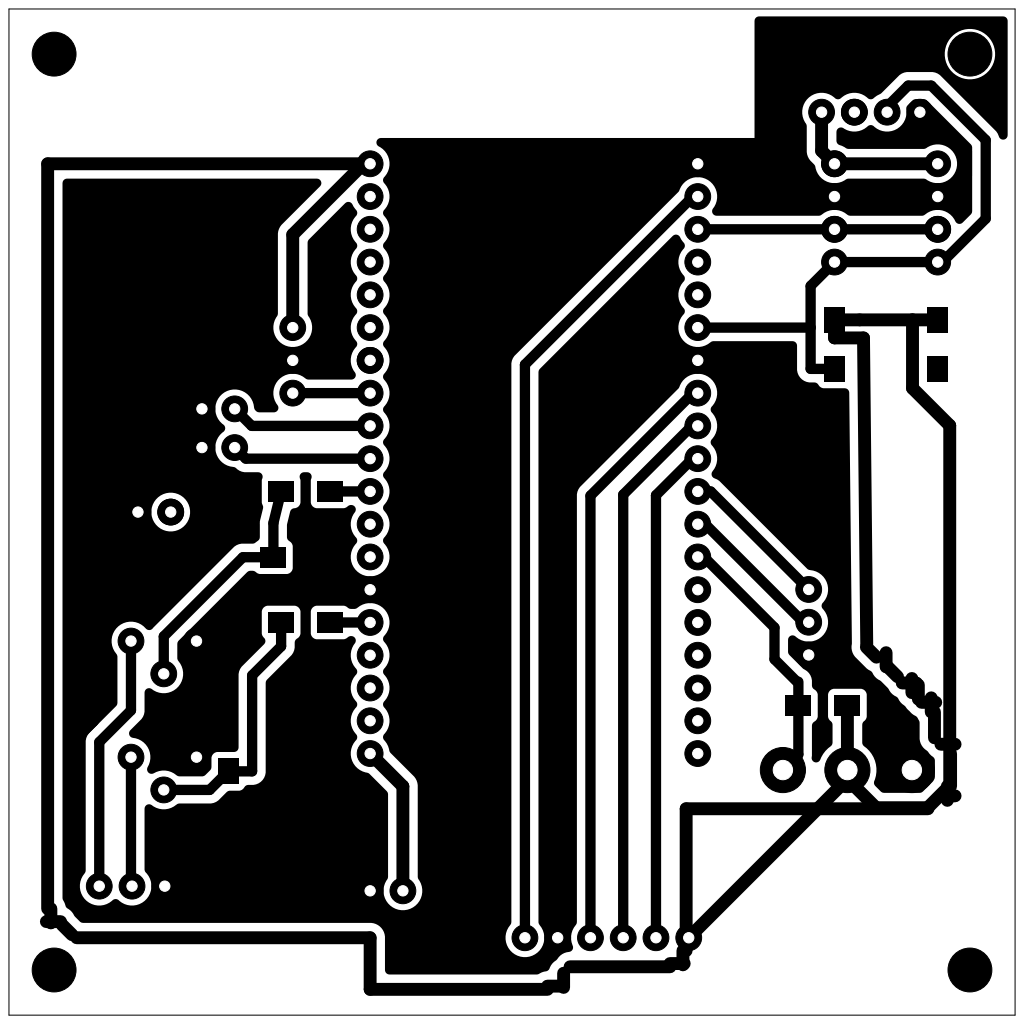
[picture p134: page 1]
