sql-monk/batman/hardware/batman/reports/clean-routing/before-publish-20260909-212552/output/A/wiring.pdf

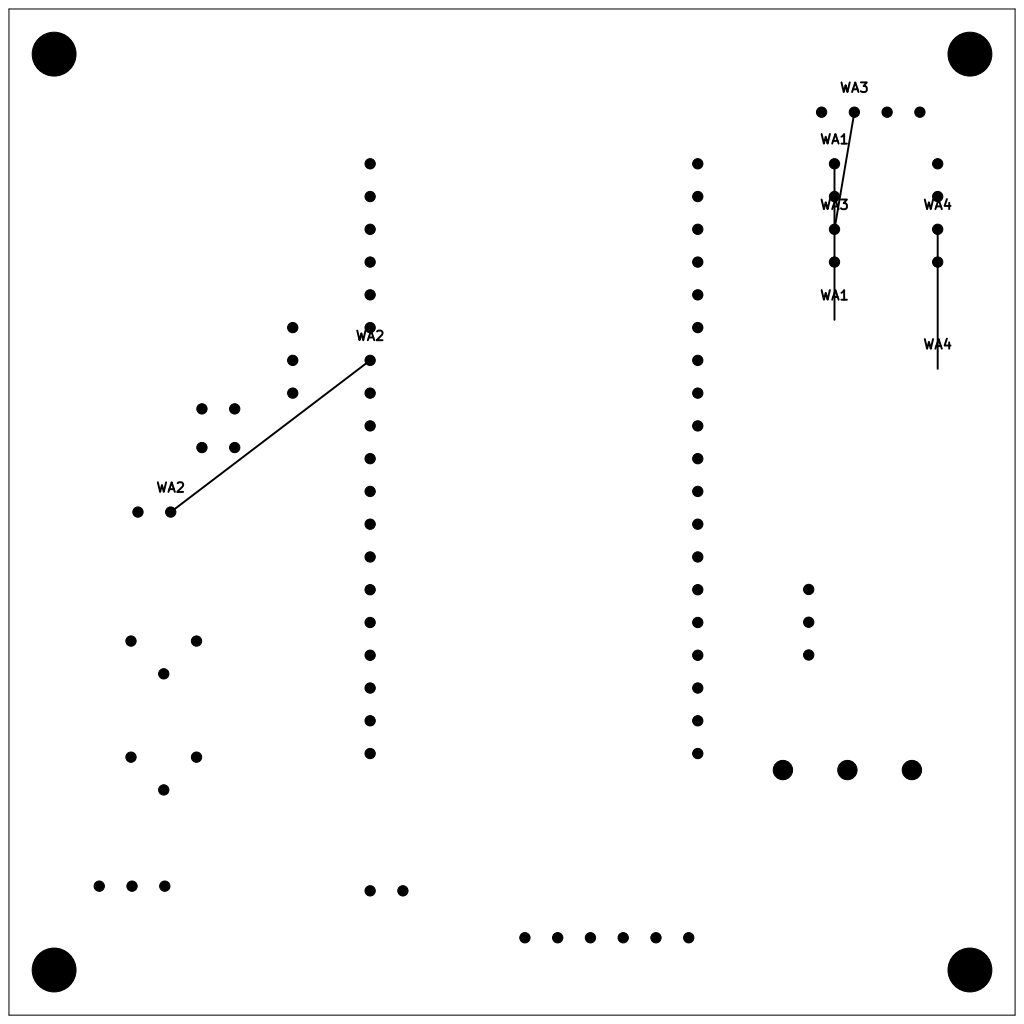
[picture p135: page 1]
