sql-monk/batman/hardware/batman/reports/clean-routing/before-publish-20260909-212552/output/B/assembly.pdf

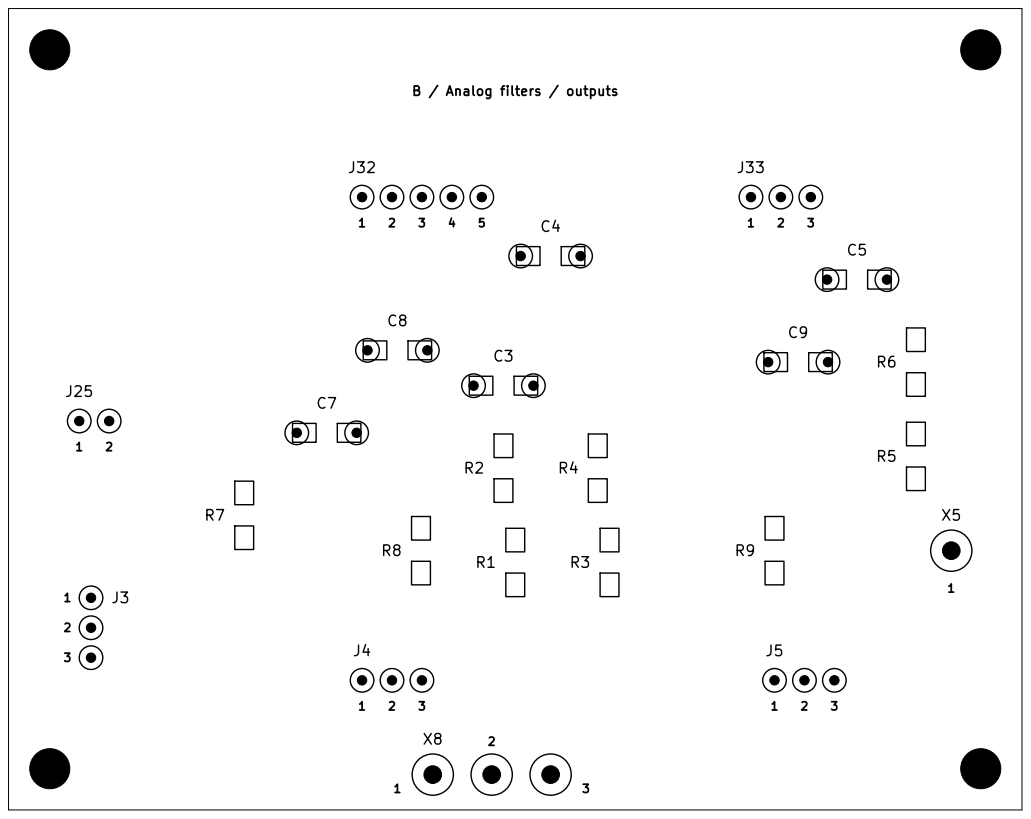
[picture p136: page 1]
