sql-monk/batman/hardware/batman/reports/clean-routing/before-publish-20260909-212552/output/B/copper-mirrored.pdf

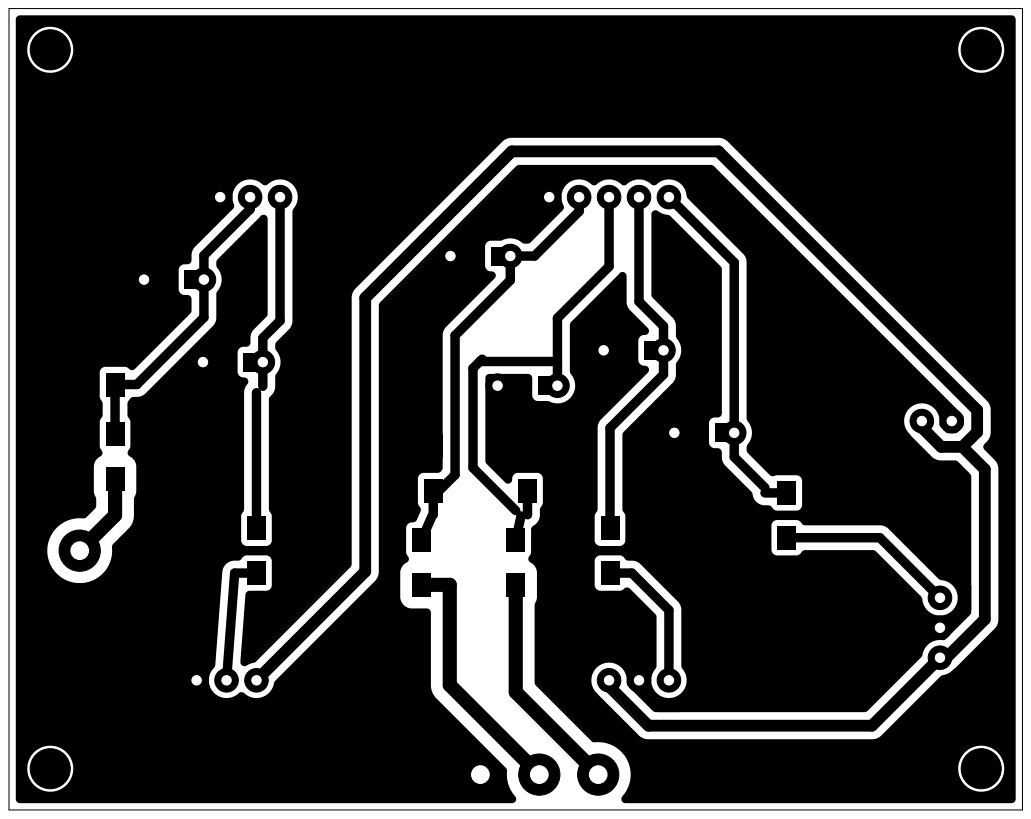
[picture p137: page 1]
