sql-monk/batman/hardware/batman/reports/clean-routing/before-publish-20260909-212552/output/B/copper-top-view.pdf

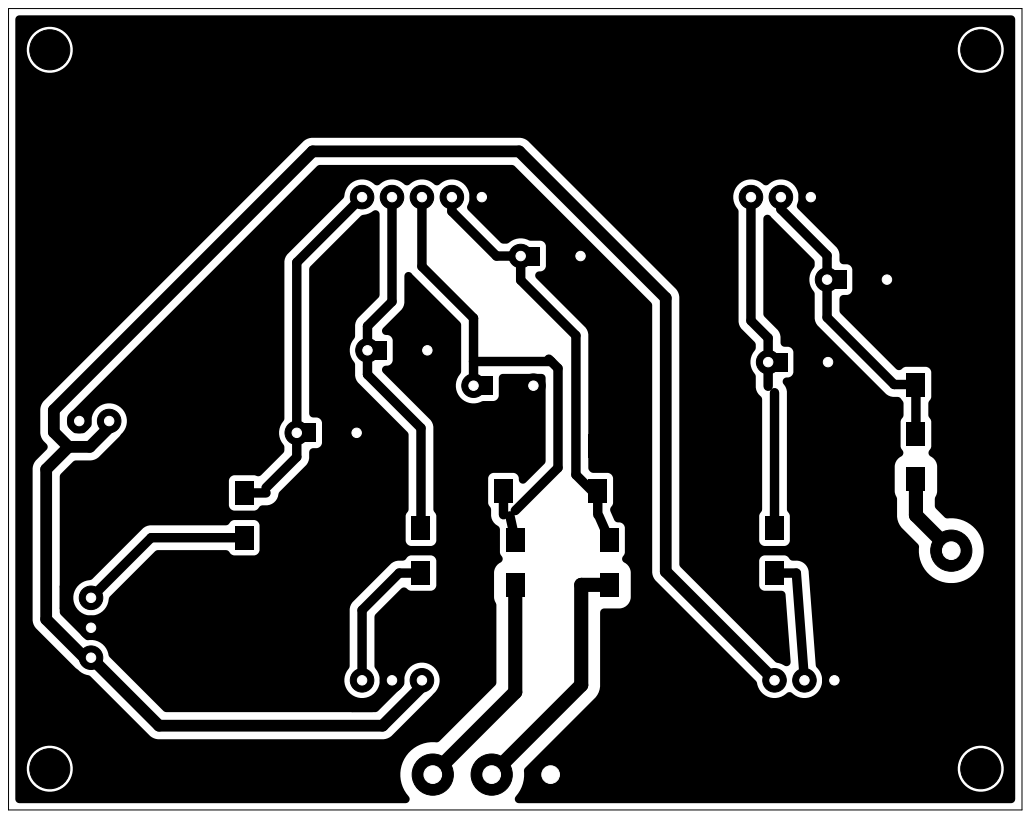
[picture p138: page 1]
