sql-monk/batman/hardware/batman/reports/clean-routing/before-publish-20260909-212552/reports/C/candidate.kicad_pcb

## KiCad design hardware/batman/reports/clean-routing/before-publish-20260909-212552/reports/C/candidate.kicad_pcb (2026-09-09)

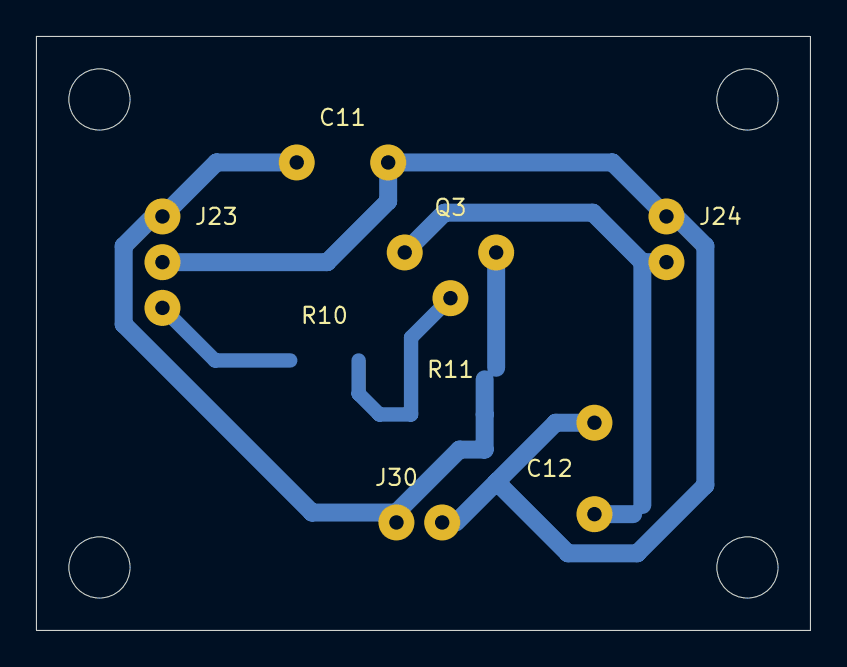
[picture p141: board hardware/batman/reports/clean-routing/before-publish-20260909-212552/… from above]

Board: 2 copper layers, 43.0 x 33.0 mm, 12 parts (0 on the bottom side), 5 nets.

Parts:
C11: 100n_16V; LUT_C11
C12: 100n_16V; LUT_C12
HC1, HC2, HC3, HC4: M3_NPTH_3.4; Mount_M3
J23: LINK_+3V3_GND_SENS_PWR; LUT_J23
J24: LINK_GND_+3V3_SENS; LUT_J24
J30: LINK_+3V3_GND; LUT_J30
Q3: BC557_CBE; LUT_Q3
R10: 4.7k; LUT_R10
R11: 10k; LUT_R11

Connections:
+3V3: C11.1, J23.1, J30.1, Q3.3, R11.2
+3V3_SENS: C12.1, J24.2, Q3.1
BASE3: Q3.2, R10.2, R11.1
GND: C11.2, C12.2, J23.2, J24.1, J30.2
SENS_PWR: J23.3, R10.1
